raonslab2/fcBoardKicad/out/hierarchical_board/report.md

# HierarchicalBoard Build Report

**Generated:** 2025-12-12 09:06:19
**KiCad Version:** 9

## Summary

| Metric | Count |
|---|---|
| Total Parts | 13 |
| Active Parts | 11 |
| DNP Parts | 2 |
| With LCSC # | 4 |
| With MPN | 3 |

## Parts by Type

| Type | Count |
|---|---|
| C | 4 |
| D | 1 |
| J | 2 |
| L | 1 |
| R | 2 |
| U | 1 |

## Parts List

| Ref | Value | Role | LCSC | MPN | DNP |
|-----|---|---|---|-----|-----|
| C1 | 220uF | capacitor_pol | C134799 | - |  |
| C2 | 220uF | capacitor_pol | C134799 | - |  |
| C3 | 100nF | capacitor | - | - |  |
| C4 | 10uF | capacitor | - | - |  |
| D1 | SS34 | diode | - | - |  |
| D2 | Green | led | - | - | Yes |
| J1 | DC Jack 12V | input_conn | - | - |  |
| J2 | USB-A | usb_a | - | - |  |
| L1 | 33uH | inductor | - | - |  |
| R1 | 1k | resistor | - | - | Yes |
| R2 | 22R | resistor | C17560 | RC0402FR-0722RL |  |
| R3 | 22R | resistor | C17560 | RC0402FR-0722RL |  |
| U1 | LM2596S-5.0 | buck_5v | - | LM2596S-5.0/NOPB |  |

## DNP Parts (Do Not Populate)

| Ref | Value | Role |
|-----|---|---|
| D2 | Green | led |
| R1 | 1k | resistor |

## Hierarchical Sheets

| Sheet | Parts | Ports |
|---|---|---|
| Power | 8 | +12V, +5V, +3V3... |
| USB | 5 | +5V, GND, USB_DP... |
