raonslab2/fcBoardKicad/out/hierarchical_ports_obj/report.md

# HierarchicalPortsObj Build Report

**Generated:** 2025-12-12 09:22:37
**Builder Version:** 1.3.0
**KiCad Version:** 9

## Summary

| Metric | Count |
|---|---|
| Total Parts | 7 |
| Active Parts | 7 |
| DNP Parts | 0 |
| With LCSC # | 2 |
| With MPN | 1 |

## Parts by Type

| Type | Count |
|---|---|
| C | 3 |
| J | 1 |
| R | 2 |
| U | 1 |

## Parts List

| Ref | Value | Role | LCSC | MPN | DNP |
|-----|---|---|---|-----|-----|
| C1 | 220uF | capacitor_pol | - | - |  |
| C2 | 220uF | capacitor_pol | - | - |  |
| C3 | 100nF | capacitor | - | - |  |
| J1 | DC Jack | input_conn | - | - |  |
| R1 | 10k | resistor | C17414 | - |  |
| R2 | 10k | resistor | C17414 | - |  |
| U1 | LM2596S-5.0 | buck_5v | - | LM2596S-5.0/NOPB |  |

## Hierarchical Sheets

| Sheet | Parts | Ports |
|---|---|---|
| Power | 4 | +12V, GND, +5V... |
| Digital | 3 | +5V, +3V3, GND... |
