raonslab2/fcBoardKicad/docs/ACU5EV/ACU5EV_Schematic.pdf

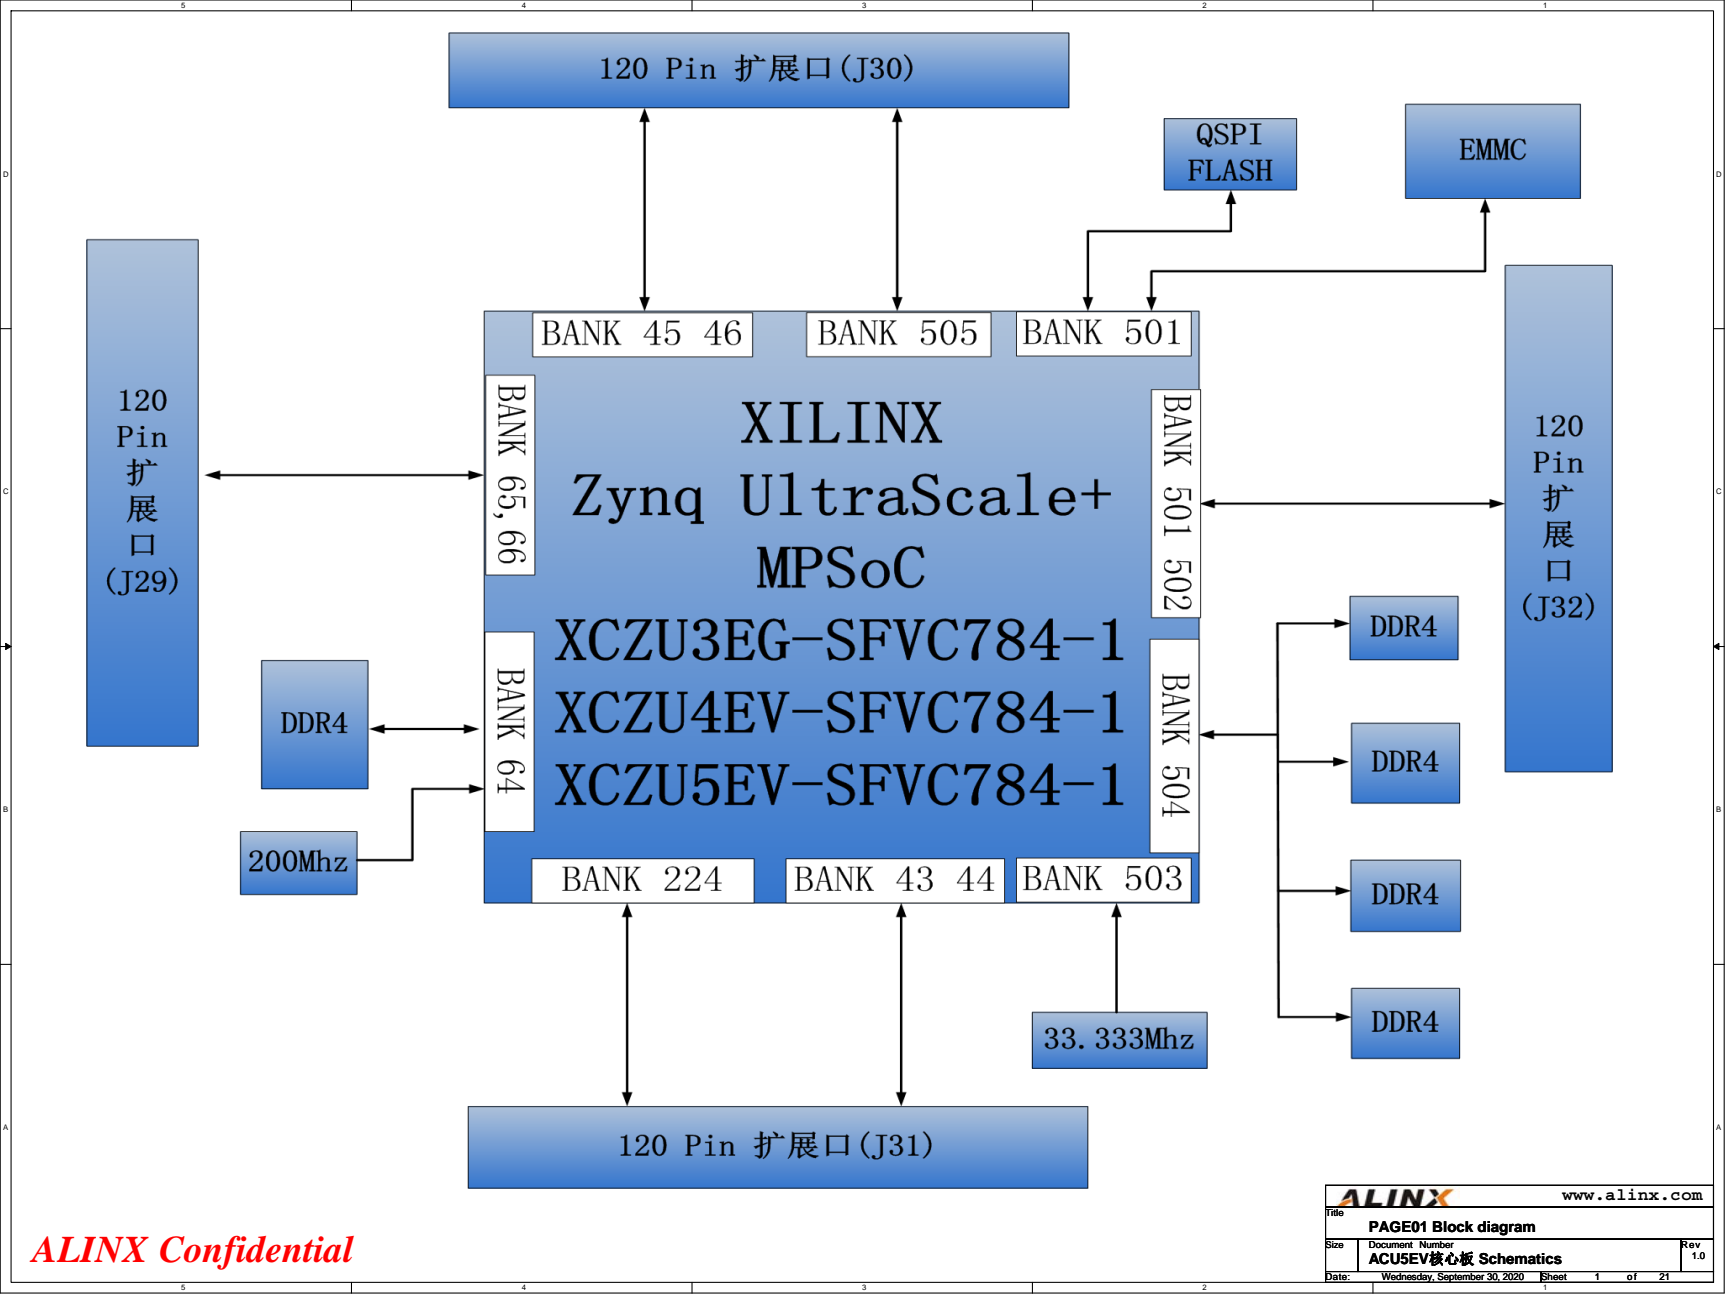
[picture p16: page 1]
ALINX Confidential; Title; PAGE01 Block diagram

www.alinx.com

Size | Document Number ACU5EV核心板 Schematics | Rev 1.0

Date: Wednesday, September 30, 2020 Wednesday, September 30, 2020 Wednesday, September 30, 2020 | Sheet 1 1 1 of 21 21 21

# MODE[3:0]

0000 | PS JTAG | PS JTAG Interface

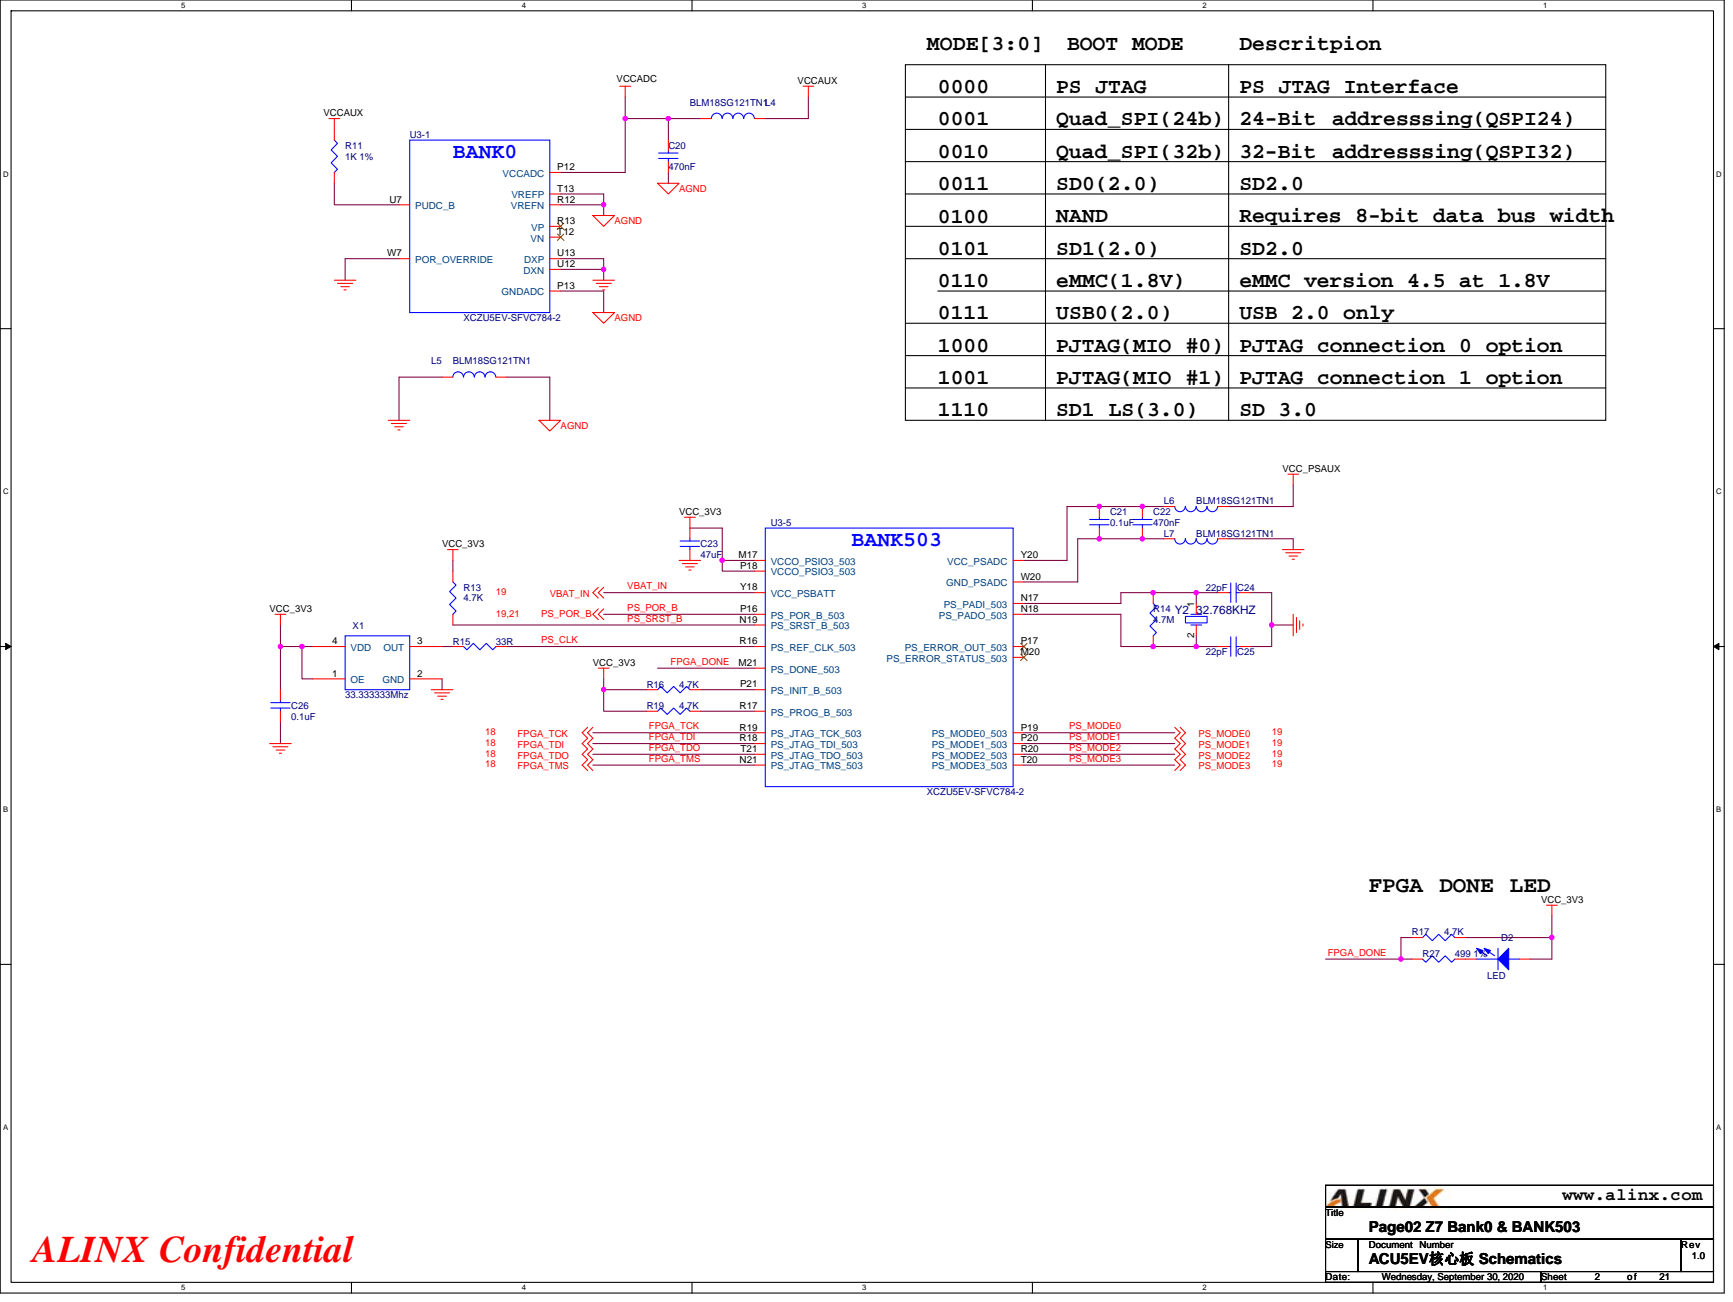
[picture p17: page 2]

0001 | Quad_SPI(24b) | 24-Bit addresssing(QSPI24)
0010 | Quad_SPI(32b) | 32-Bit addresssing(QSPI32)
0011 | SD0(2.0) | SD2.0
0100 | NAND | Requires 8-bit data bus width
0101 | SD1(2.0) | SD2.0
0110 0111 | eMMC(1.8V) USB0(2.0) | eMMC version 4.5 at 1.8V USB 2.0 only

1000 | PJTAG(MIO #0) | PJTAG connection 0 option
1001 | PJTAG(MIO #1) | PJTAG connection 1 option
1110 | SD1 LS(3.0) | SD 3.0

## VCC1V8

0.1uF | BANK500

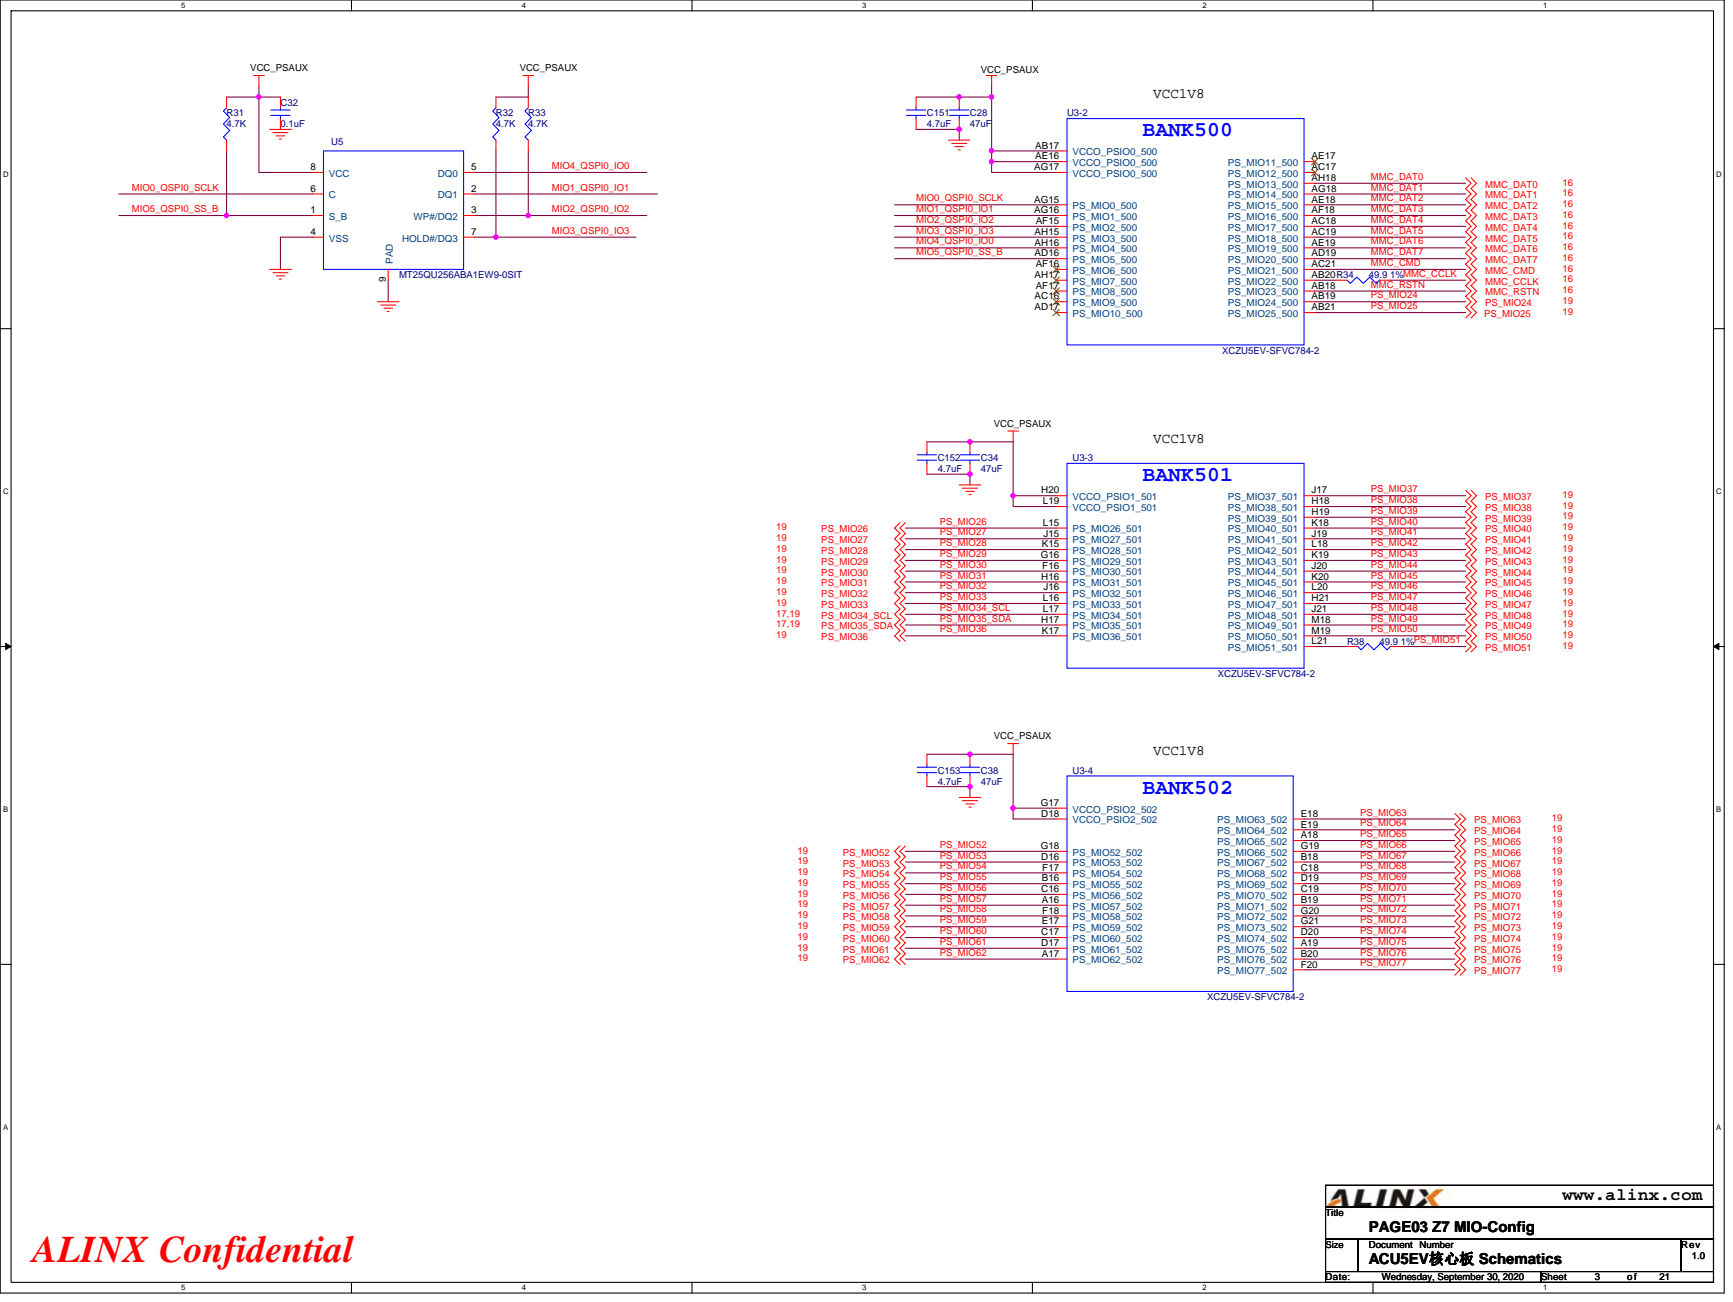
[picture p18: page 3]

# BANK43

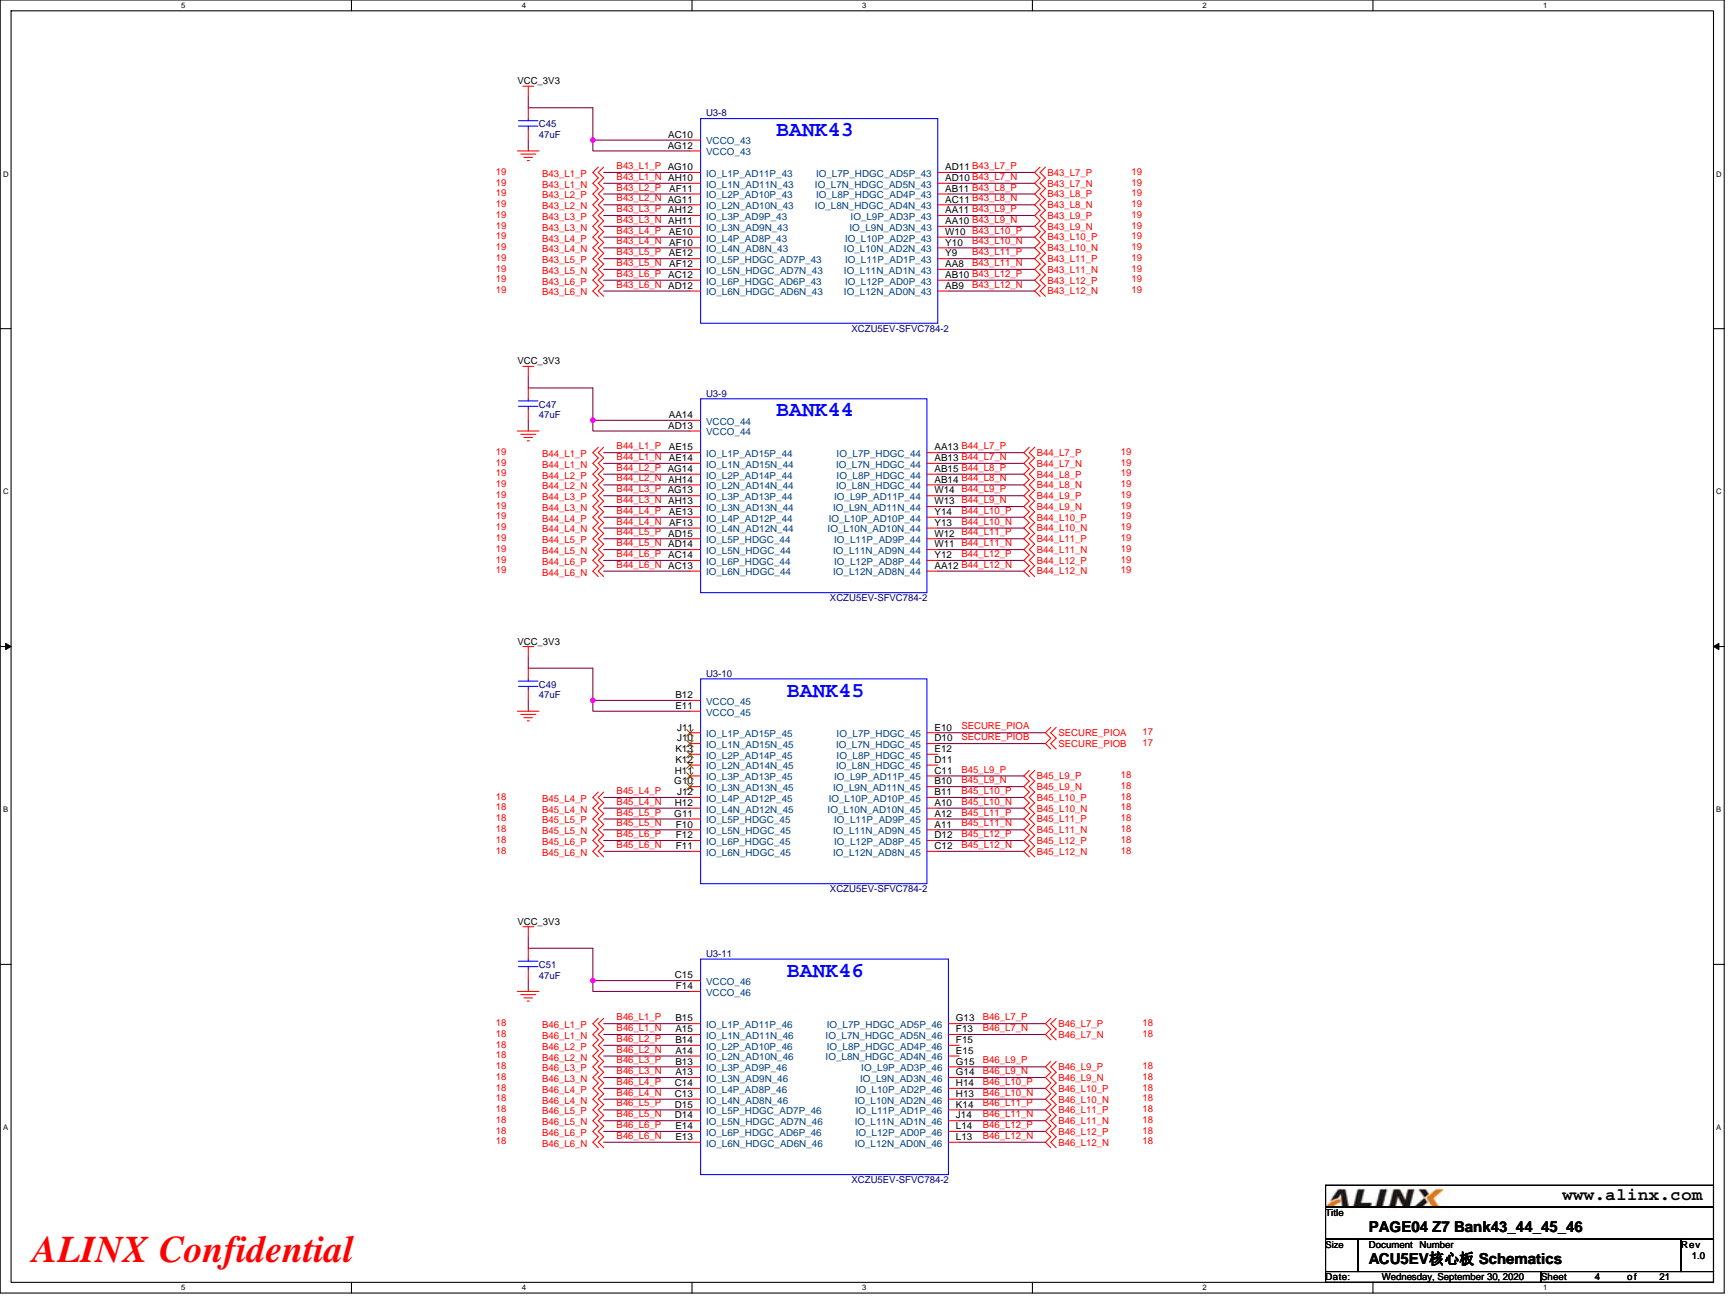
[picture p19: page 4]

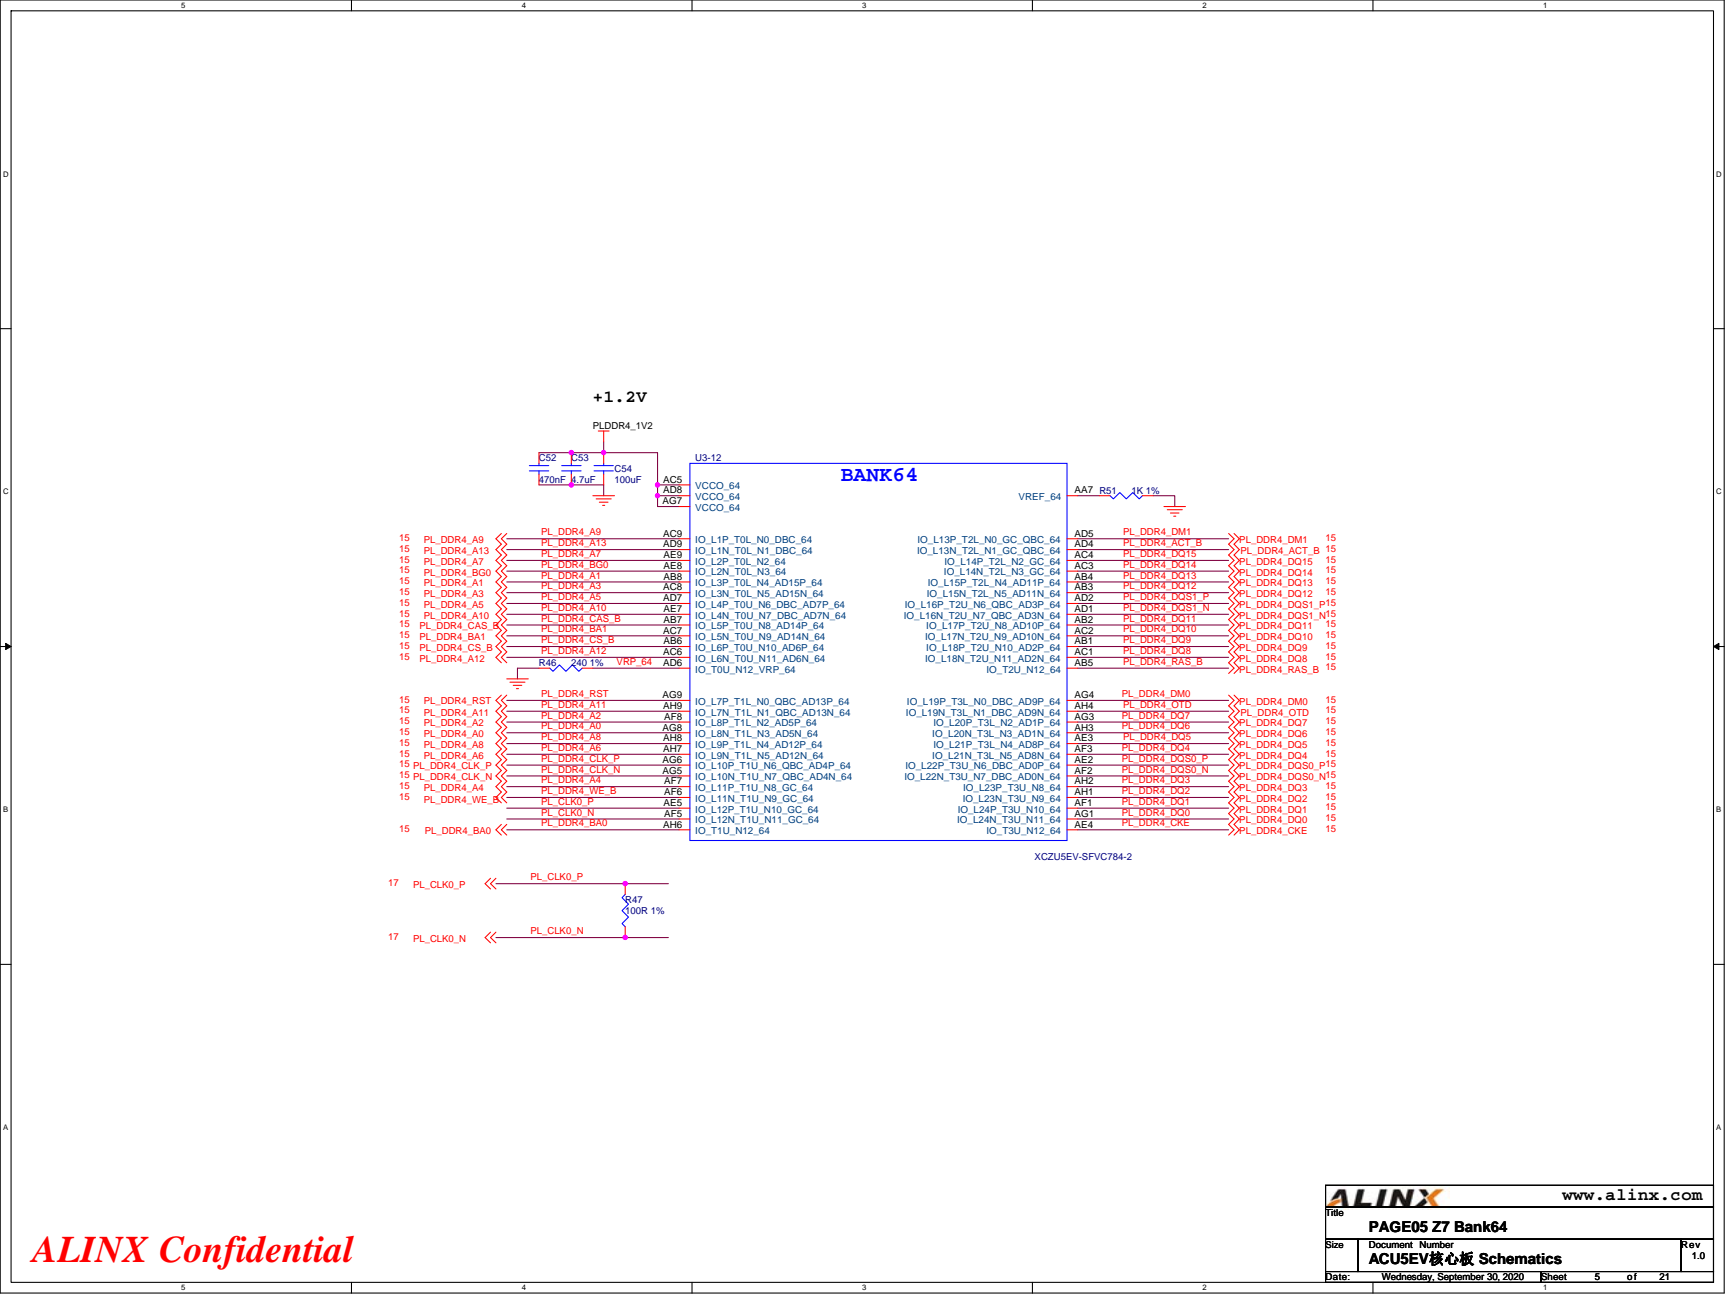
[picture p20: page 5]
VRP_64; PL_DDR4_A0; PL_DDR4_CLK_P PL_DDR4_CLK_N; PL_CLK0_P PL_CLK0_N; PL_CLK0_N; PL_CLK0_P; PL_DDR4_DM1; PL_DDR4_DQ0; PL_DDR4_DQ7 PL_DDR4_DQ6; PL_DDR4_DQS0_P; PL_DDR4_DQ1; PL_DDR4_DQS0_N; PL_DDR4_DQ2; PL_DDR4_DQ5 PL_DDR4_DQ4; PL_DDR4_DQ3; PL_DDR4_DM0; PL_DDR4_DQ15 PL_DDR4_DQ14 PL_DDR4_DQ13 PL_DDR4_DQ12; PL_DDR4_DQ11 PL_DDR4_DQ10 PL_DDR4_DQ9 PL_DDR4_DQ8; PL_DDR4_DQS1_P PL_DDR4_DQS1_N; PL_DDR4_OTD; PL_DDR4_A6; PL_DDR4_BA1; PL_DDR4_A9; PL_DDR4_A5; PL_DDR4_CS_B; PL_DDR4_BA0; PL_DDR4_A13 PL_DDR4_A7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

www.alinx.com

# BANK65

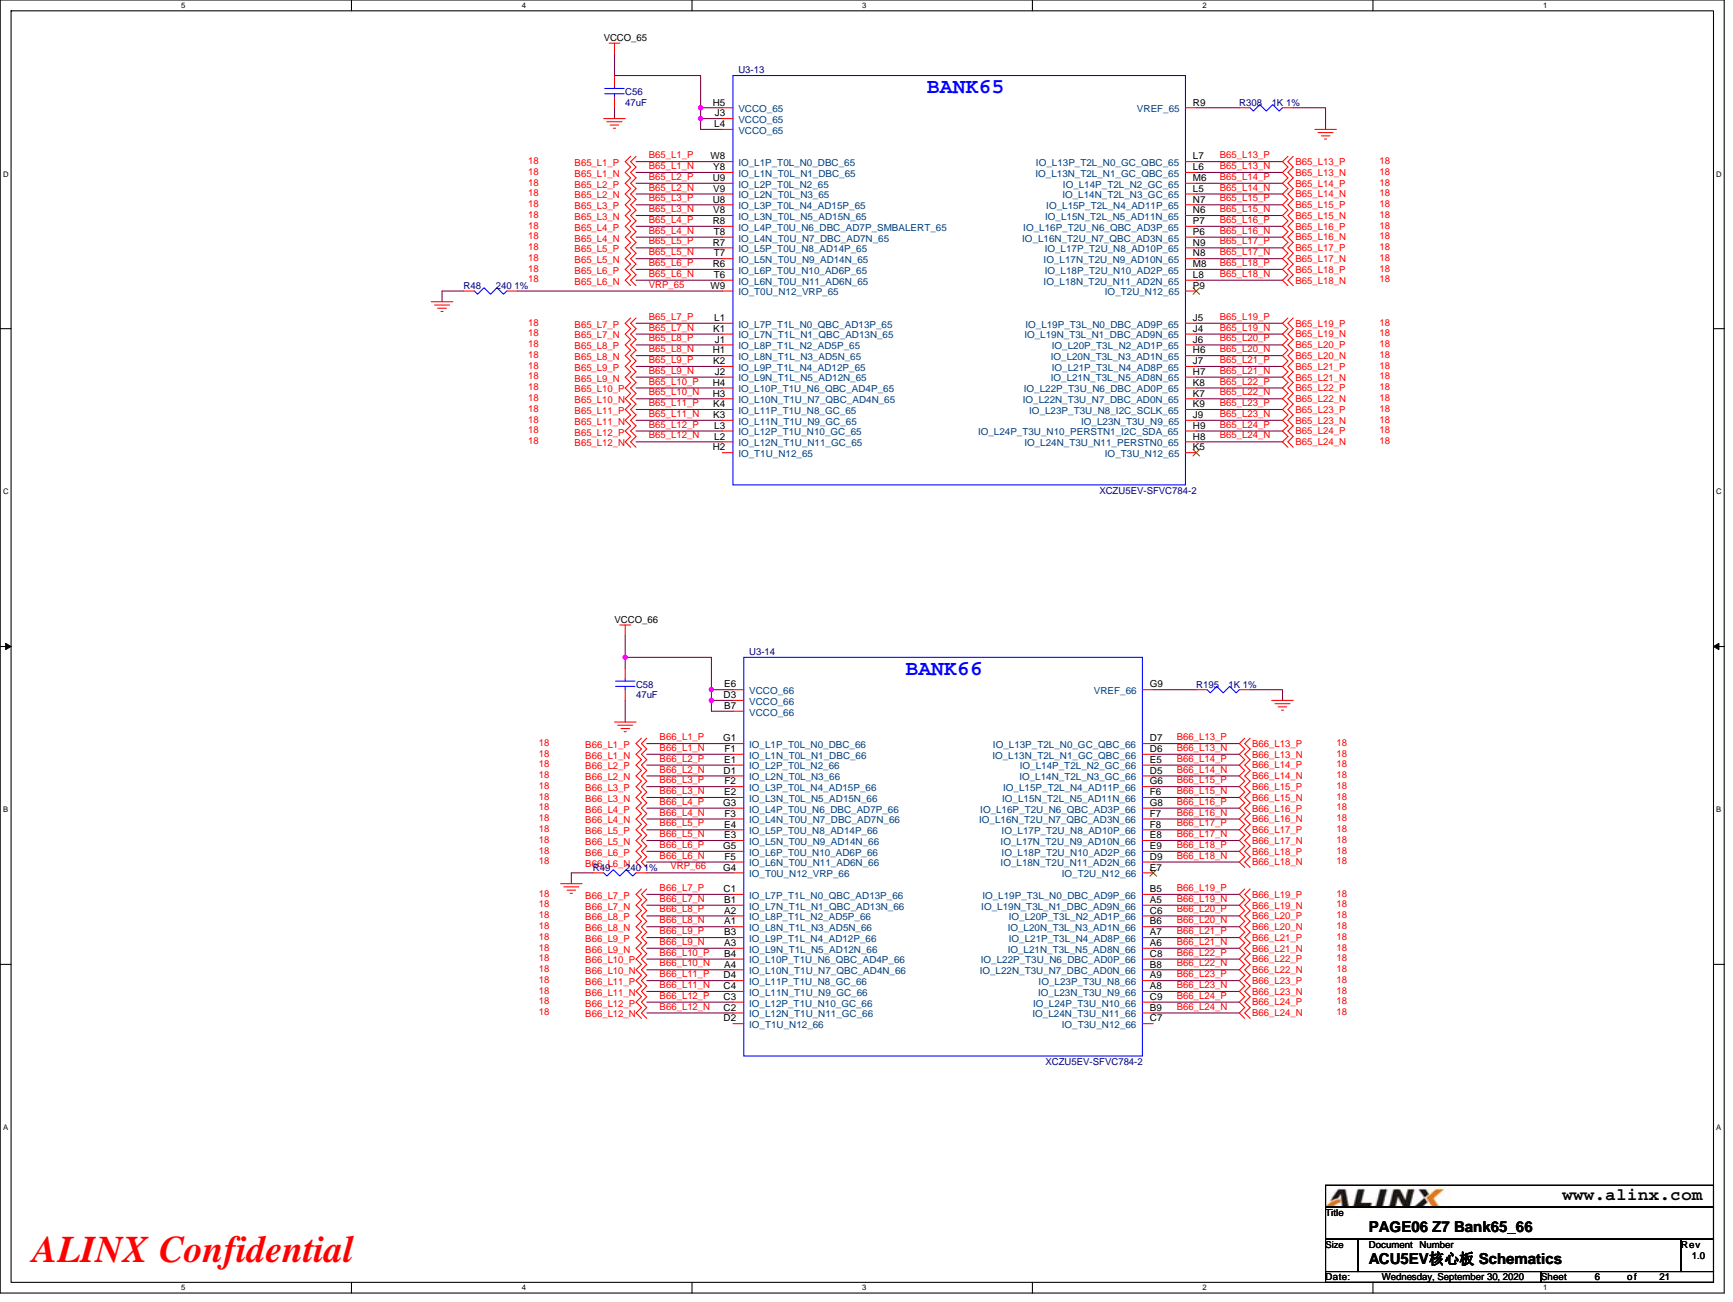
[picture p21: page 6]

# BANK505 PS MGT

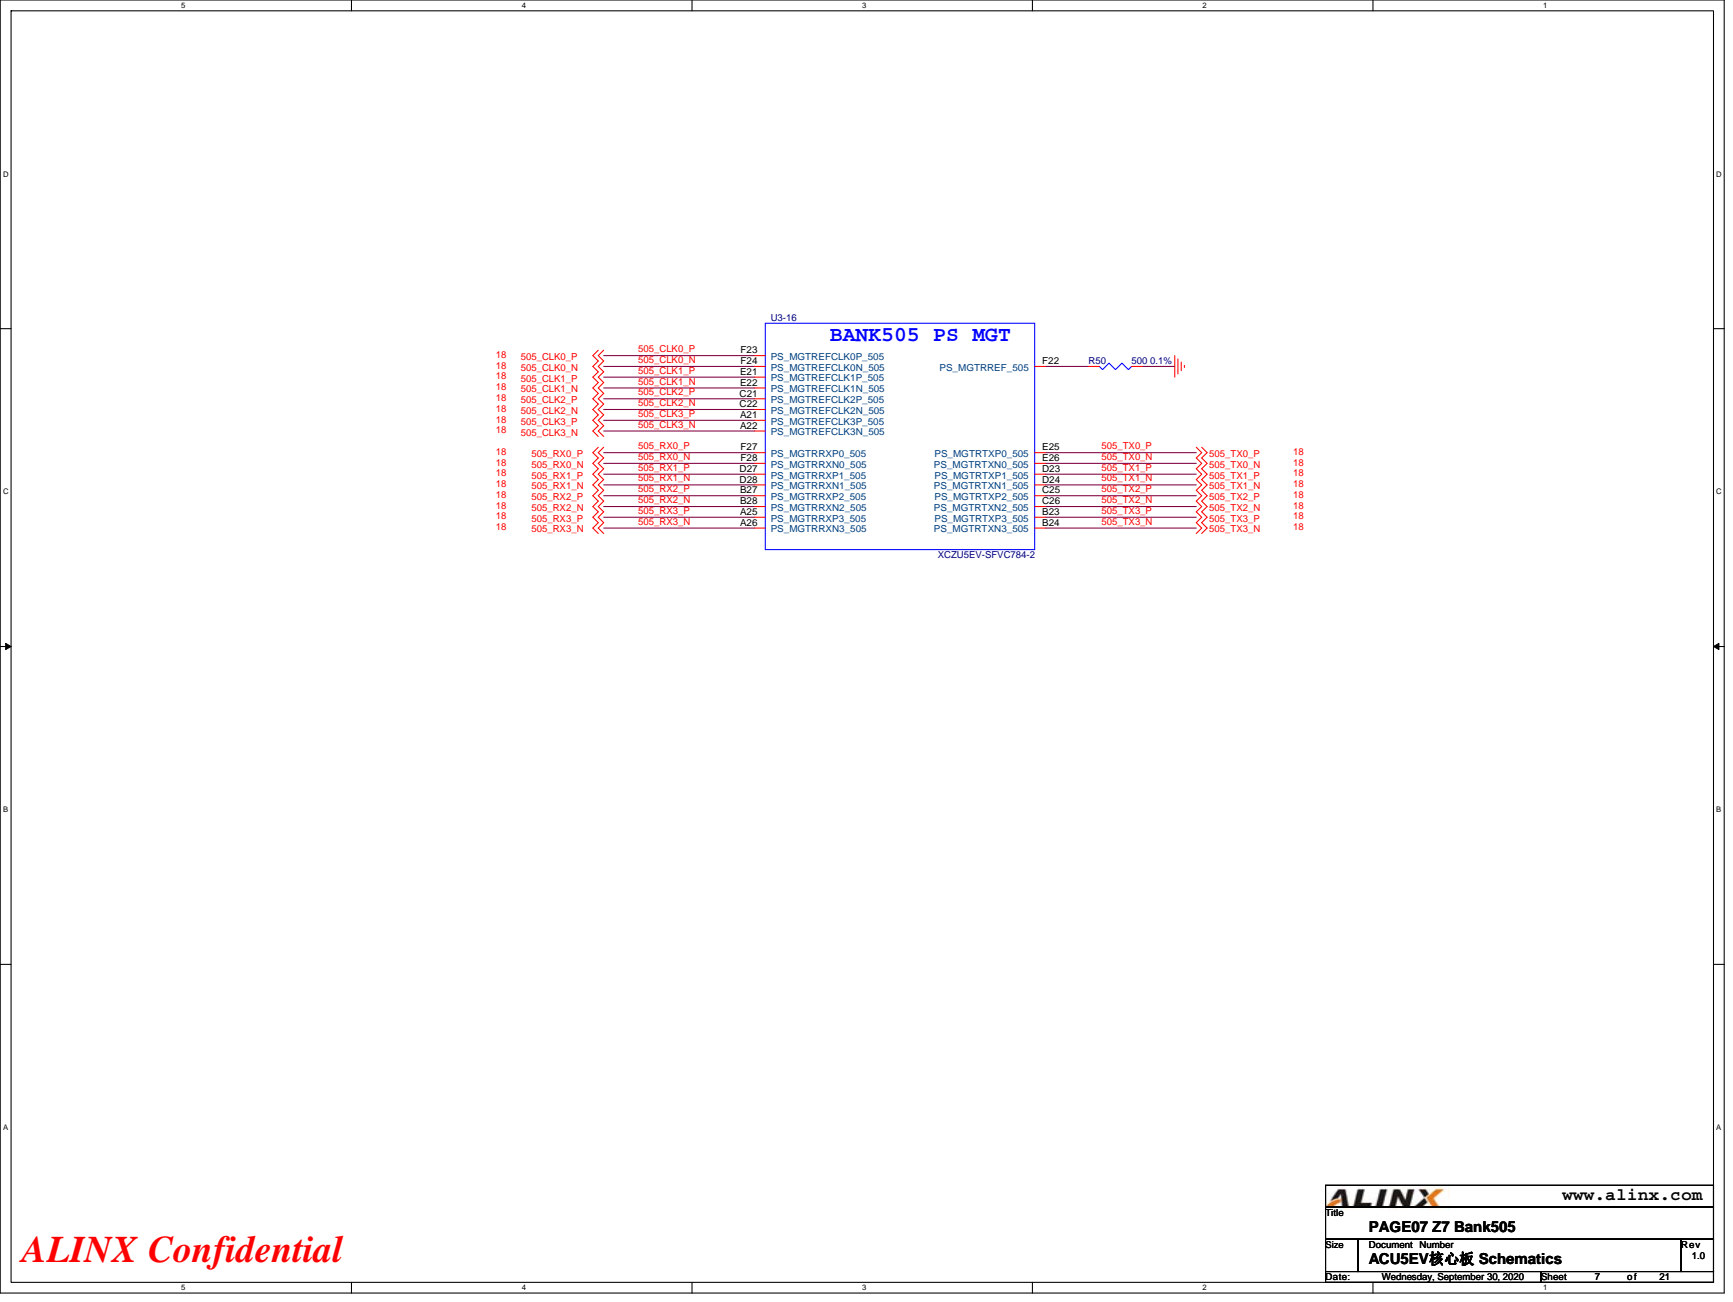
[picture p22: page 7]

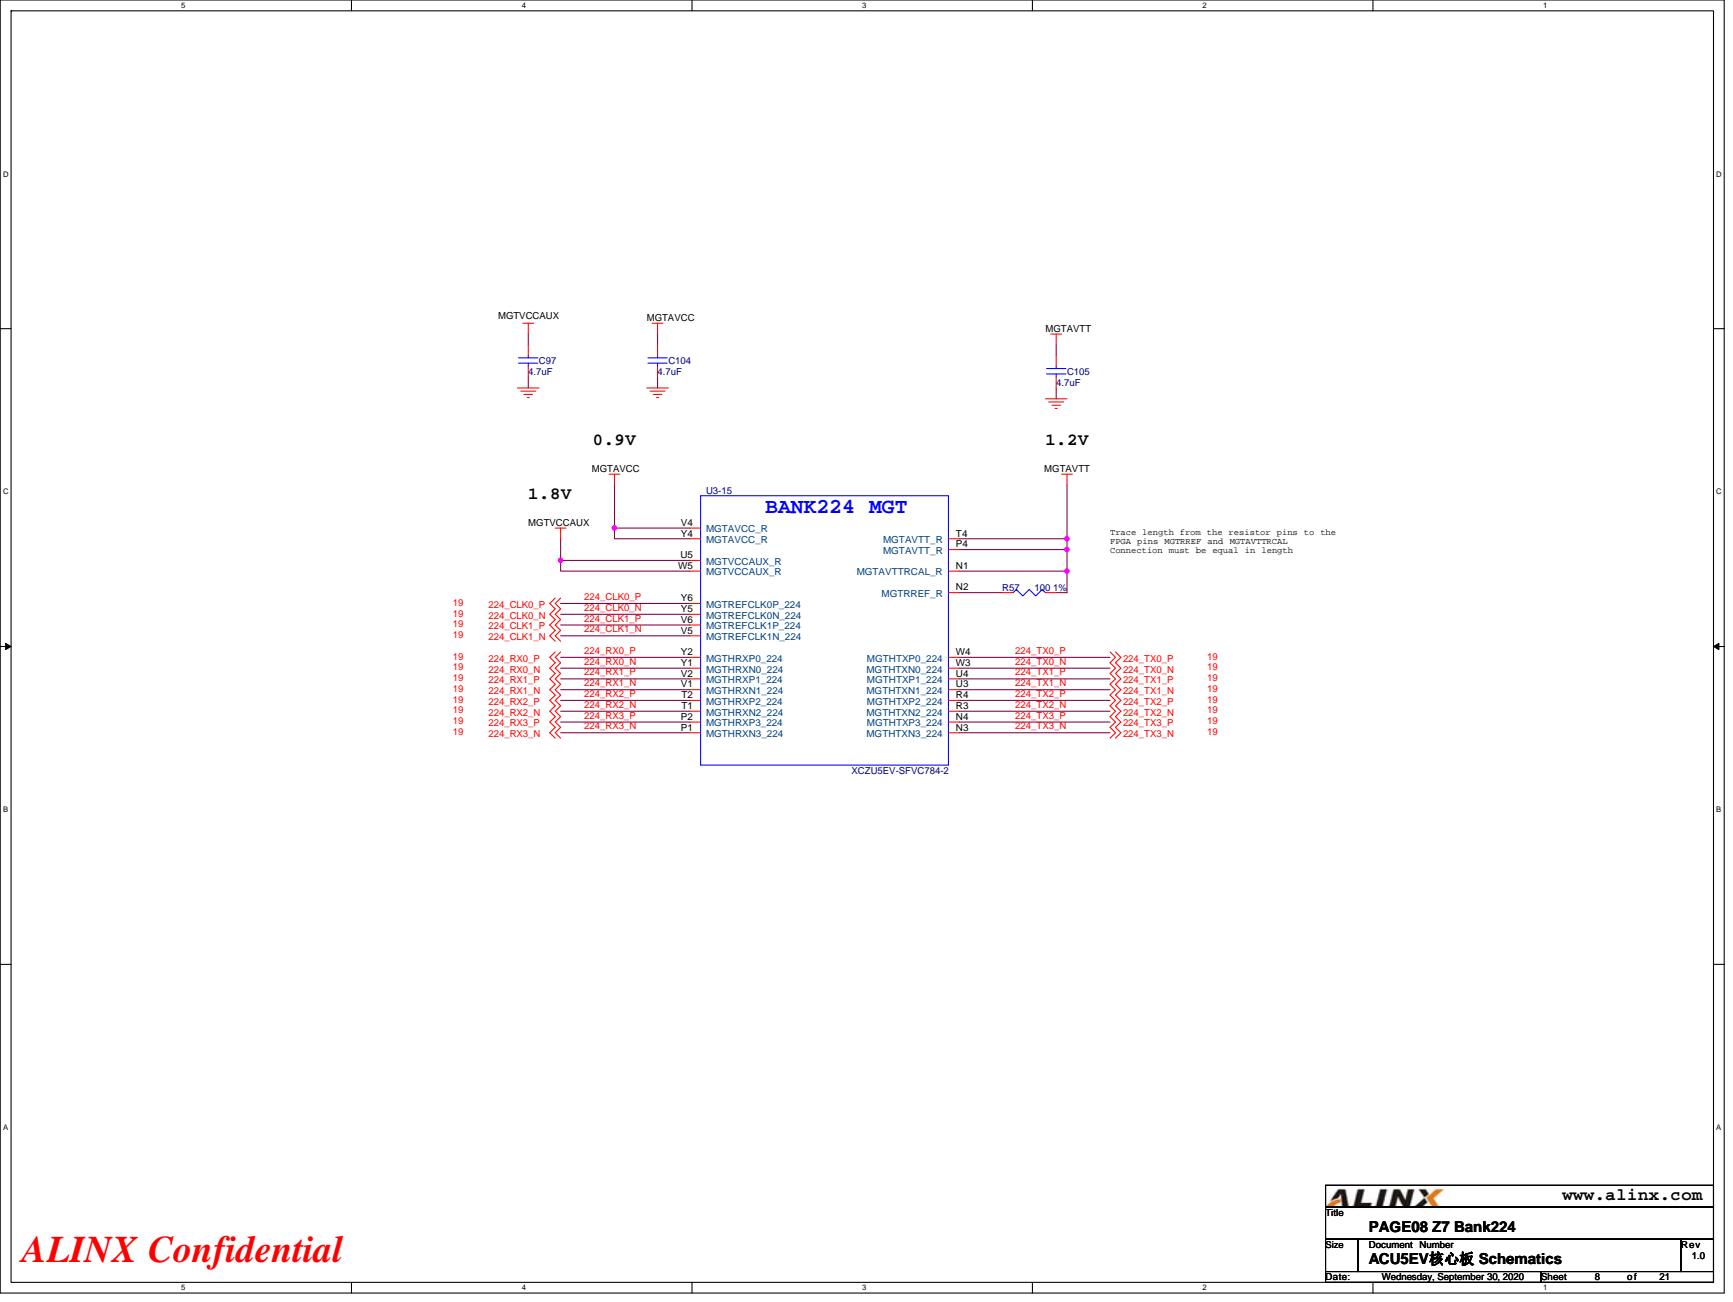
[picture p23: page 8]

Trace length from the resistor pins to the
FPGA pins MGTRREF and MGTAVTTRCAL
Connection must be equal in length

1.2V
1.2V

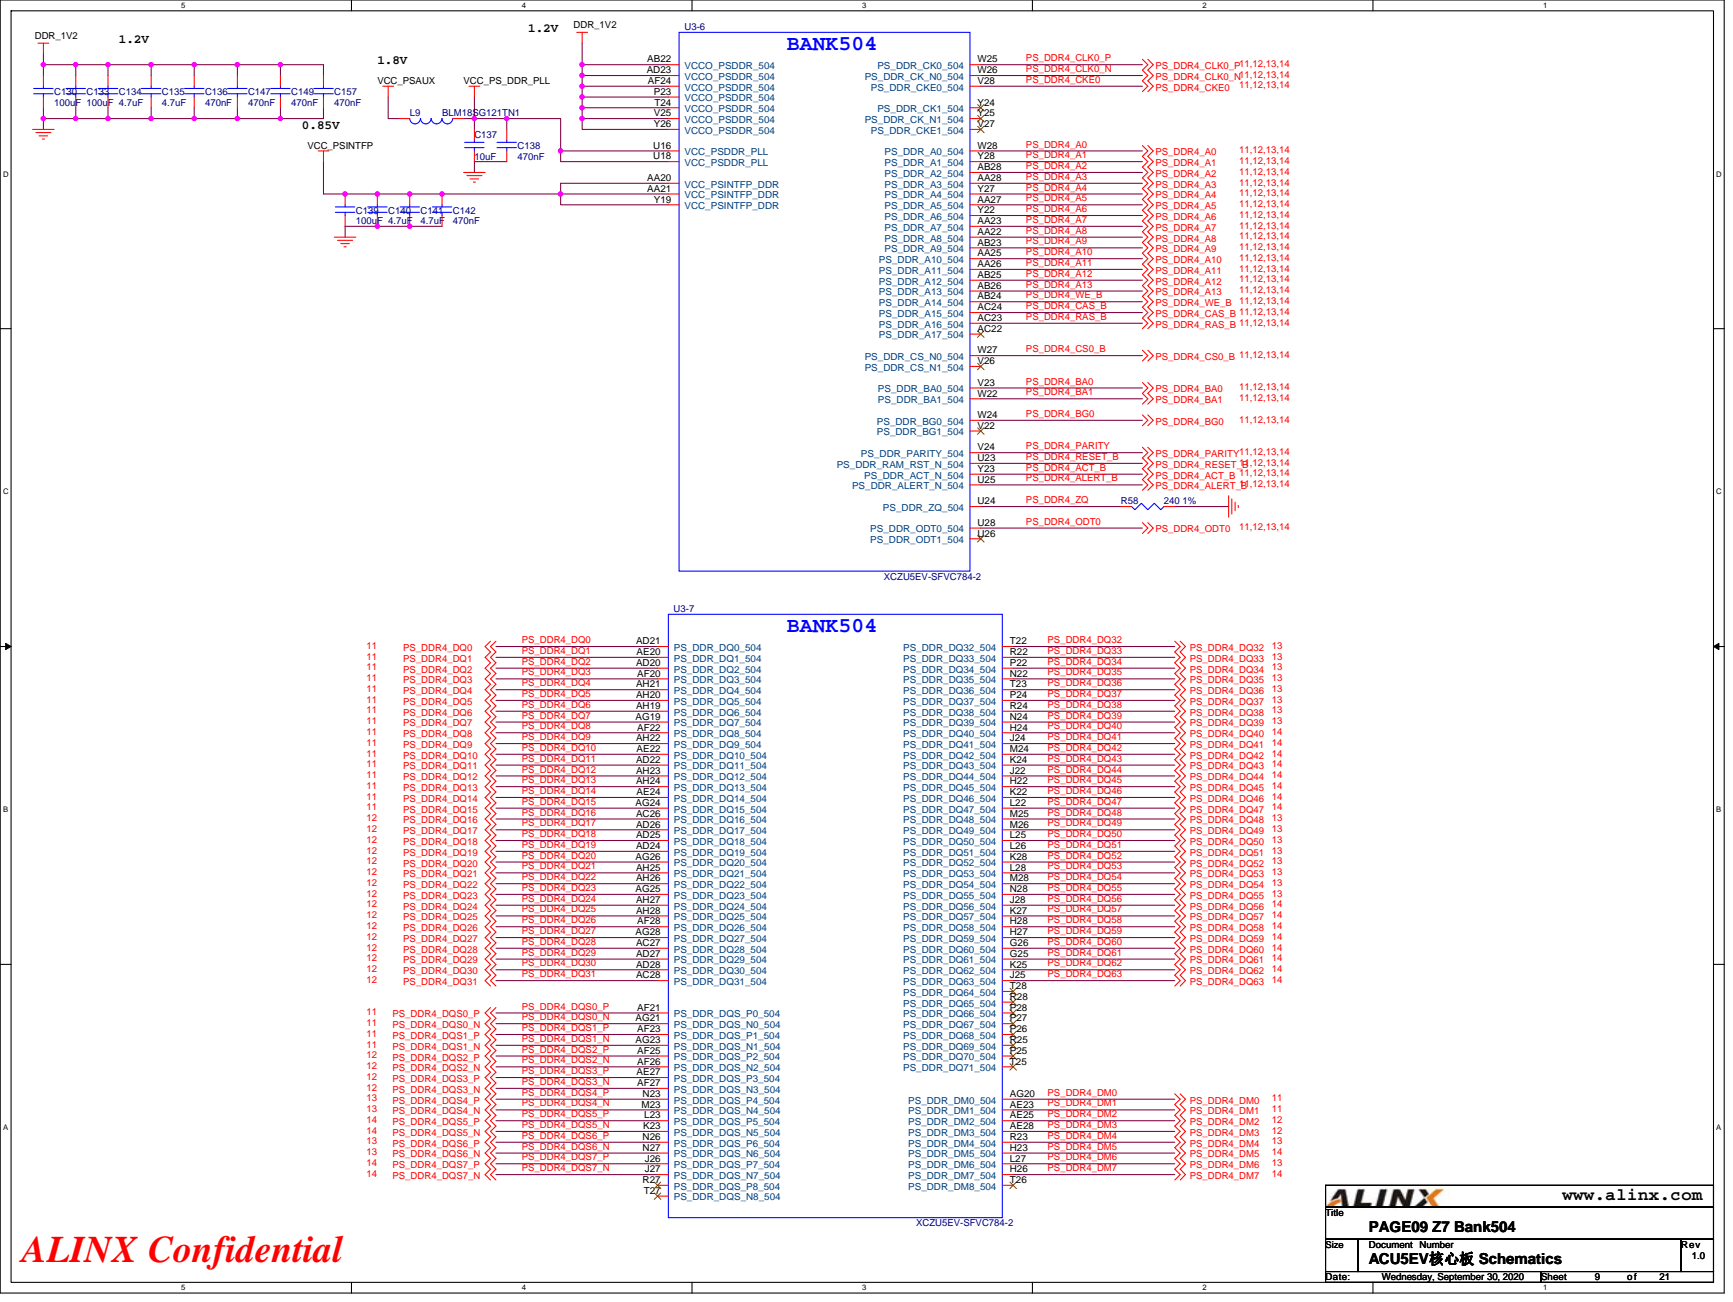
[picture p24: page 9]

0.85V

0.85V

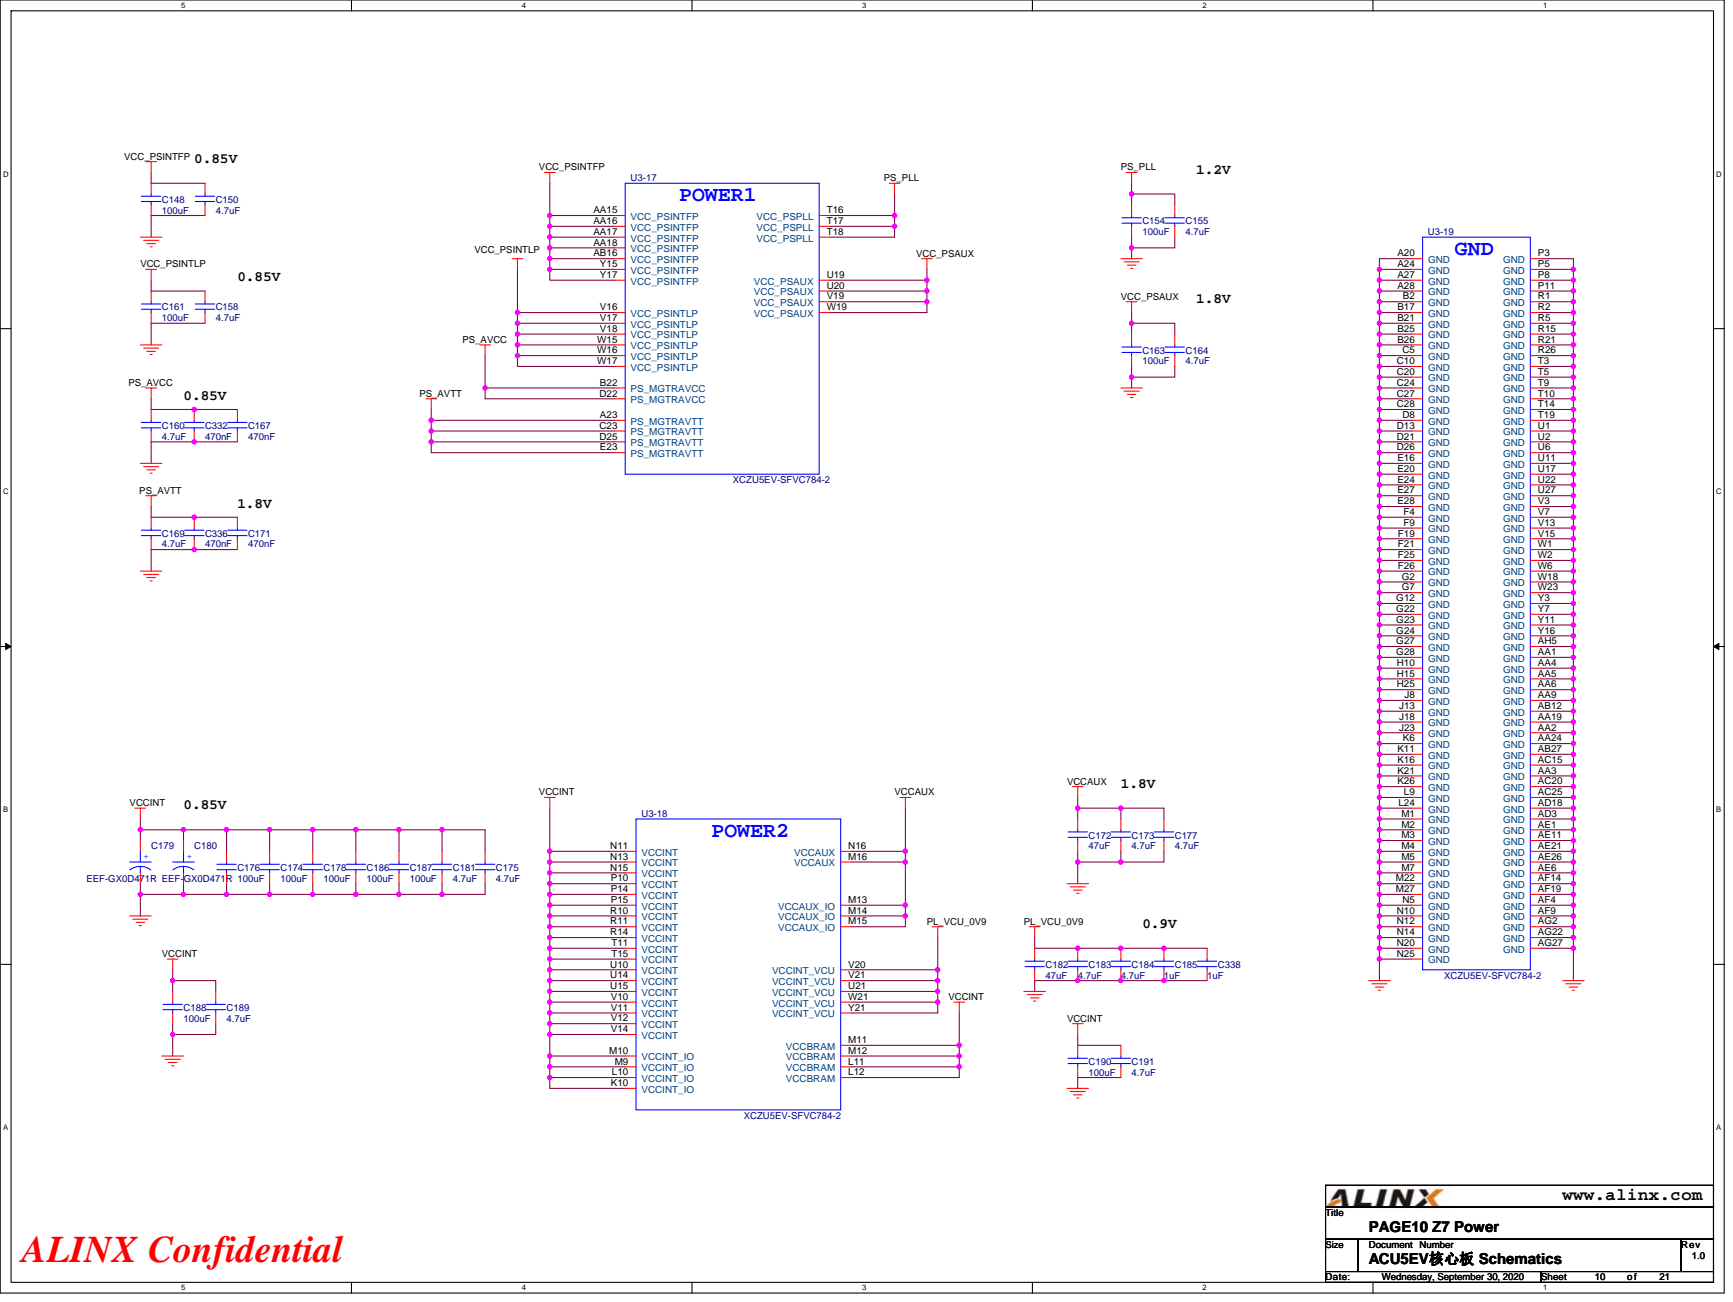
[picture p25: page 10]

1.2V

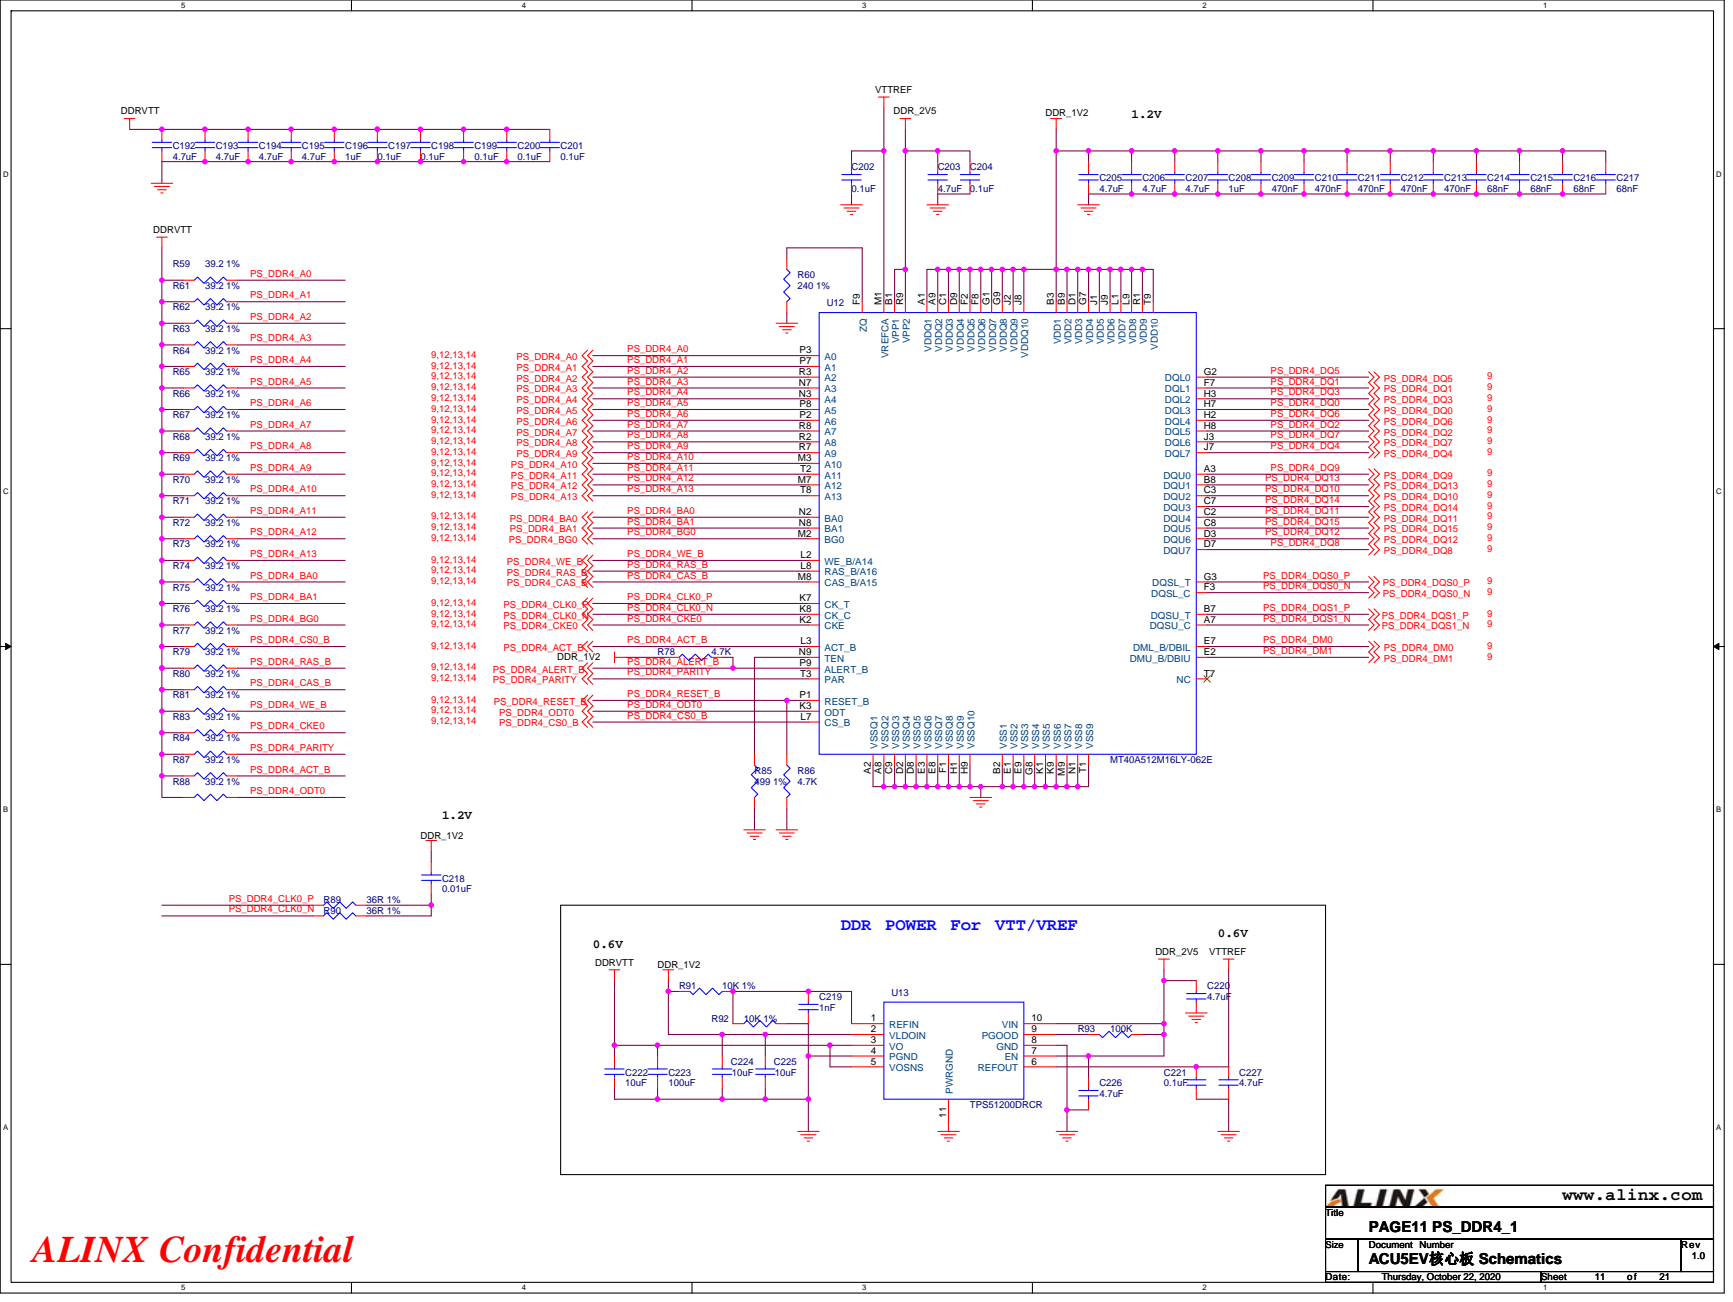
[picture p26: page 11]

1.2V

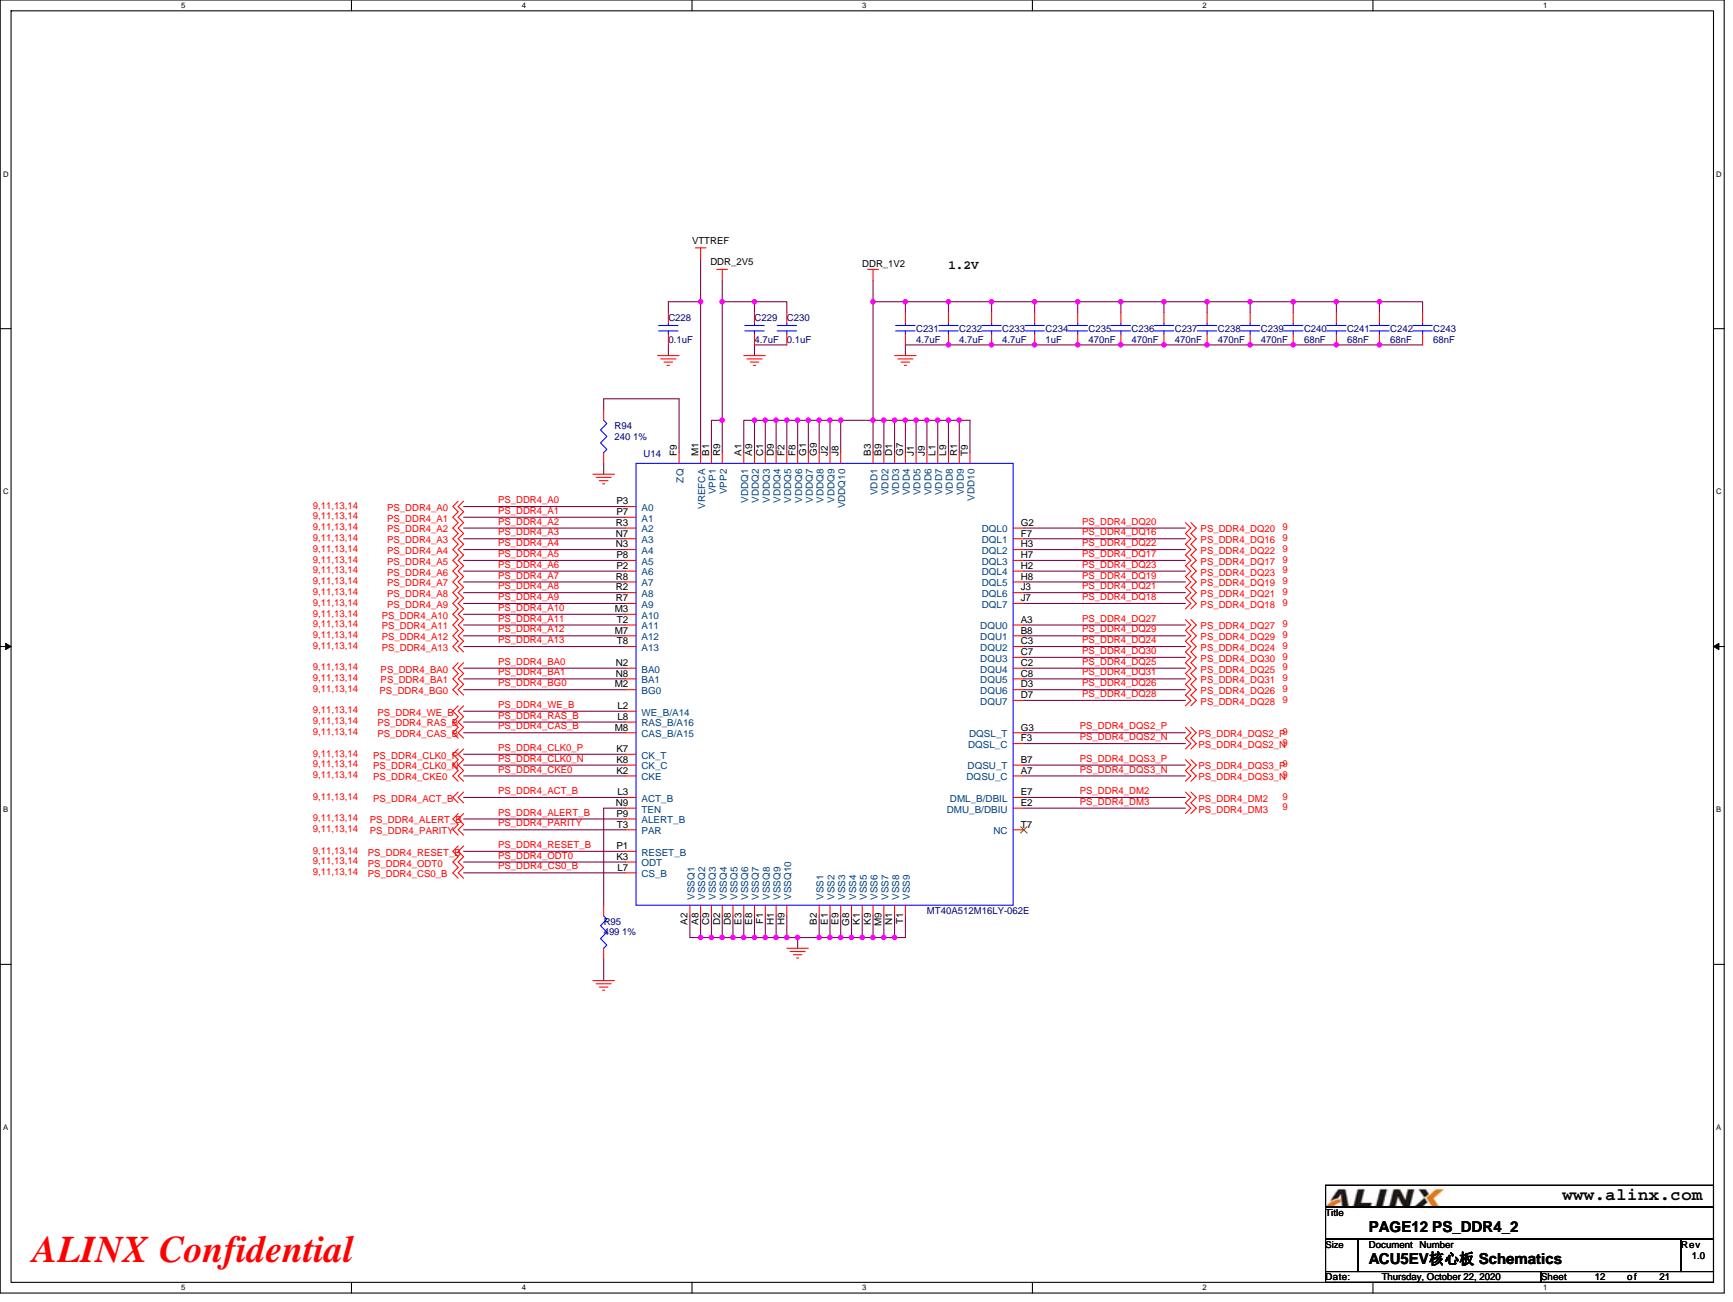
[picture p27: page 12]

1.2V

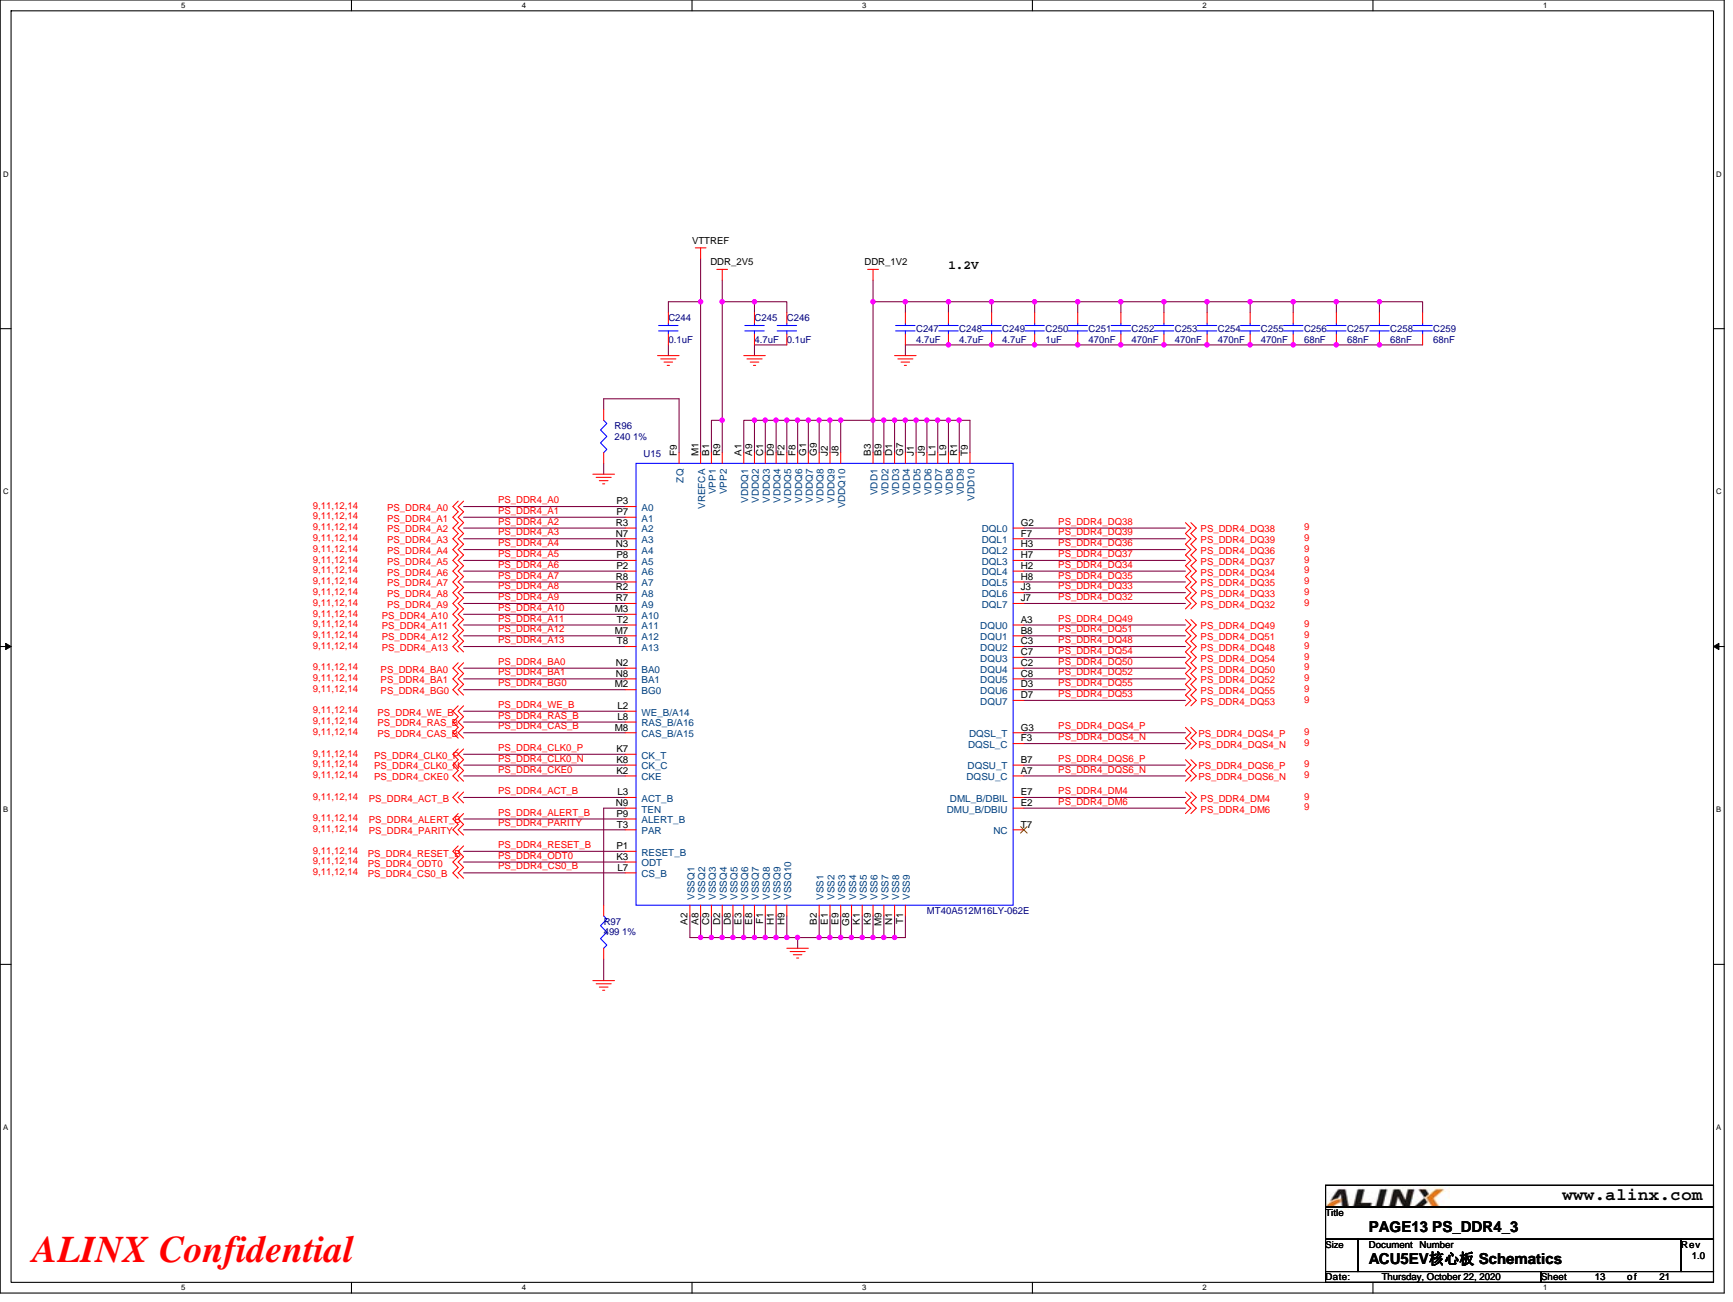
[picture p28: page 13]

1.2V

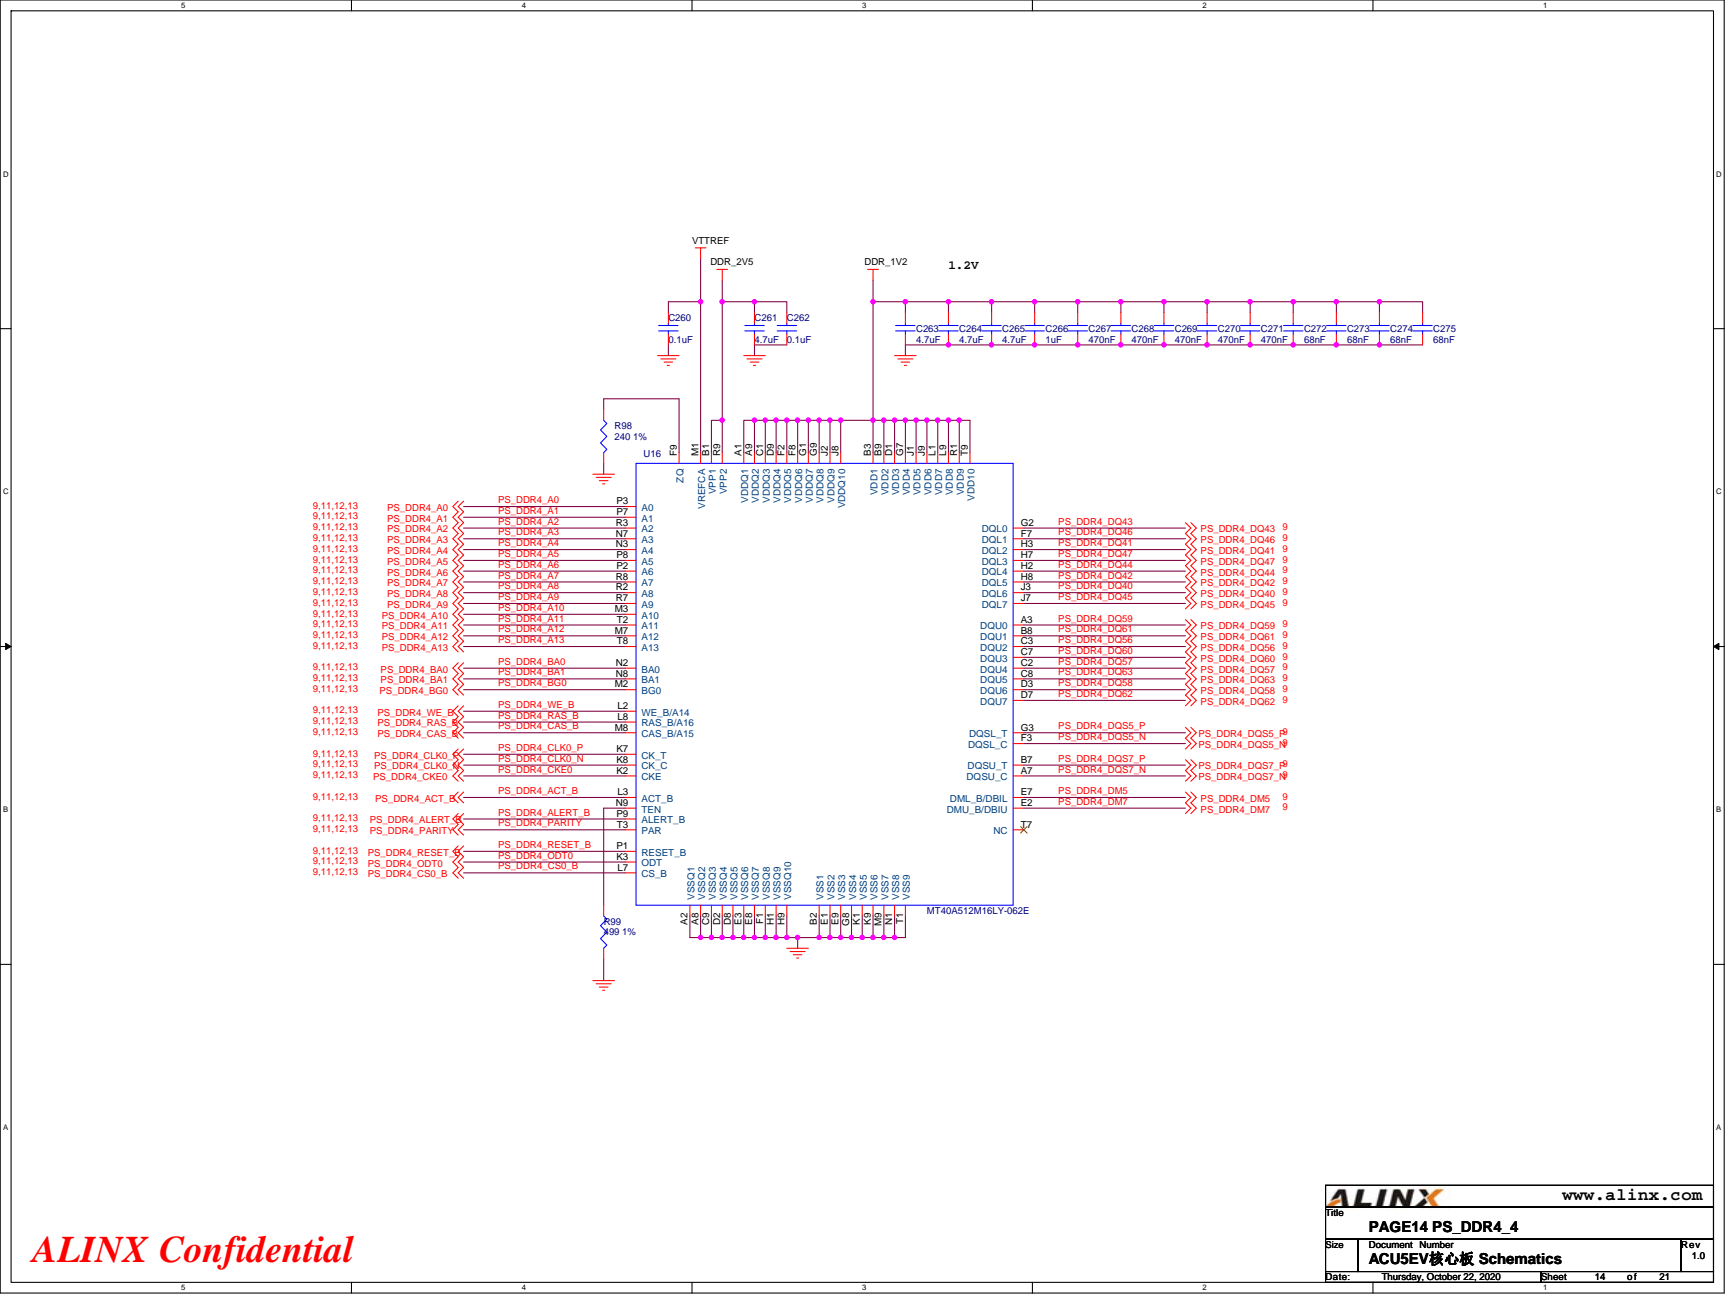
[picture p29: page 14]

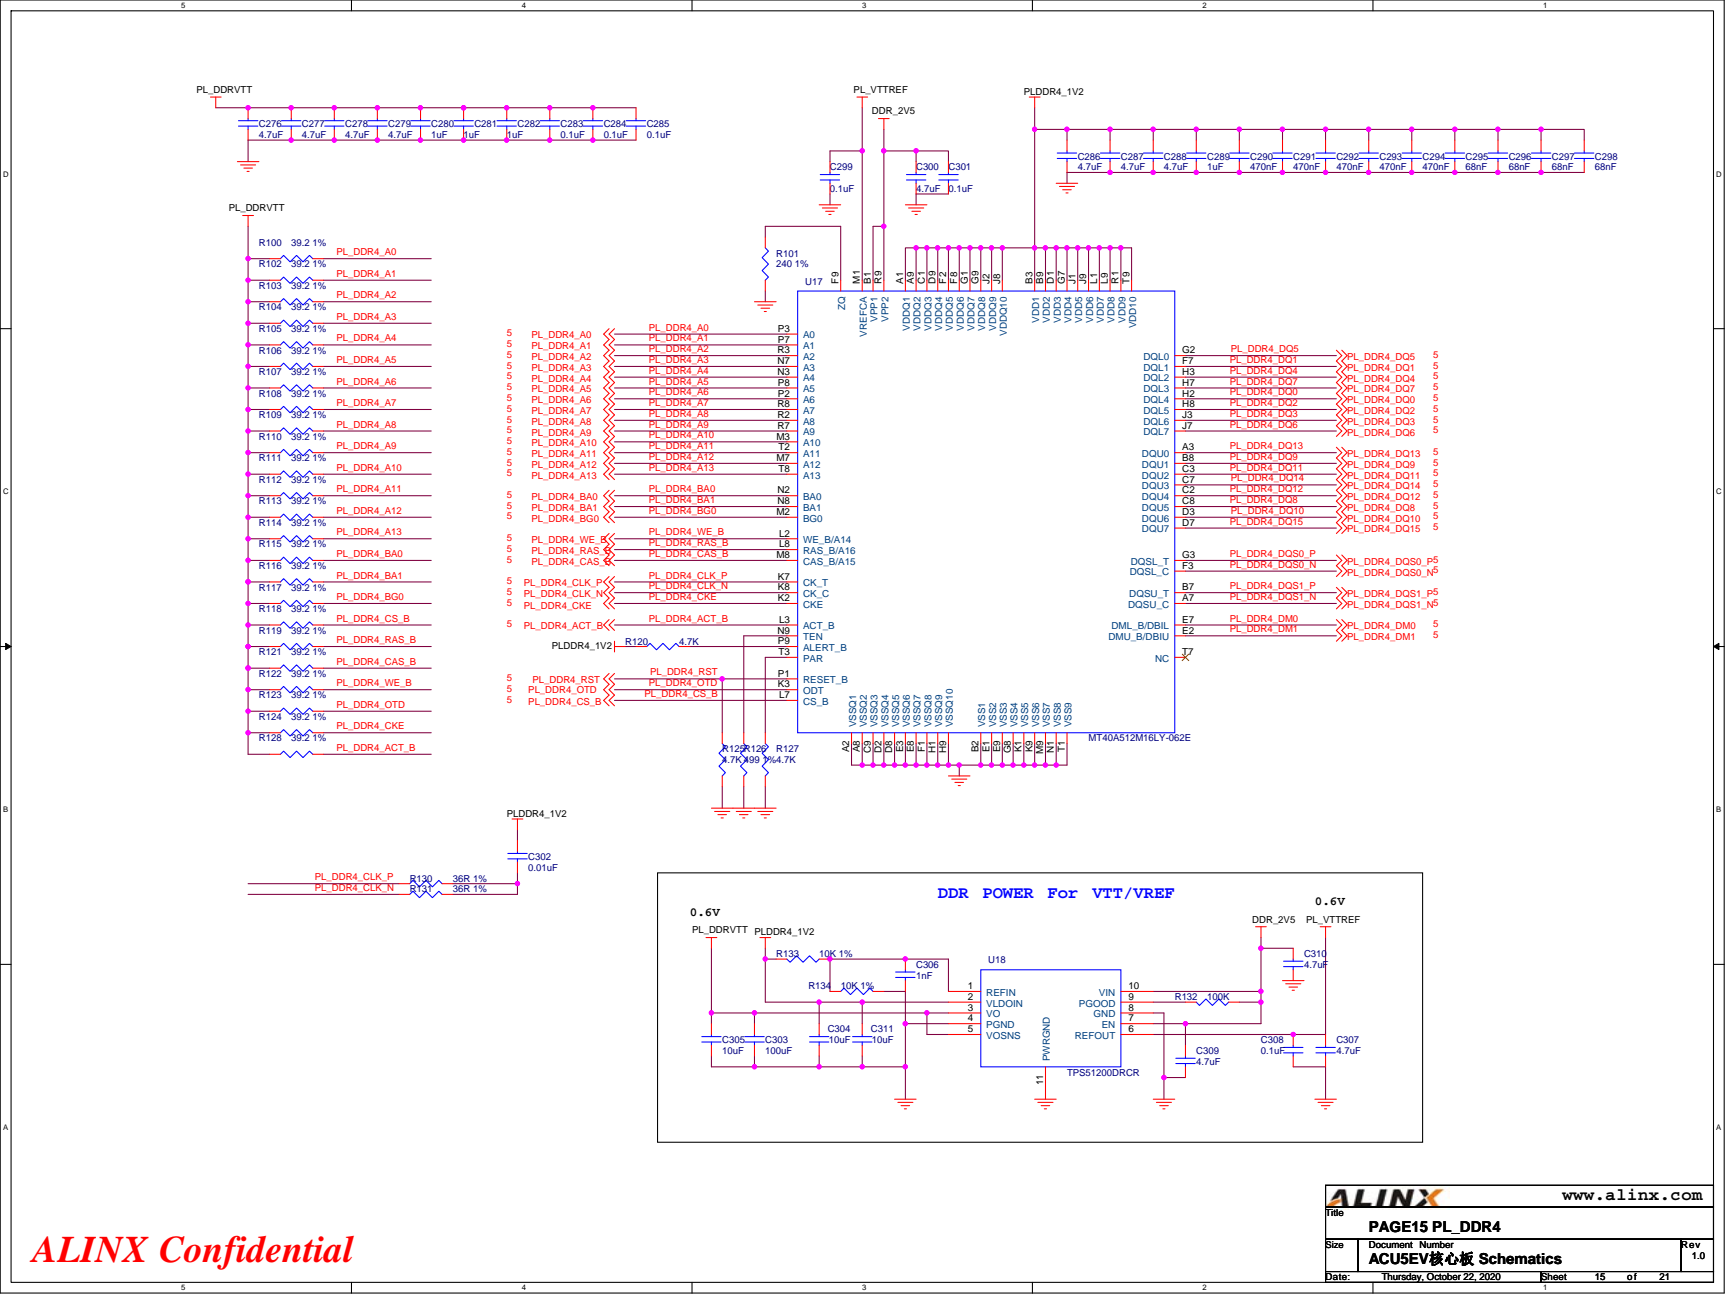
[picture p30: page 15]

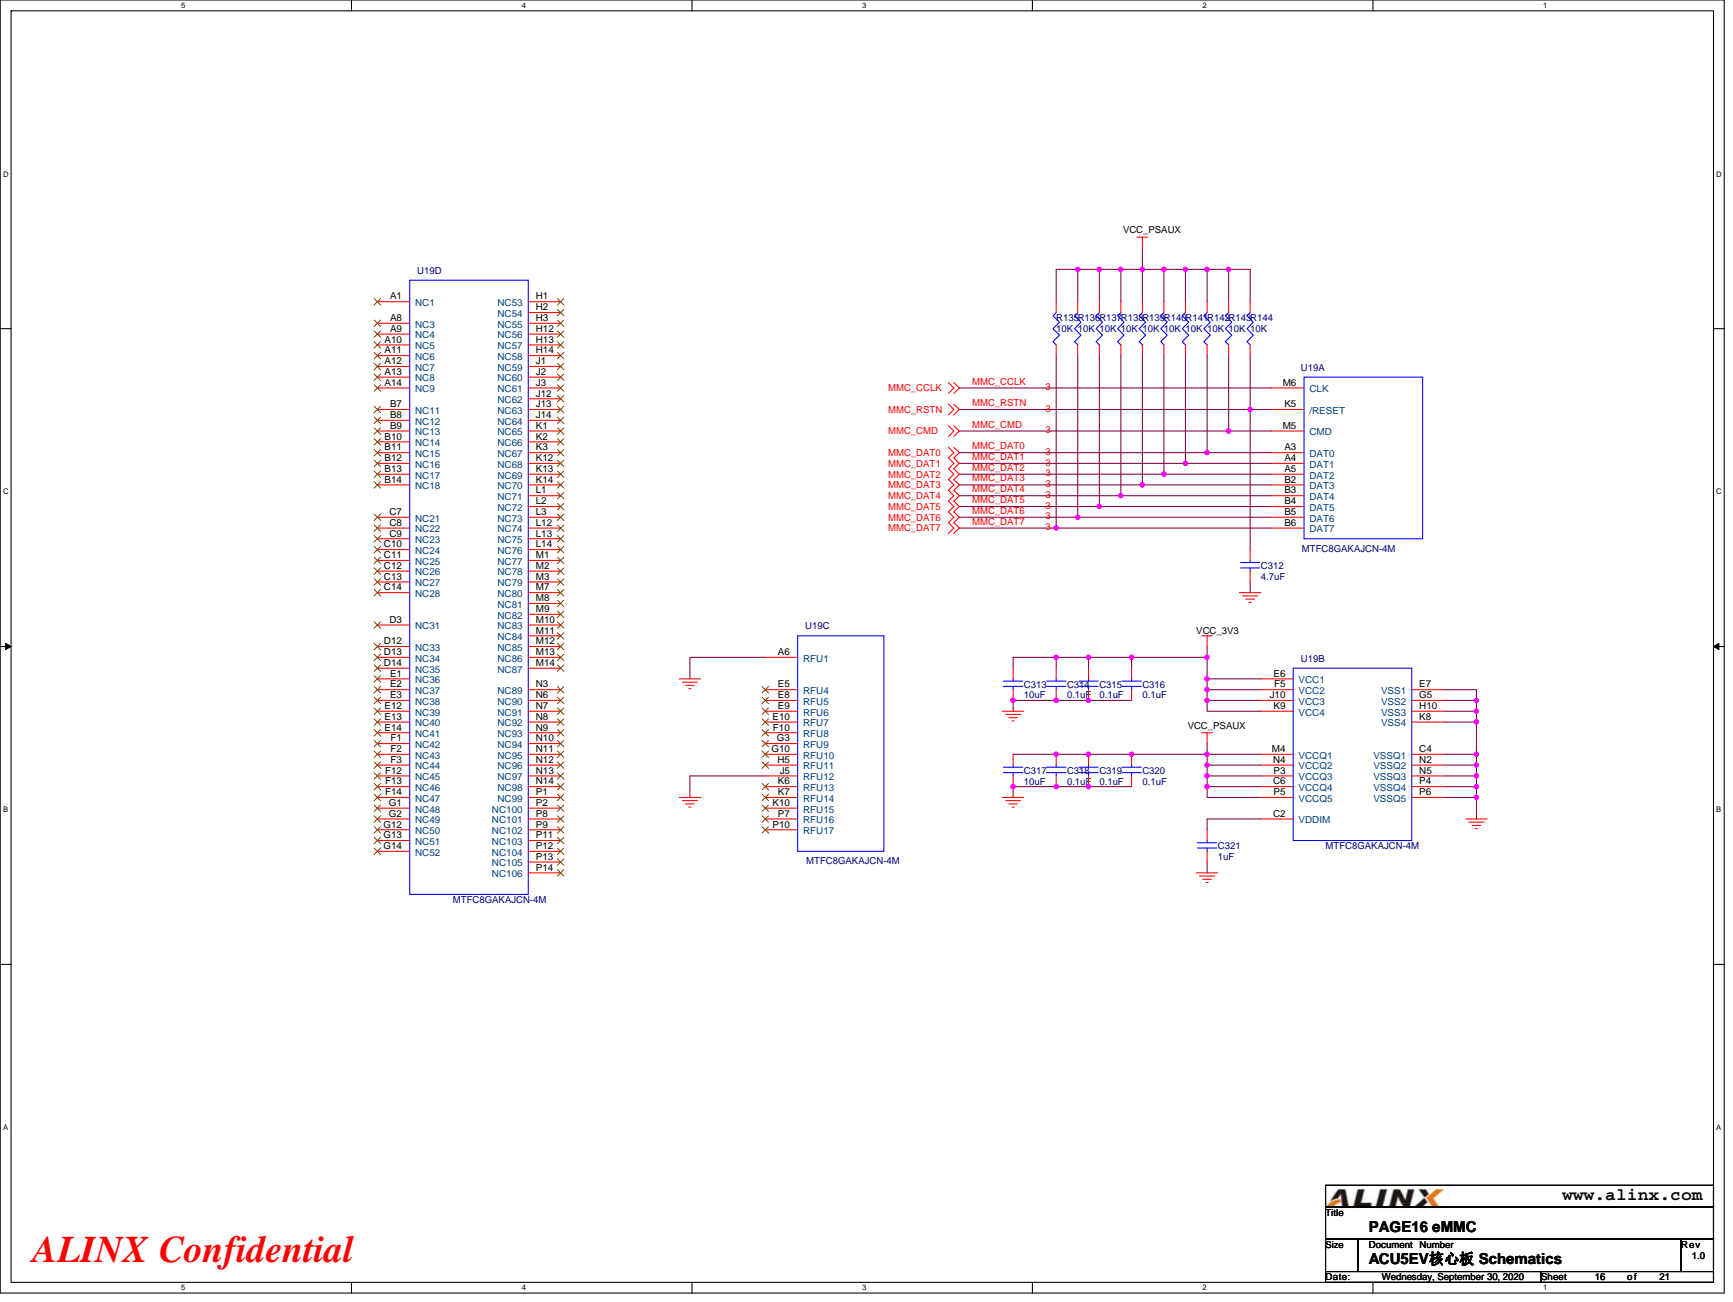
[picture p31: page 16]

# 200MHz

# PL SYSTEM CLOCK

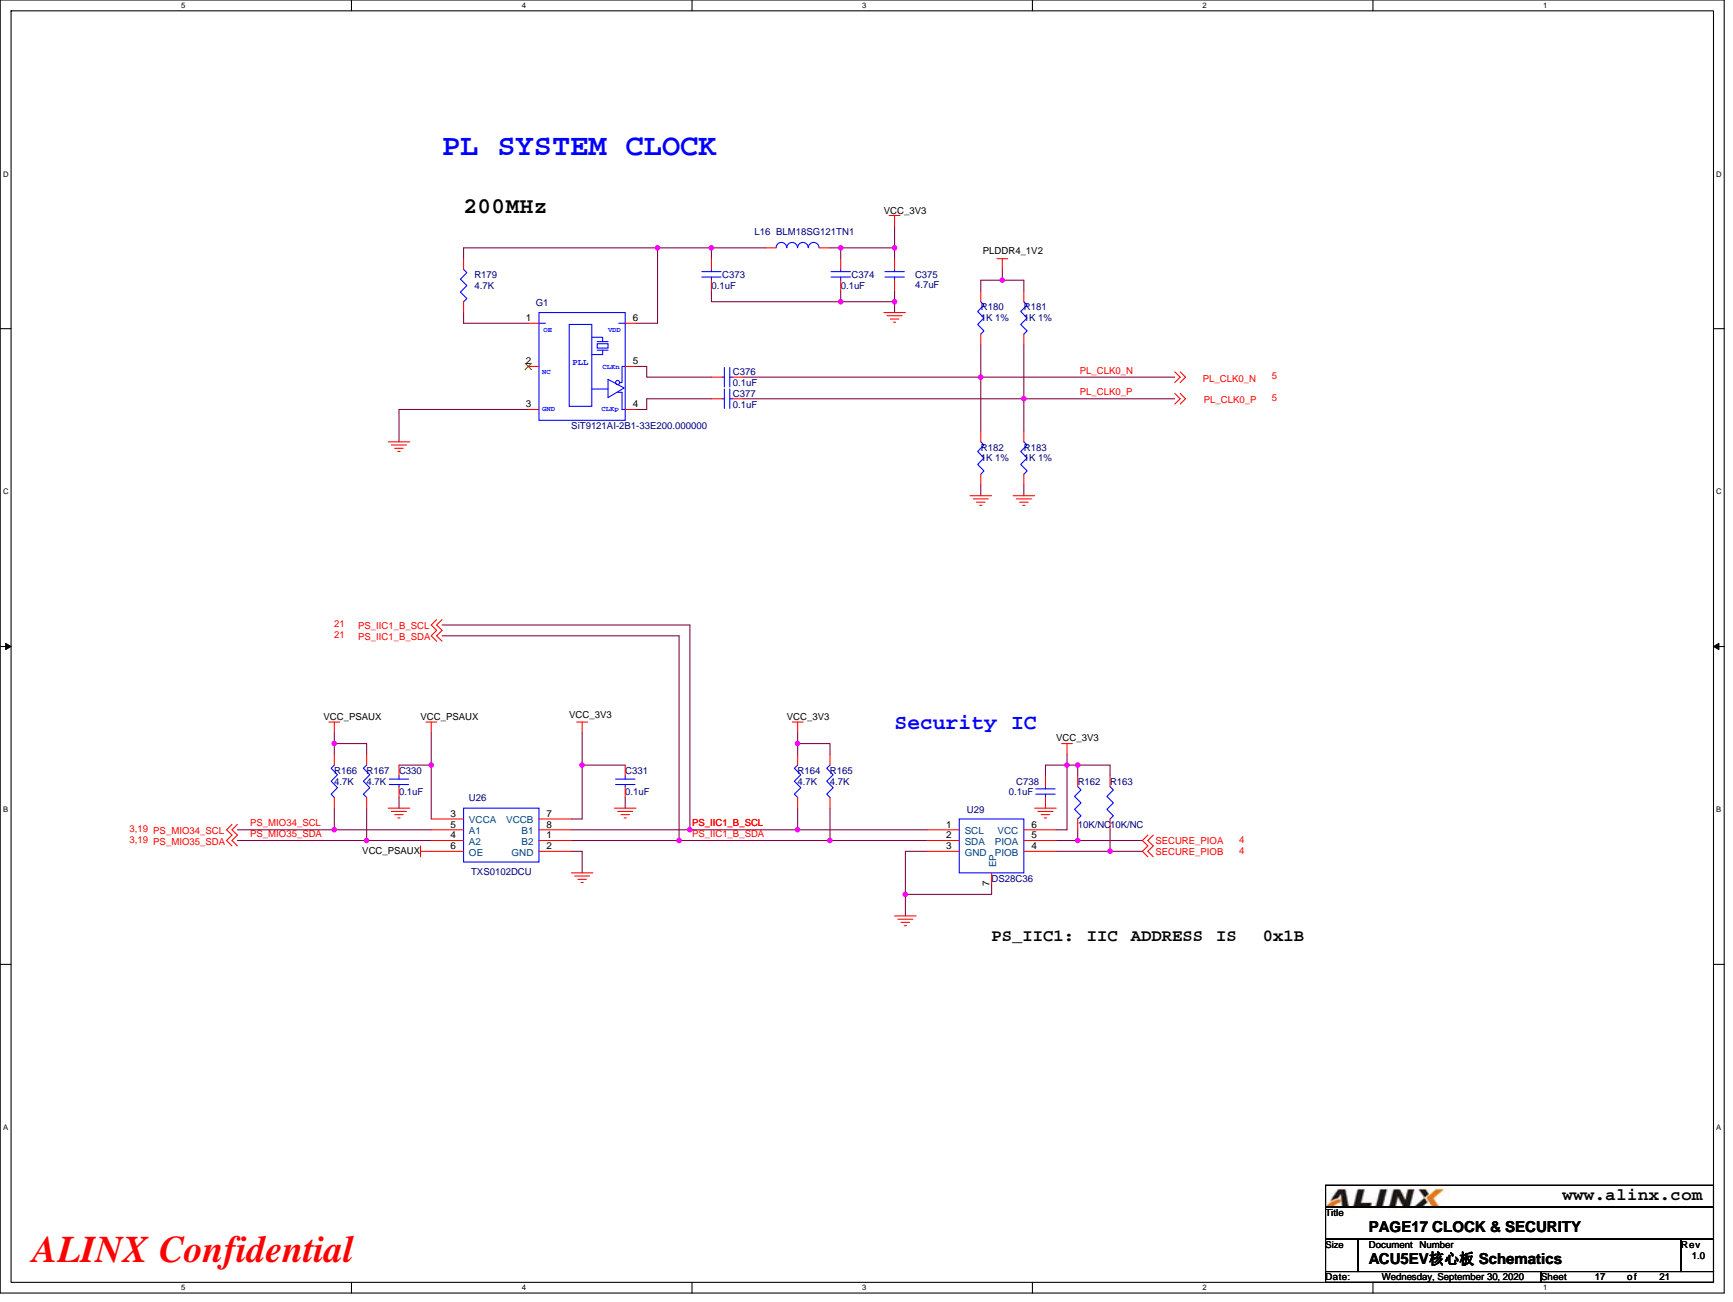
[picture p32: page 17]

BANK65, BANK66 IO Voltage can not exceed +1.8V | BANK45, BANK46 IO Voltage is +3.3V Standard

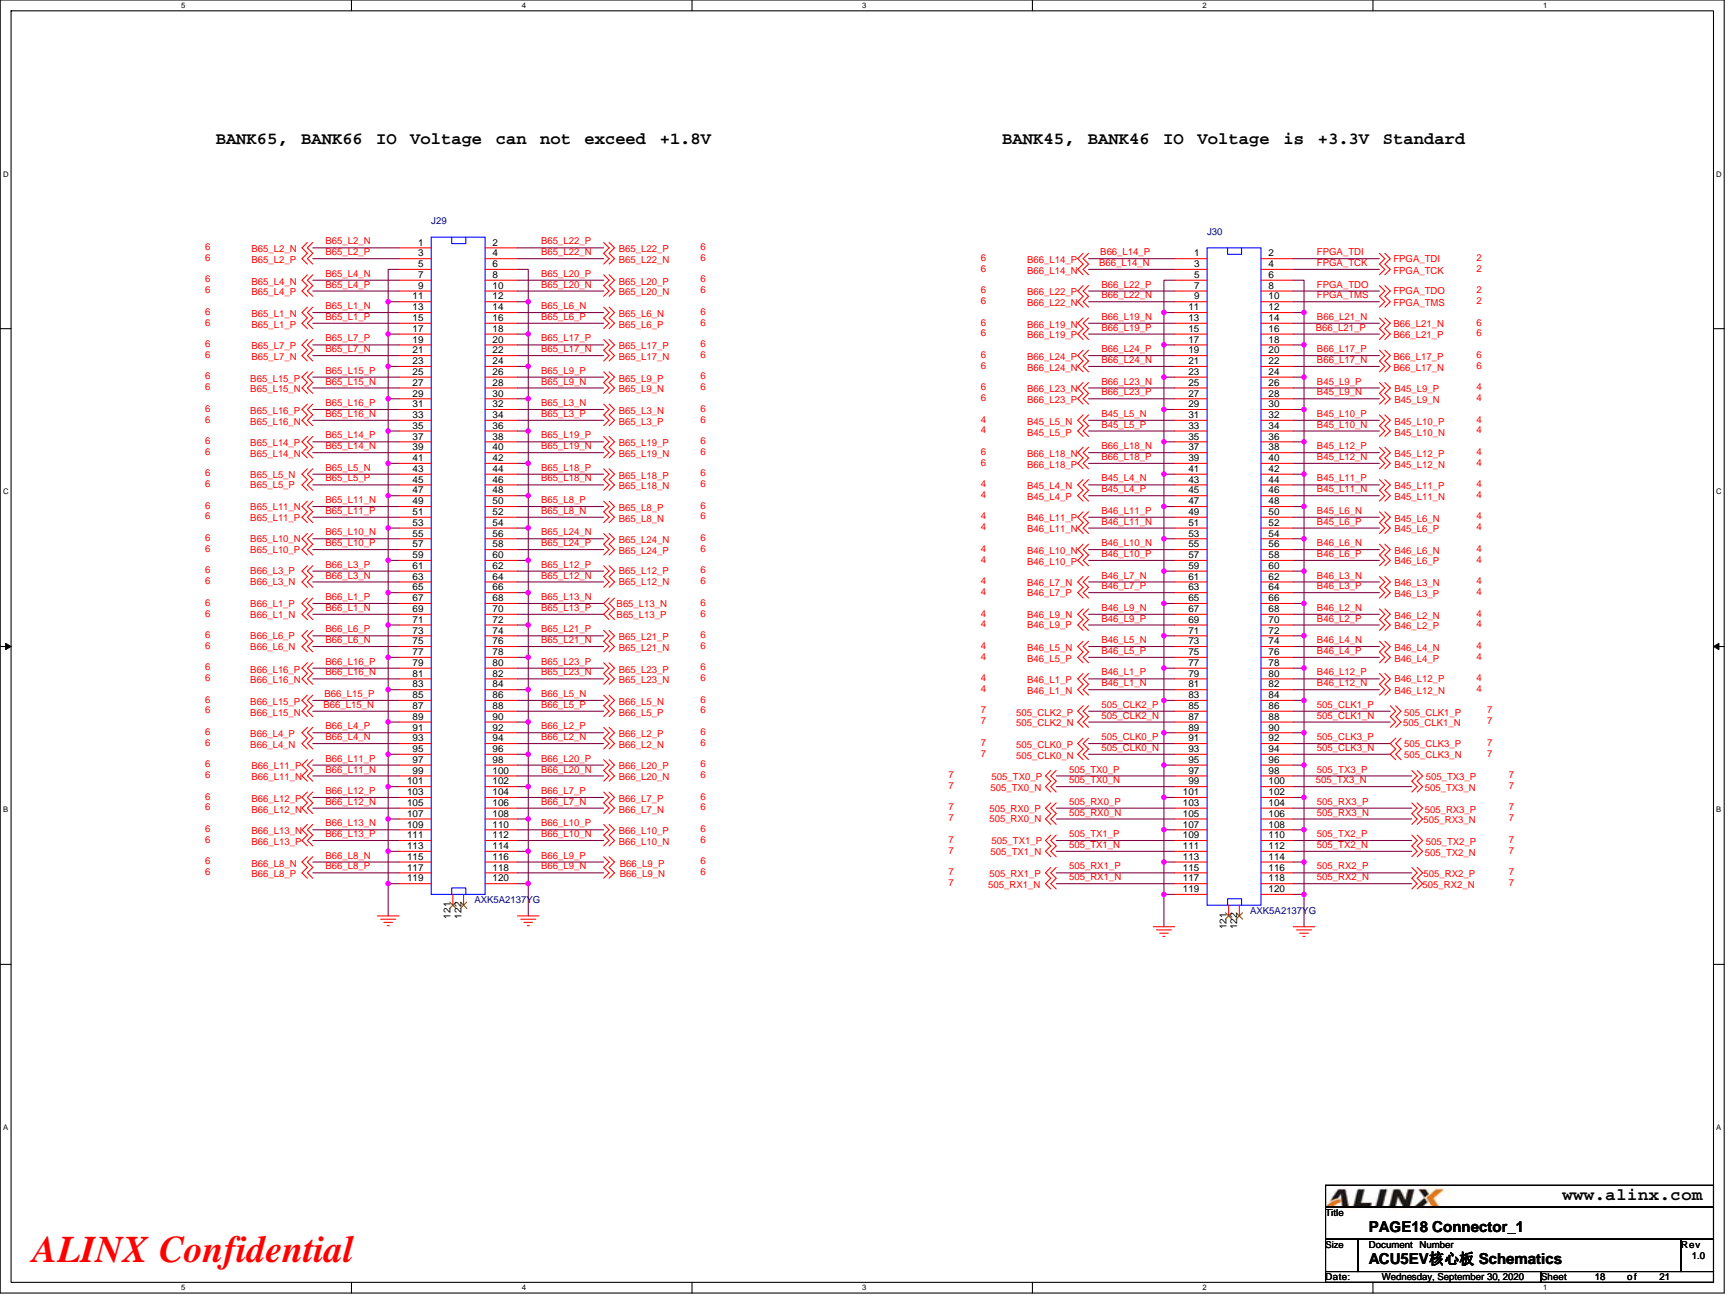
[picture p33: page 18]
FPGA_TMS; FPGA_TCK; FPGA_TDO; FPGA_TDI; 505_CLK0_N; 505_CLK0_P; 505_CLK3_P; 505_CLK3_N; 505_CLK2_P 505_CLK2_N; 505_CLK1_P 505_CLK1_N; 505_CLK1_P; 505_CLK1_N; 505_CLK2_P; 505_CLK2_N; PAGE18 Connector_1; Wednesday, September 30, 2020; AXK5A2137YG

www.alinx.com

BANK43, BANK44 IO Voltage is +3.3V Standard | The MIO Voltage is +1.8V Standard

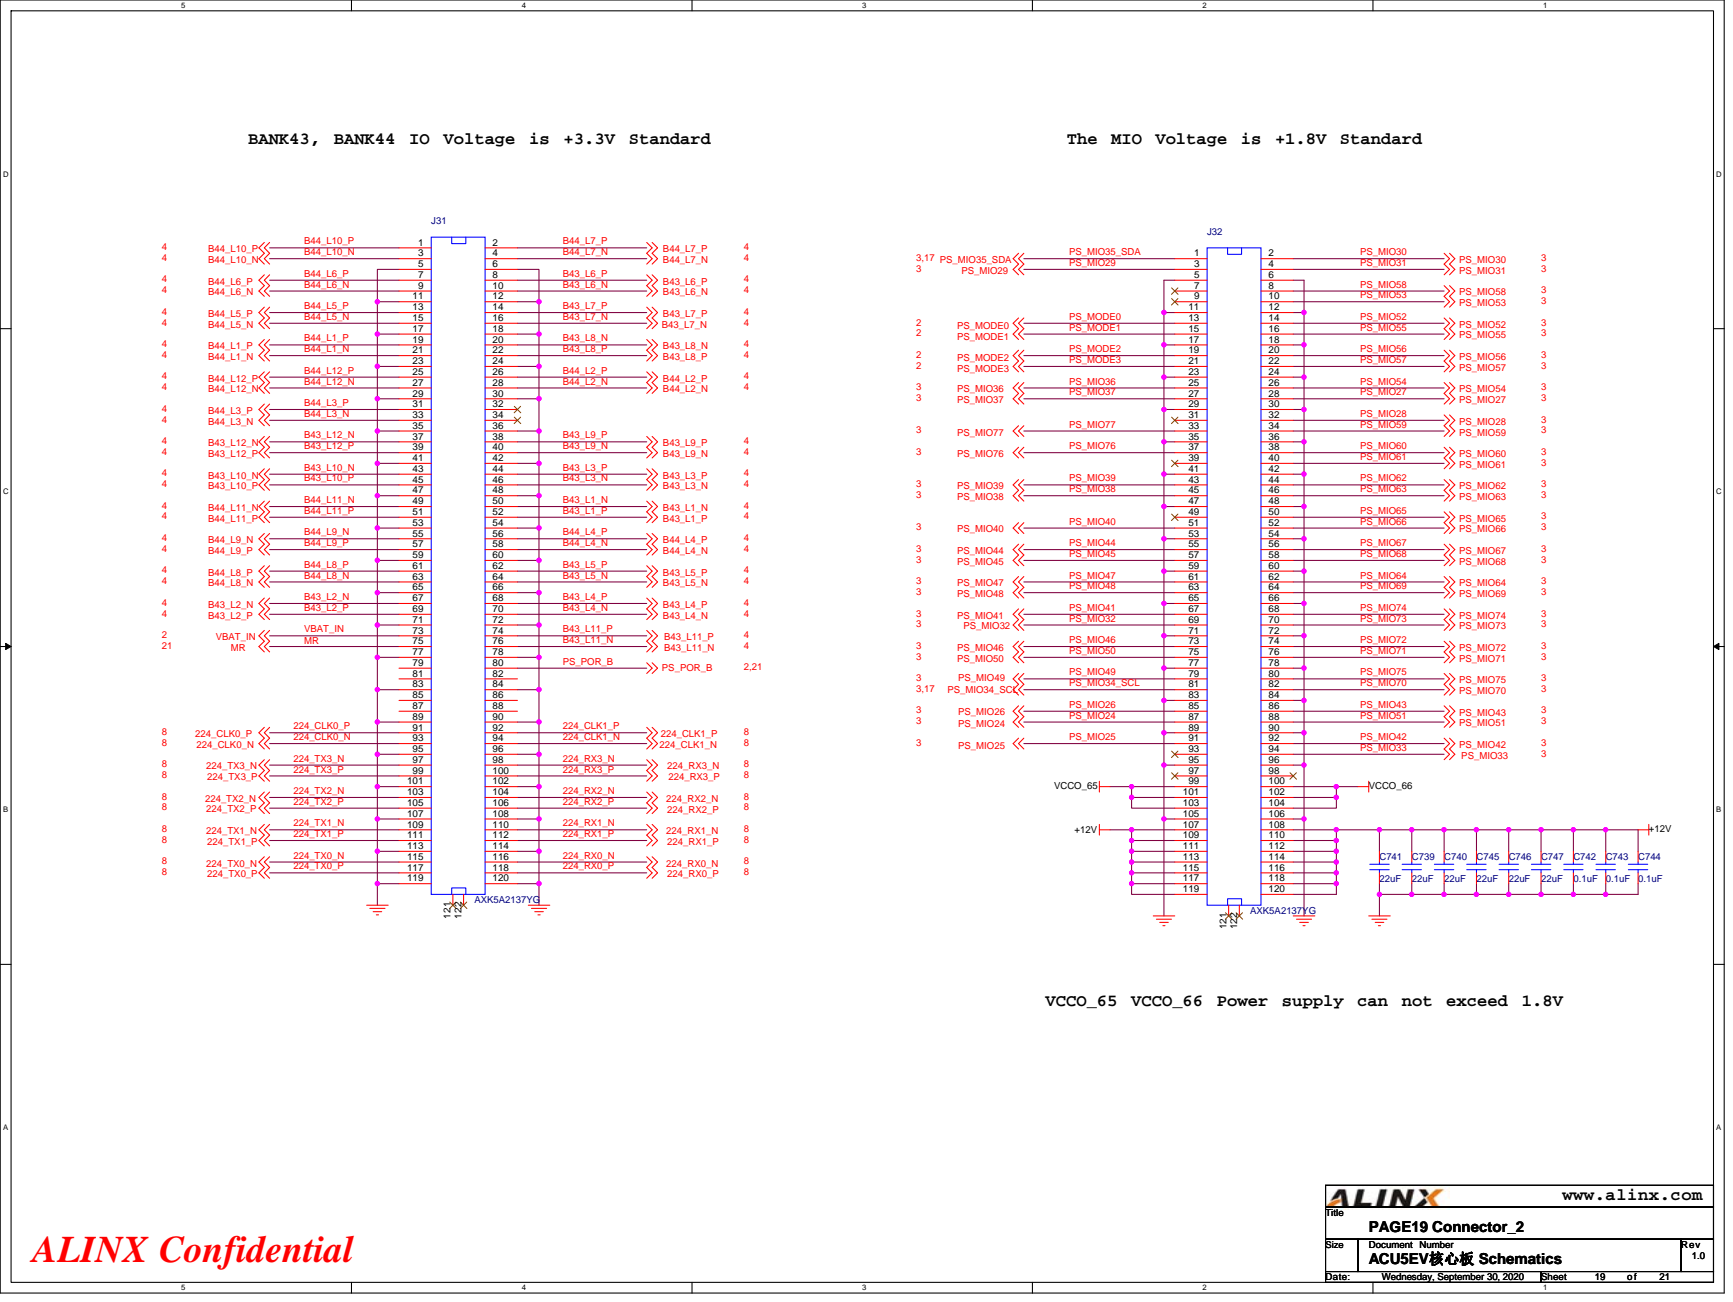
[picture p34: page 19]

109 | 110
111 | 112

118
120

VCCO_65 VCCO_66 Power supply can not exceed 1.8V

POWER ON: VCCINT/VCCINT_IO/VCCBRAM(+0.85V)->VCCINT_VCU(+0.9V)->VCCAUX/VCCAUX_IO(+1.8V)->VCCO(+3.3V, +1.8V)

# POWER ON: VCCINT(+0.85V)->MGTAVCC(+09V)->MGTAVTT(+1.2V)

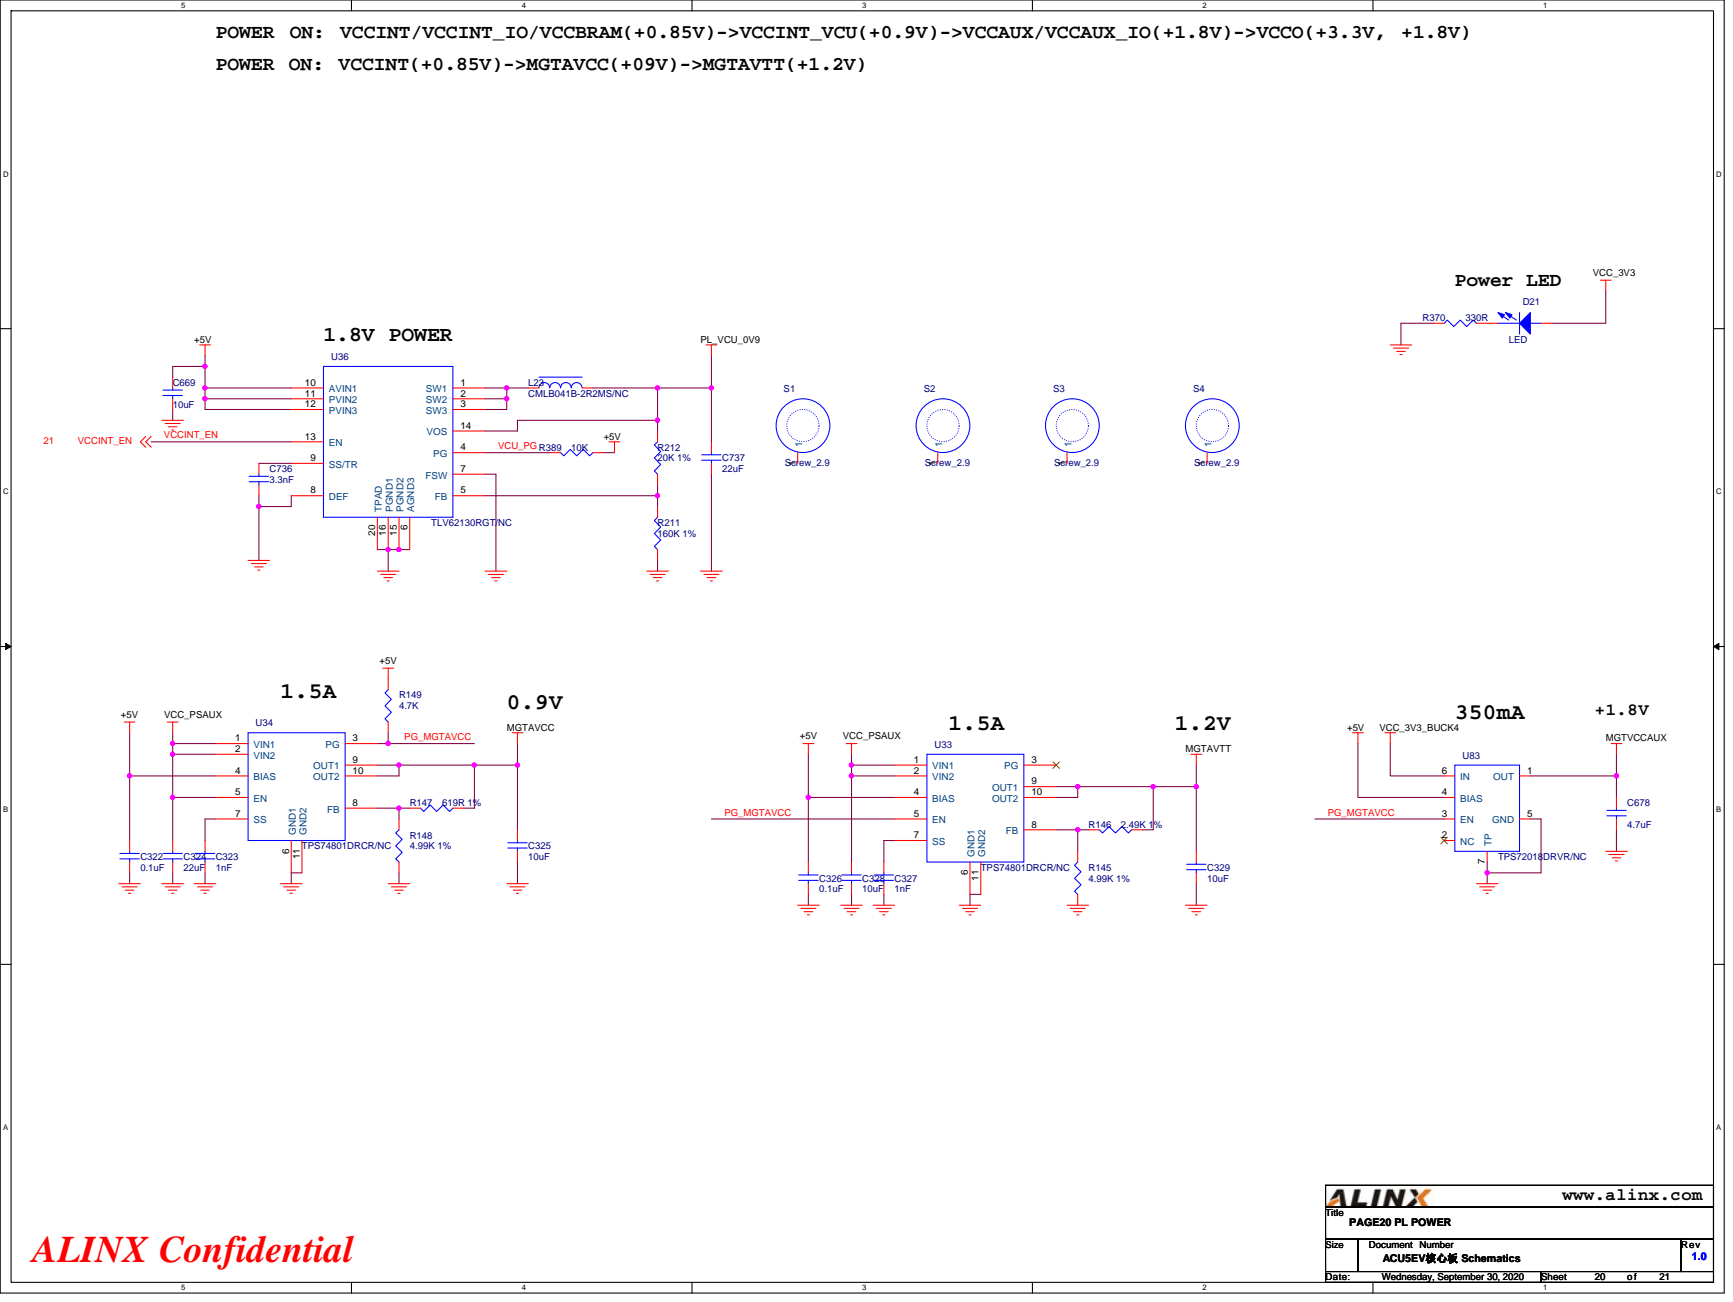
[picture p35: page 20]

# GPO1-----BUCK1_2_PG GPO4-----BUCK4_PG

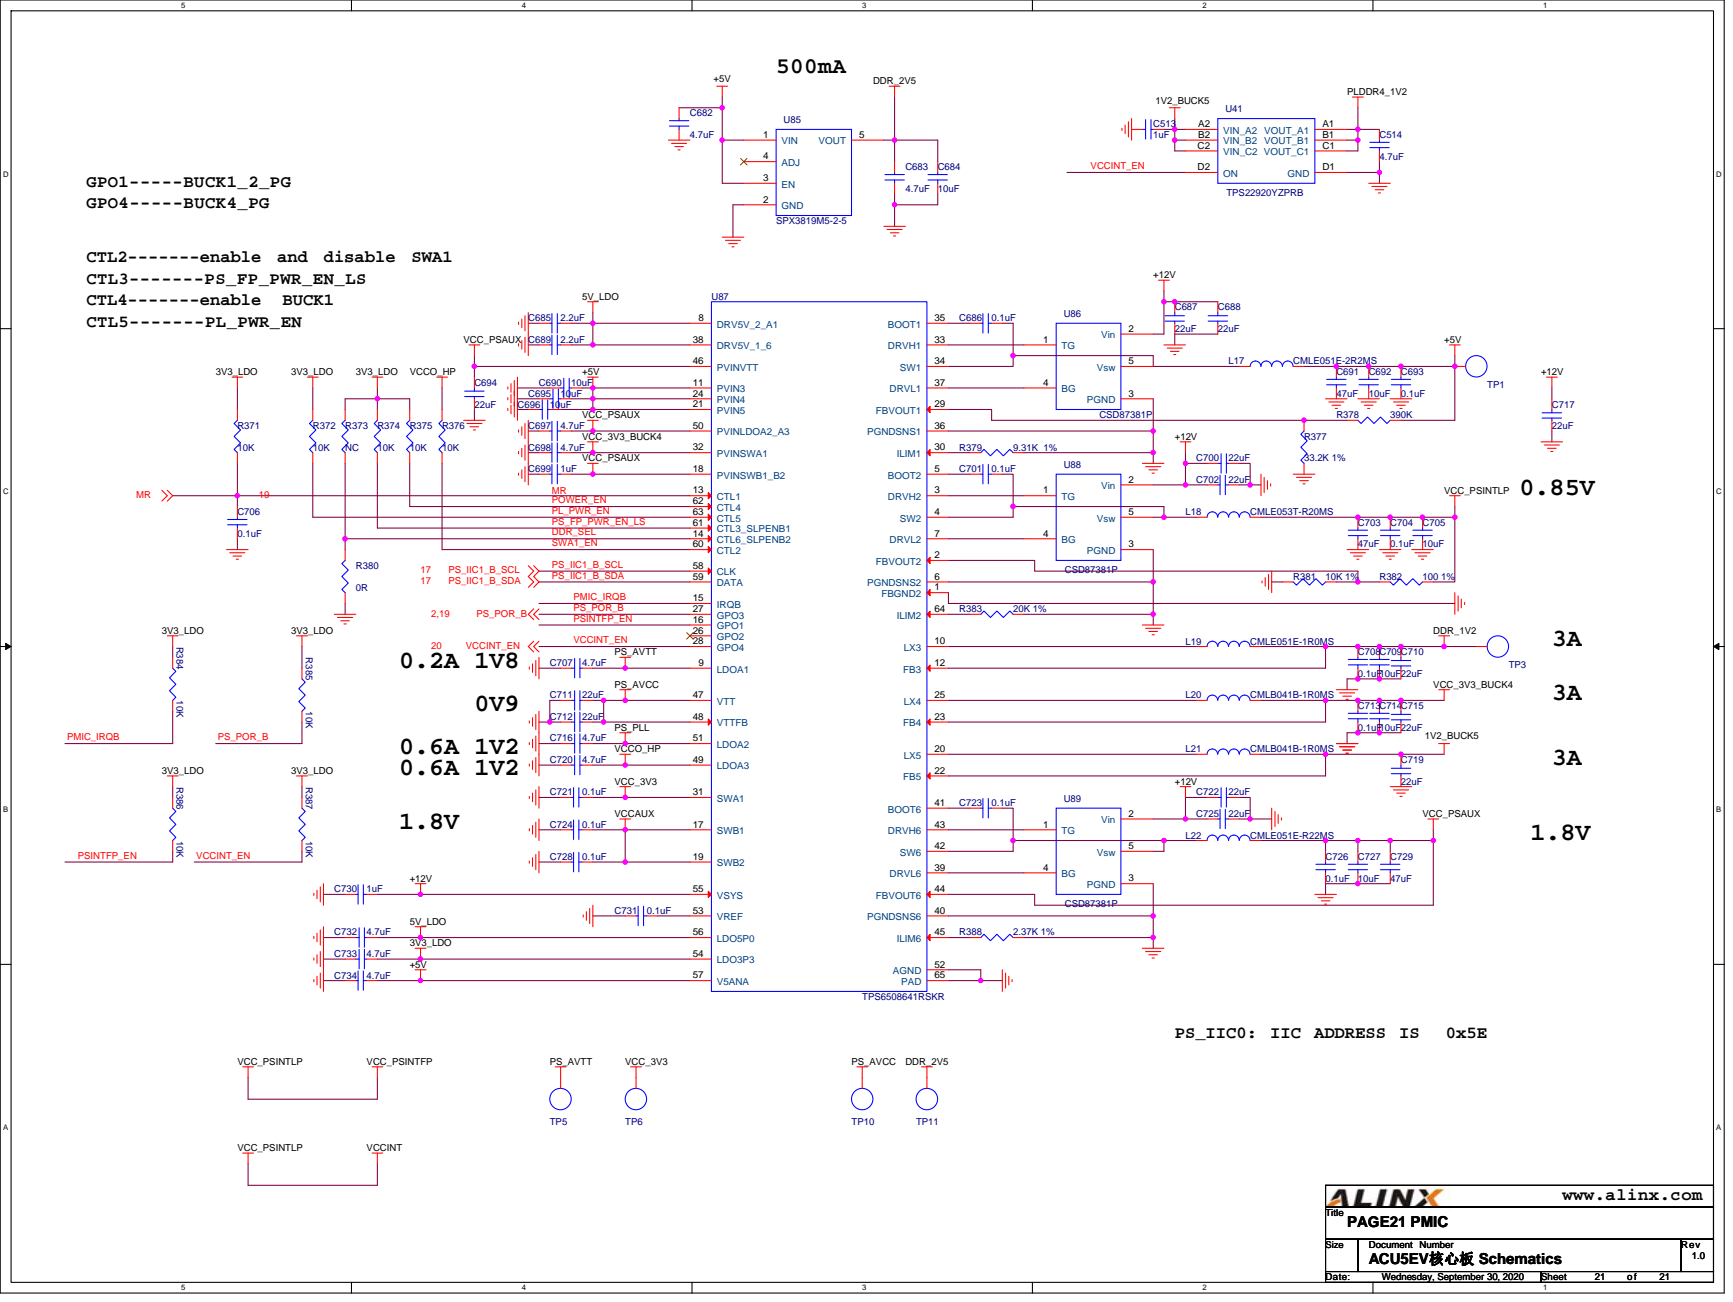
[picture p36: page 21]

PS_AVTT | | LDOA1 9

PS_AVCC | VTT 47 | | 0.1uF | 10uF

VREF 53

3V3_LDO | | LDO3P3 54

LDO5P0 56 | R388 2.37K 1%
