raonslab2/fcBoardKicad/connector.kicad_sch

## KiCad design connector.kicad_sch (2025-12-12)

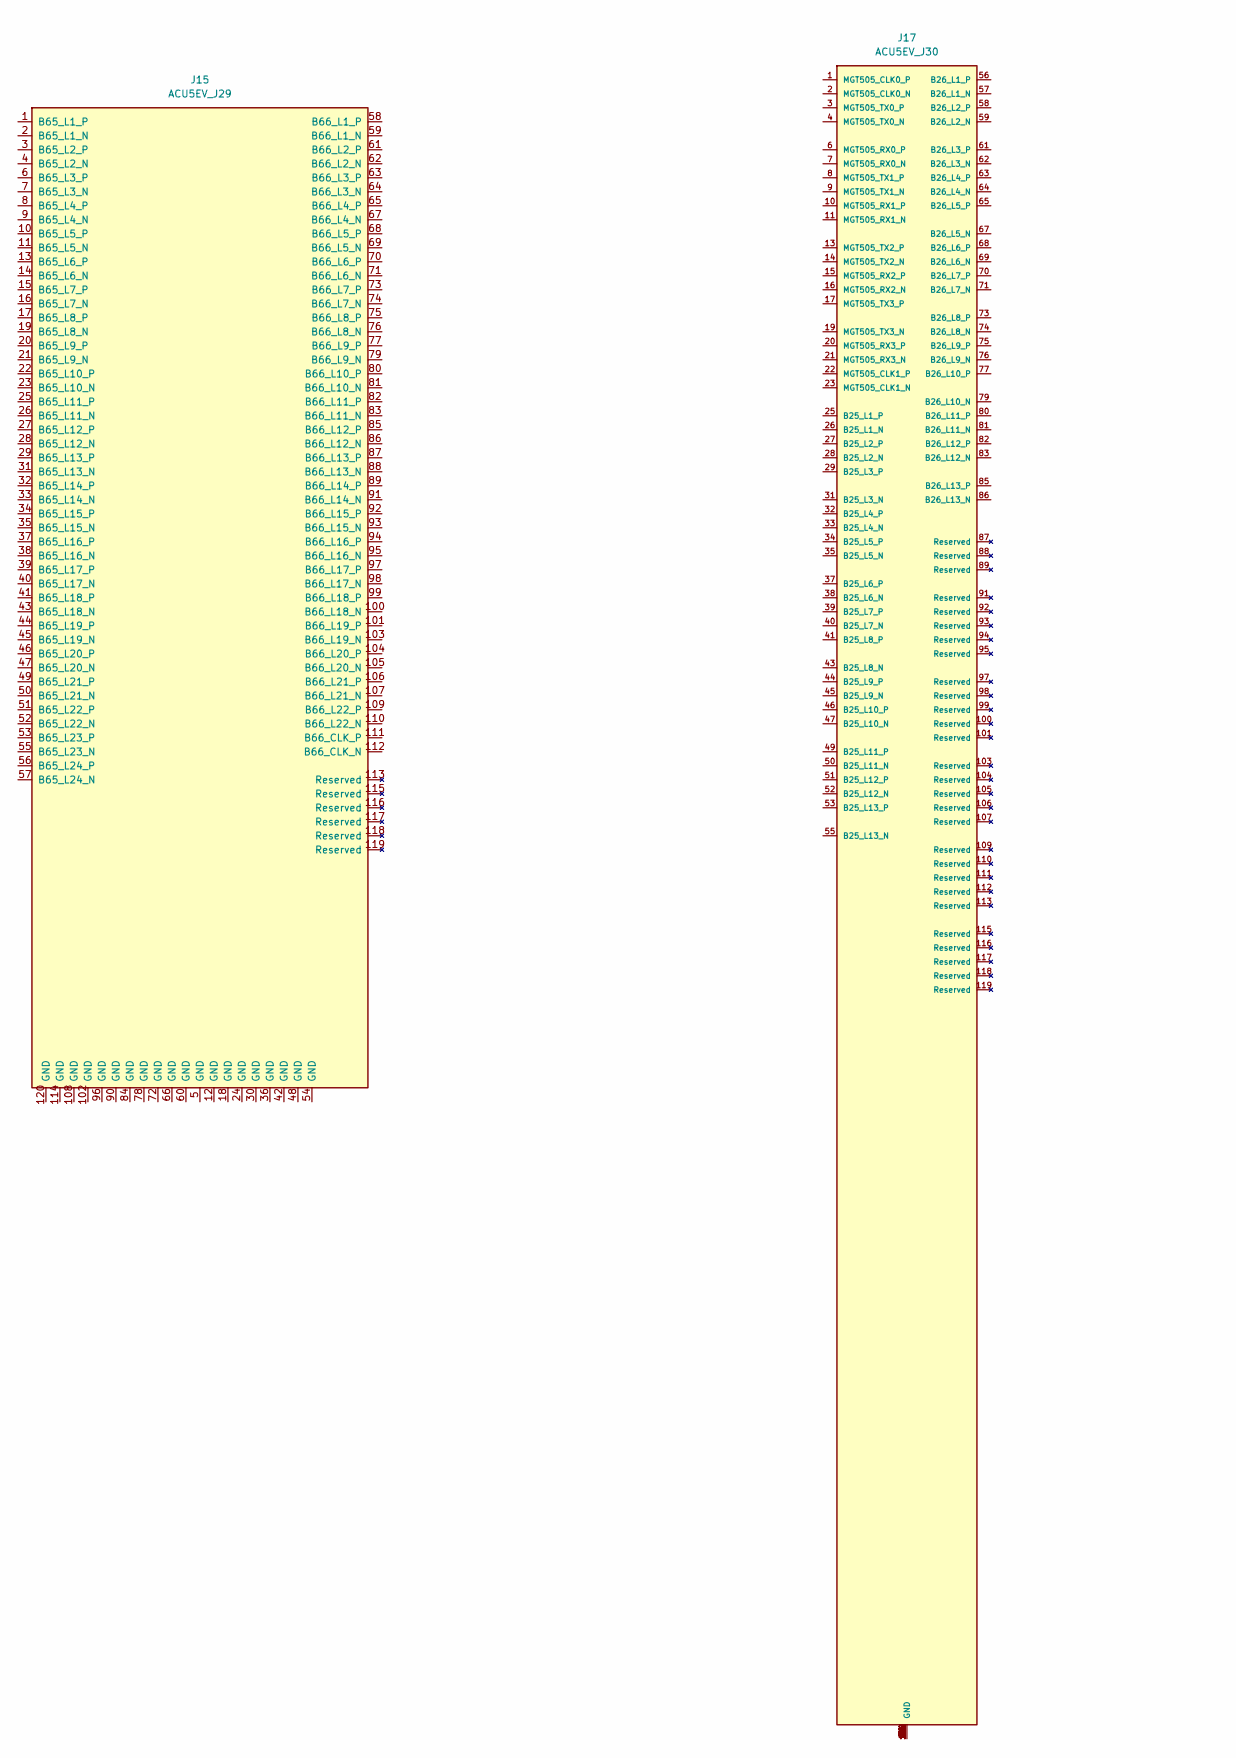
[picture p37: schematic connector.kicad_sch, part in row 1, column 1]

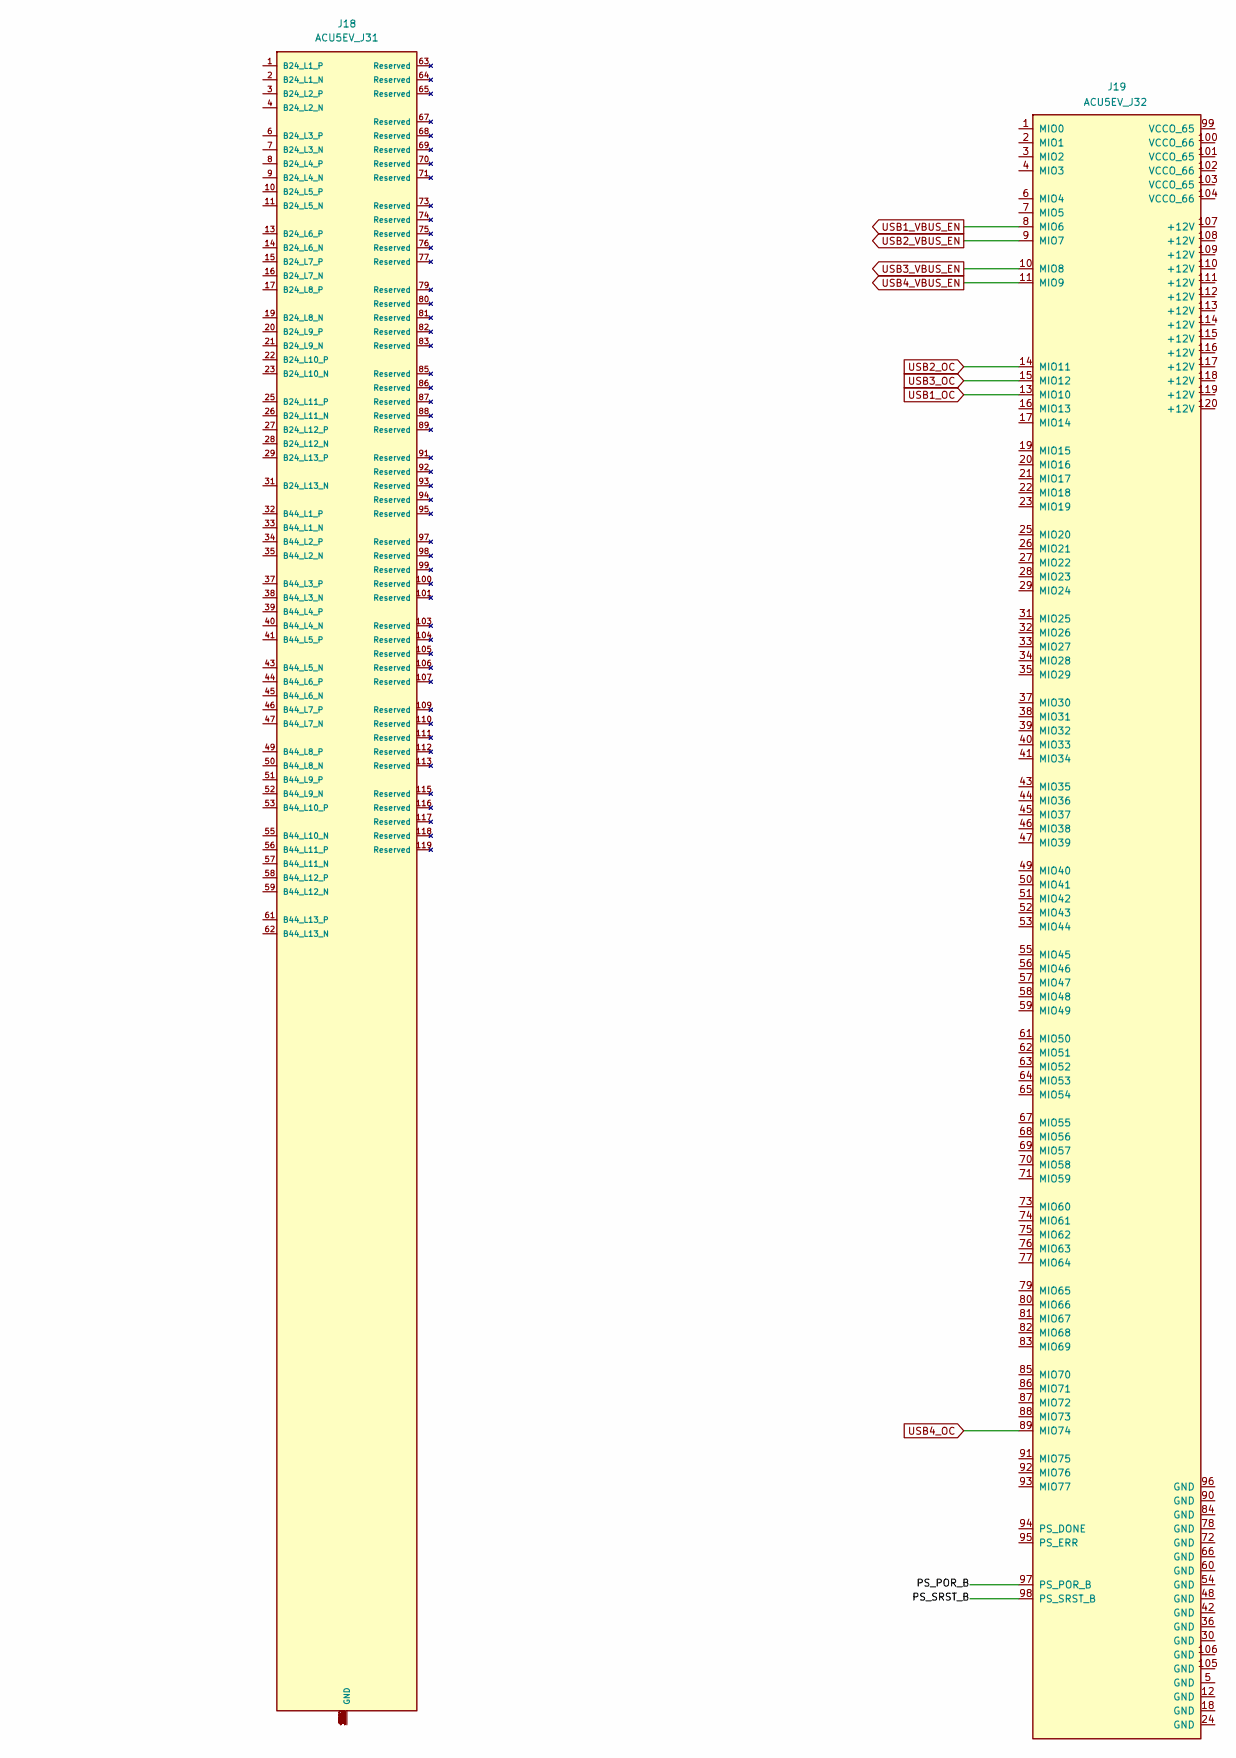
[picture p38: schematic connector.kicad_sch, part in row 1, column 2]

Parts:
J15: ACU5EV_J29; Panasonic_AXK6A2337YG
J17: ACU5EV_J30; Panasonic_AXK6A2337YG
J18: ACU5EV_J31; Panasonic_AXK6A2337YG
J19: ACU5EV_J32; Panasonic_AXK6A2337YG

Connections:
unnamed: J17.5 (GND), J17.12 (GND), J17.18 (GND), J17.24 (GND), J17.30 (GND), J17.36 (GND), J17.42 (GND), J17.48 (GND), J17.54 (GND), J17.60 (GND), J17.66 (GND), J17.72 (GND), J17.78 (GND), J17.84 (GND), J17.90 (GND), J17.96 (GND), J17.102 (GND), J17.108 (GND), J17.114 (GND), J17.120 (GND)
unnamed: J18.5 (GND), J18.12 (GND), J18.18 (GND), J18.24 (GND), J18.30 (GND), J18.36 (GND), J18.42 (GND), J18.48 (GND), J18.54 (GND), J18.60 (GND), J18.66 (GND), J18.72 (GND), J18.78 (GND), J18.84 (GND), J18.90 (GND), J18.96 (GND), J18.102 (GND), J18.108 (GND), J18.114 (GND), J18.120 (GND)
PS_POR_B: J19.97 (PS_POR_B)
PS_SRST_B: J19.98 (PS_SRST_B)
USB1_OC: J19.13 (MIO10)
USB1_VBUS_EN: J19.8 (MIO6)
USB2_OC: J19.14 (MIO11)
USB2_VBUS_EN: J19.9 (MIO7)
USB3_OC: J19.15 (MIO12)
USB3_VBUS_EN: J19.10 (MIO8)
USB4_OC: J19.89 (MIO74)
USB4_VBUS_EN: J19.11 (MIO9)
