raonslab2/fcBoardKicad/fcBoard_Ethernet.kicad_sch

## KiCad design fcBoard_Ethernet.kicad_sch (2025-12-14)

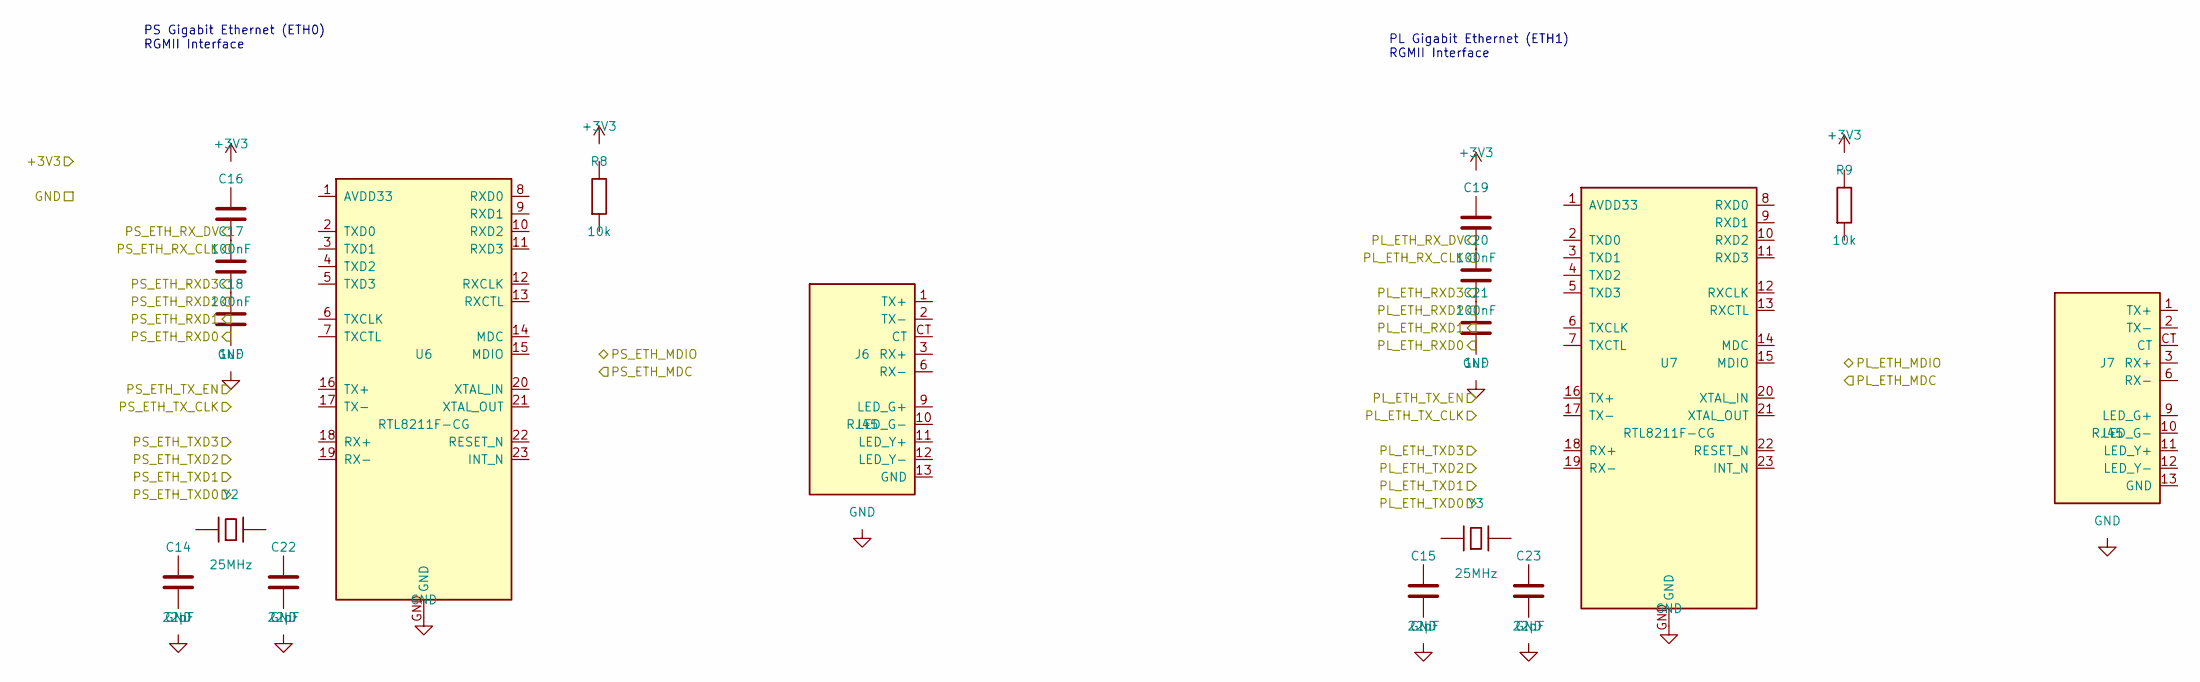
[picture p39: schematic fcBoard_Ethernet.kicad_sch]

Parts:
C14, C15, C22, C23: 22pF; C0402; LCSC Part C1555
C16, C17, C19, C20: 100nF; C0402; LCSC Part C11702
C18, C21: 1uF; C0603; LCSC Part C15849
J6, J7: RJ45; RJ45-TH_8P8C_L21.0-W16.0-H13.0; LCSC Part C138388
R8, R9: 10k; R0402; LCSC Part C25804
U6, U7: RTL8211F-CG; QFN-48-1EP_7x7mm_P0.5mm_EP5.3x5.3mm; LCSC Part C69264
Y2, Y3: 25MHz; HC-49S_L11.0-W4.6; LCSC Part C9010

Connections:
GND: U6.GND, U7.GND
unnamed: C16.2, C17.1
unnamed: C17.2, C18.1
unnamed: C19.2, C20.1
unnamed: C20.2, C21.1

Notes on the sheet:
PS Gigabit Ethernet (ETH0) RGMII Interface
PL Gigabit Ethernet (ETH1) RGMII Interface
