raonslab2/fcBoardKicad/fcBoard_GPIO.kicad_sch

## KiCad design fcBoard_GPIO.kicad_sch (2025-12-12)

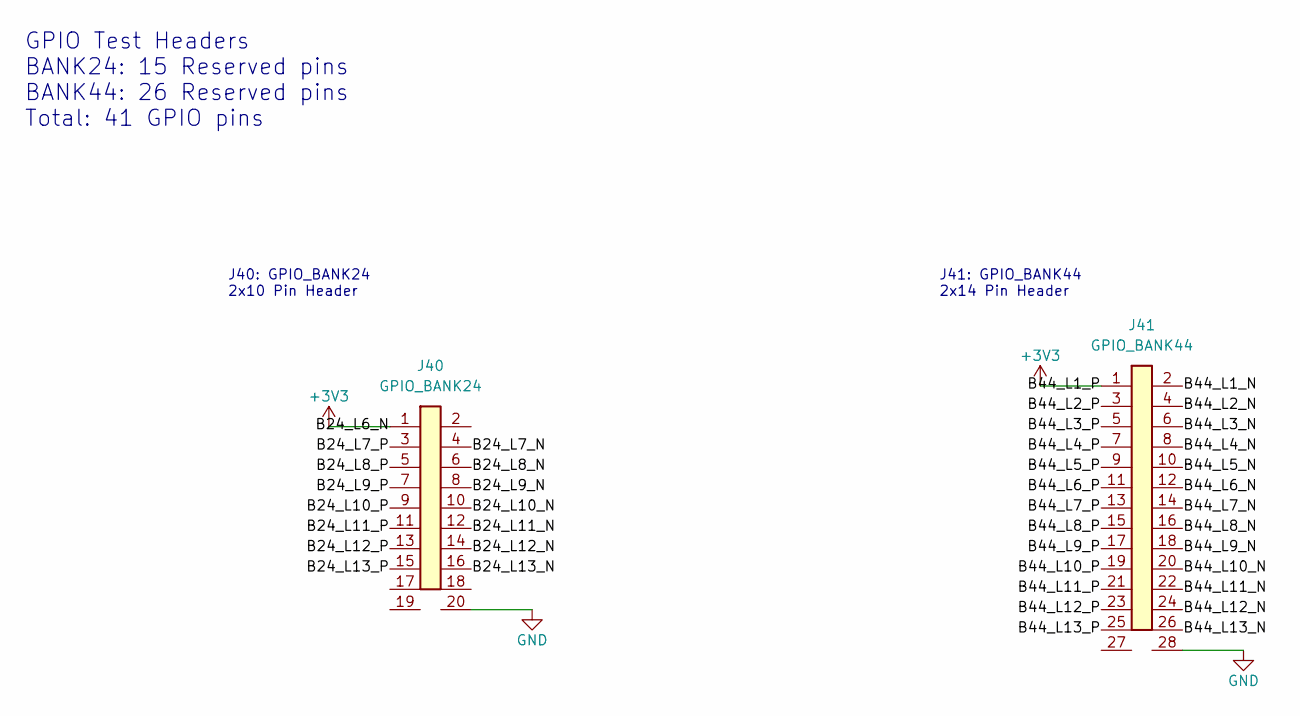
[picture p40: schematic fcBoard_GPIO.kicad_sch]

Parts:
J40: GPIO_BANK24; PinHeader_2x10_P2.54mm_Vertical
J41: GPIO_BANK44; PinHeader_2x14_P2.54mm_Vertical

Connections:
+3V3: J40.1, J41.1
B24_L7_N: J40.4
B24_L7_P: J40.3
B24_L8_N: J40.6
B24_L8_P: J40.5
B24_L9_N: J40.8
B24_L9_P: J40.7
B24_L10_N: J40.10
B24_L10_P: J40.9
B24_L11_N: J40.12
B24_L11_P: J40.11
B24_L12_N: J40.14
B24_L12_P: J40.13
B24_L13_N: J40.16
B24_L13_P: J40.15
B44_L1_N: J41.2
B44_L2_N: J41.4
B44_L2_P: J41.3
B44_L3_N: J41.6
B44_L3_P: J41.5
B44_L4_N: J41.8
B44_L4_P: J41.7
B44_L5_N: J41.10
B44_L5_P: J41.9
B44_L6_N: J41.12
B44_L6_P: J41.11
B44_L7_N: J41.14
B44_L7_P: J41.13
B44_L8_N: J41.16
B44_L8_P: J41.15
B44_L9_N: J41.18
B44_L9_P: J41.17
B44_L10_N: J41.20
B44_L10_P: J41.19
B44_L11_N: J41.22
B44_L11_P: J41.21
B44_L12_N: J41.24
B44_L12_P: J41.23
B44_L13_N: J41.26
B44_L13_P: J41.25
GND: J40.20, J41.28

Notes on the sheet:
GPIO Test Headers BANK24: 15 Reserved pins BANK44: 26 Reserved pins Total: 41 GPIO pins
J40: GPIO_BANK24 2x10 Pin Header
J41: GPIO_BANK44 2x14 Pin Header
