raonslab2/fcBoardKicad/fcBoard_HDMI.kicad_sch

## KiCad design fcBoard_HDMI.kicad_sch (2025-12-11)

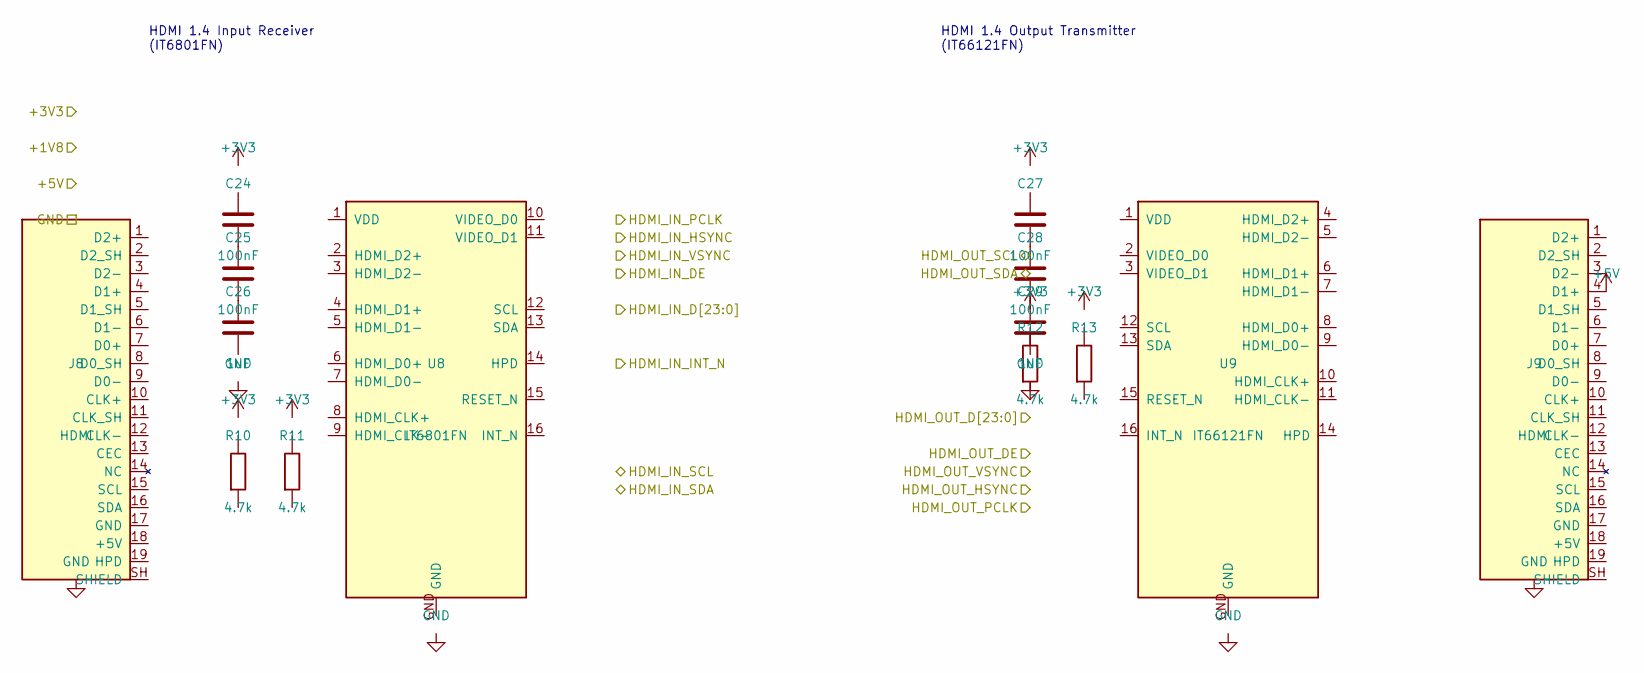
[picture p41: schematic fcBoard_HDMI.kicad_sch]

Parts:
C24, C25, C27, C28: 100nF; C0402; LCSC Part C11702
C26, C29: 1uF; C0603; LCSC Part C15849
J8, J9: HDMI; HDMI-SMD_HDMI-001S; LCSC Part C138380
R10, R11, R12, R13: 4.7k; R0402; LCSC Part C25900
U8: IT6801FN; LQFP-100_14x14mm_P0.5mm; LCSC Part C2651318
U9: IT66121FN; LQFP-100_14x14mm_P0.5mm; LCSC Part C2652461

Connections:
+5V: J9.4 (D1+)
unnamed: C24.2, C25.1
unnamed: C25.2, C26.1
unnamed: C27.2, C28.1
unnamed: C28.2, C29.1

Notes on the sheet:
HDMI 1.4 Output Transmitter (IT66121FN)
HDMI 1.4 Input Receiver (IT6801FN)
