raonslab2/fcBoardKicad/fcBoard_Peripherals.kicad_sch

## KiCad design fcBoard_Peripherals.kicad_sch (2025-12-11)

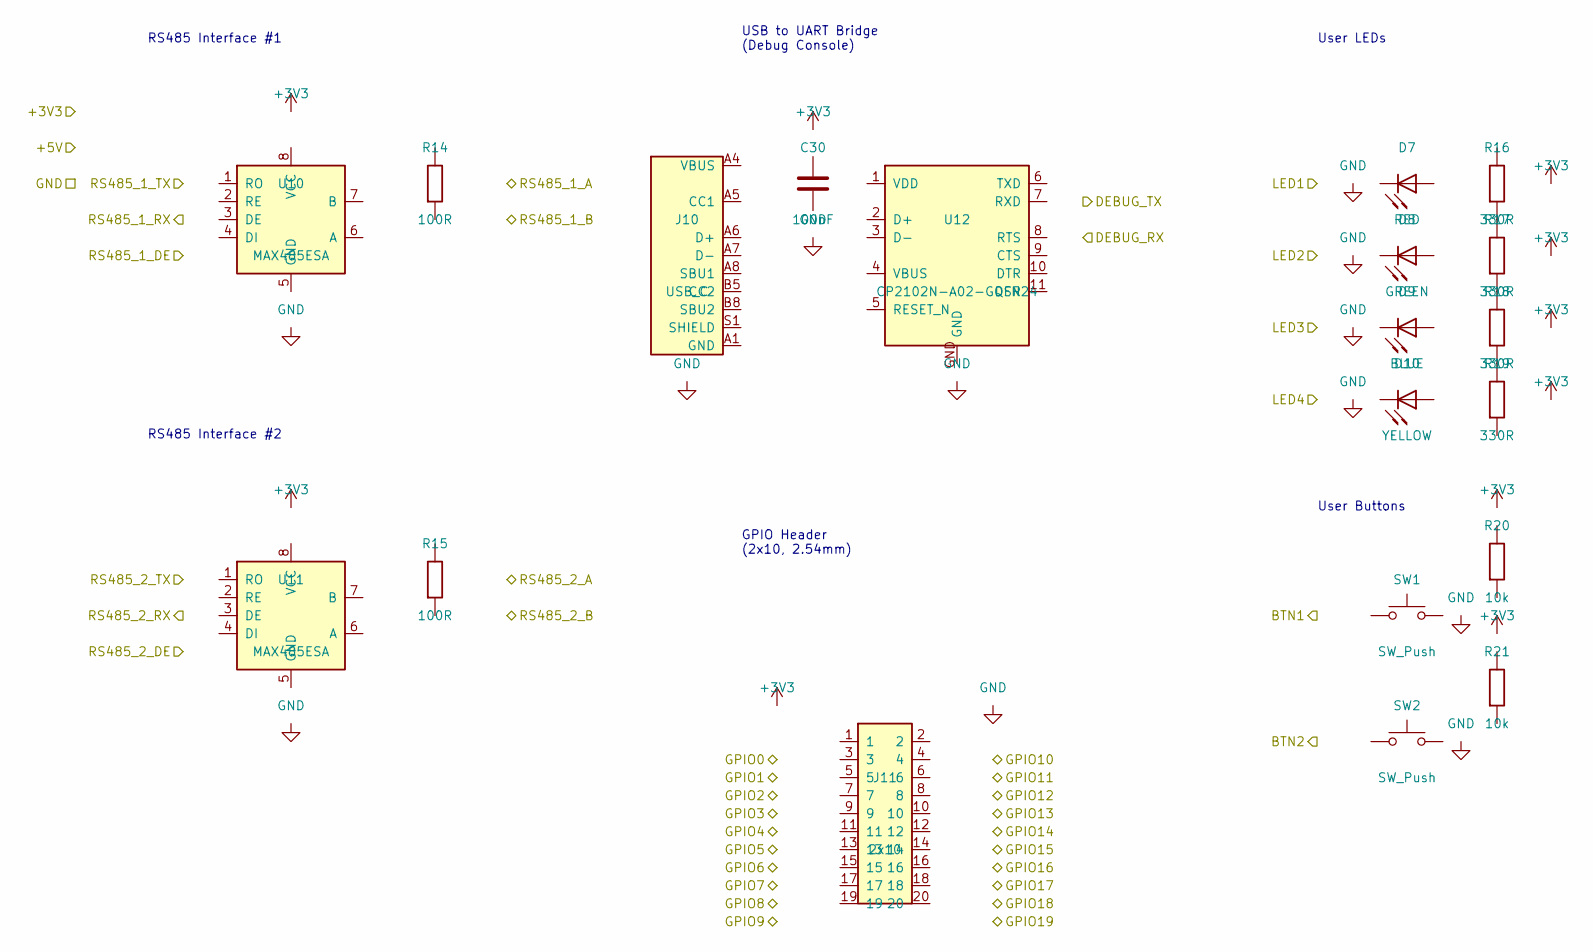
[picture p42: schematic fcBoard_Peripherals.kicad_sch]

Parts:
C30: 100nF; C0402; LCSC Part C11702
D7: RED; LED0603-RD; LCSC Part C2290
D8: GREEN; LED0603-RD; LCSC Part C2286
D9: BLUE; LED0603-RD; LCSC Part C72041
D10: YELLOW; LED0603-RD; LCSC Part C72038
J10: USB_C; USB-C-SMD_TYPE-C-31-M-12; LCSC Part C165948
J11: 2x10; HDR-TH_20P-P2.54-V-2X10; LCSC Part C124378
R14, R15: 100R; R0402; LCSC Part C25076
R16, R17, R18, R19: 330R; R0402; LCSC Part C72038
R20, R21: 10k; R0402; LCSC Part C25804
SW1, SW2: SW_Push; SW-SMD_L4.0-W4.0-P2.20; LCSC Part C115357
U10, U11: MAX485ESA; SOIC-8_3.9x4.9mm_P1.27mm; LCSC Part C9106
U12: CP2102N-A02-GQFN24; QFN-28-1EP_5x5mm_P0.5mm_EP3.35x3.35mm; LCSC Part C105018

Connections:
unnamed: R16.2, R17.1
unnamed: R17.2, R18.1
unnamed: R18.2, R19.1

Notes on the sheet:
USB to UART Bridge (Debug Console)
RS485 Interface #2
User Buttons
User LEDs
GPIO Header (2x10, 2.54mm)
RS485 Interface #1
