raonslab2/fcBoardKicad/fcBoard_Power2.kicad_sch

## KiCad design fcBoard_Power2.kicad_sch (2025-12-12)

Schematic: fcBoard_Power2.kicad_sch

Parts:
C1: 470uF; CP_Elec_10x10.5
C2, C4, C6: 100uF; C_1206_3216Metric
C3, C5, C7: 220uF; CP_Elec_8x10.5
D1, D3, D5: SS34; D_SMA
D2: GREEN; LED_0603_1608Metric
D4: YELLOW; LED_0603_1608Metric
D6: RED; LED_0603_1608Metric
J1: DC_12V; BarrelJack_Horizontal
L1, L2, L3: 33uH; L_12x12mm_H8mm
R1, R3, R6: 1k; R_0402_1005Metric
R2: 1.5k; R_0402_1005Metric
R4, R5: 470; R_0402_1005Metric
R7: 330; R_0402_1005Metric
U1: LM2596S-5.0; TO-263-5_TabPin3
U2, U3: LM2596S-ADJ; TO-263-5_TabPin3

Notes on the sheet:
12V DC Input Section
5V Output (LM2596S-5.0)
3.3V Output (LM2596S-ADJ)
1.8V Output (LM2596S-ADJ)
