raonslab2/fcBoardKicad/fcBoard_Power.kicad_sch

## KiCad design fcBoard_Power.kicad_sch (2025-12-11)

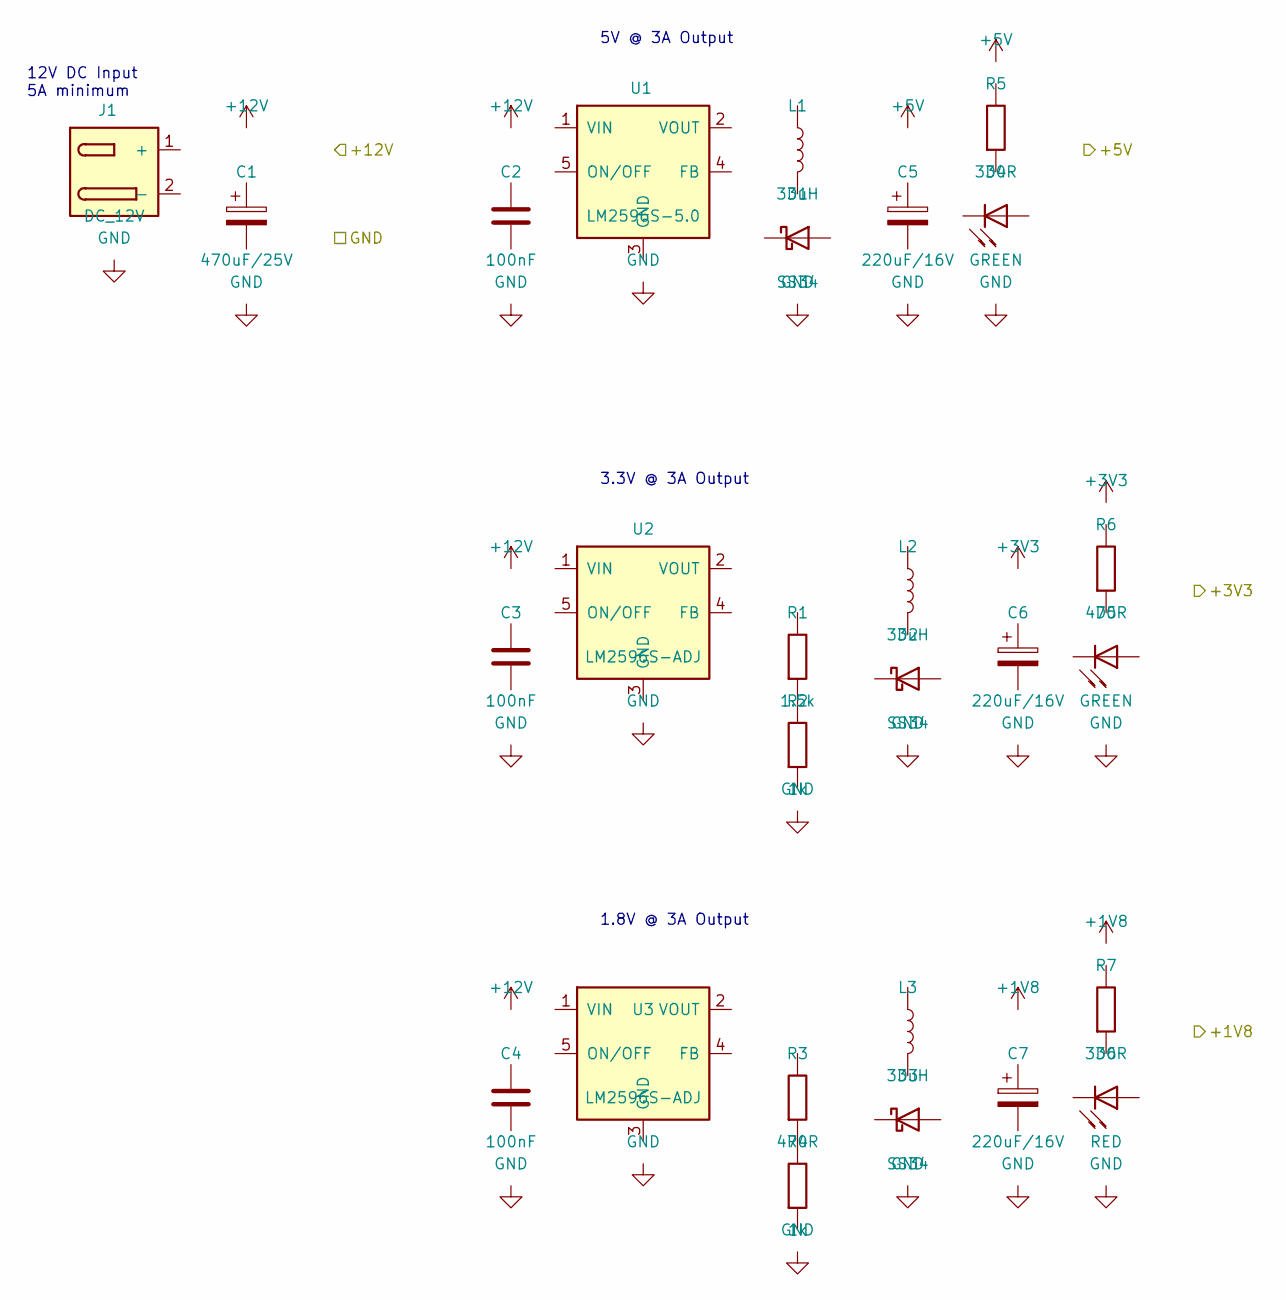
[picture p43: schematic fcBoard_Power.kicad_sch]

Parts:
C1: 470uF/25V; CAP-SMD_BD10.0-L10.0-W10.0-LS11.2-FD; LCSC Part C72505
C2, C3, C4: 100nF; C0402; LCSC Part C11702
C5, C6, C7: 220uF/16V; CAP-SMD_BD8.0-L8.3-W8.3-LS9.0-FD; LCSC Part C72499
D1, D2, D3: SS34; SMA_L4.3-W2.6-LS5.2-RD; LCSC Part C35722
D4, D5: GREEN; LED0603-RD; LCSC Part C2286
D6: RED; LED0603-RD; LCSC Part C2290
J1: DC_12V; BarrelJack_Horizontal
L1, L2, L3: 33uH; IND-SMD_L7.3-W7.3; LCSC Part C90748
R1: 1.5k; R0402; LCSC Part C25077
R2, R4: 1k; R0402; LCSC Part C25905
R3, R6: 470R; R0402; LCSC Part C25087
R5, R7: 330R; R0402; LCSC Part C72038
U1: LM2596S-5.0; TO-263-5_TabPin3; LCSC Part C347421
U2, U3: LM2596S-ADJ; TO-263-5_TabPin3; LCSC Part C29781

Connections:
unnamed: R1.2, R2.1
unnamed: R3.2, R4.1

Notes on the sheet:
1.8V @ 3A Output
12V DC Input 5A minimum
5V @ 3A Output
3.3V @ 3A Output
