raonslab2/fcBoardKicad/fcBoard_Power_Clean_v1.kicad_sch

## KiCad design fcBoard_Power_Clean_v1.kicad_sch (2025-12-12)

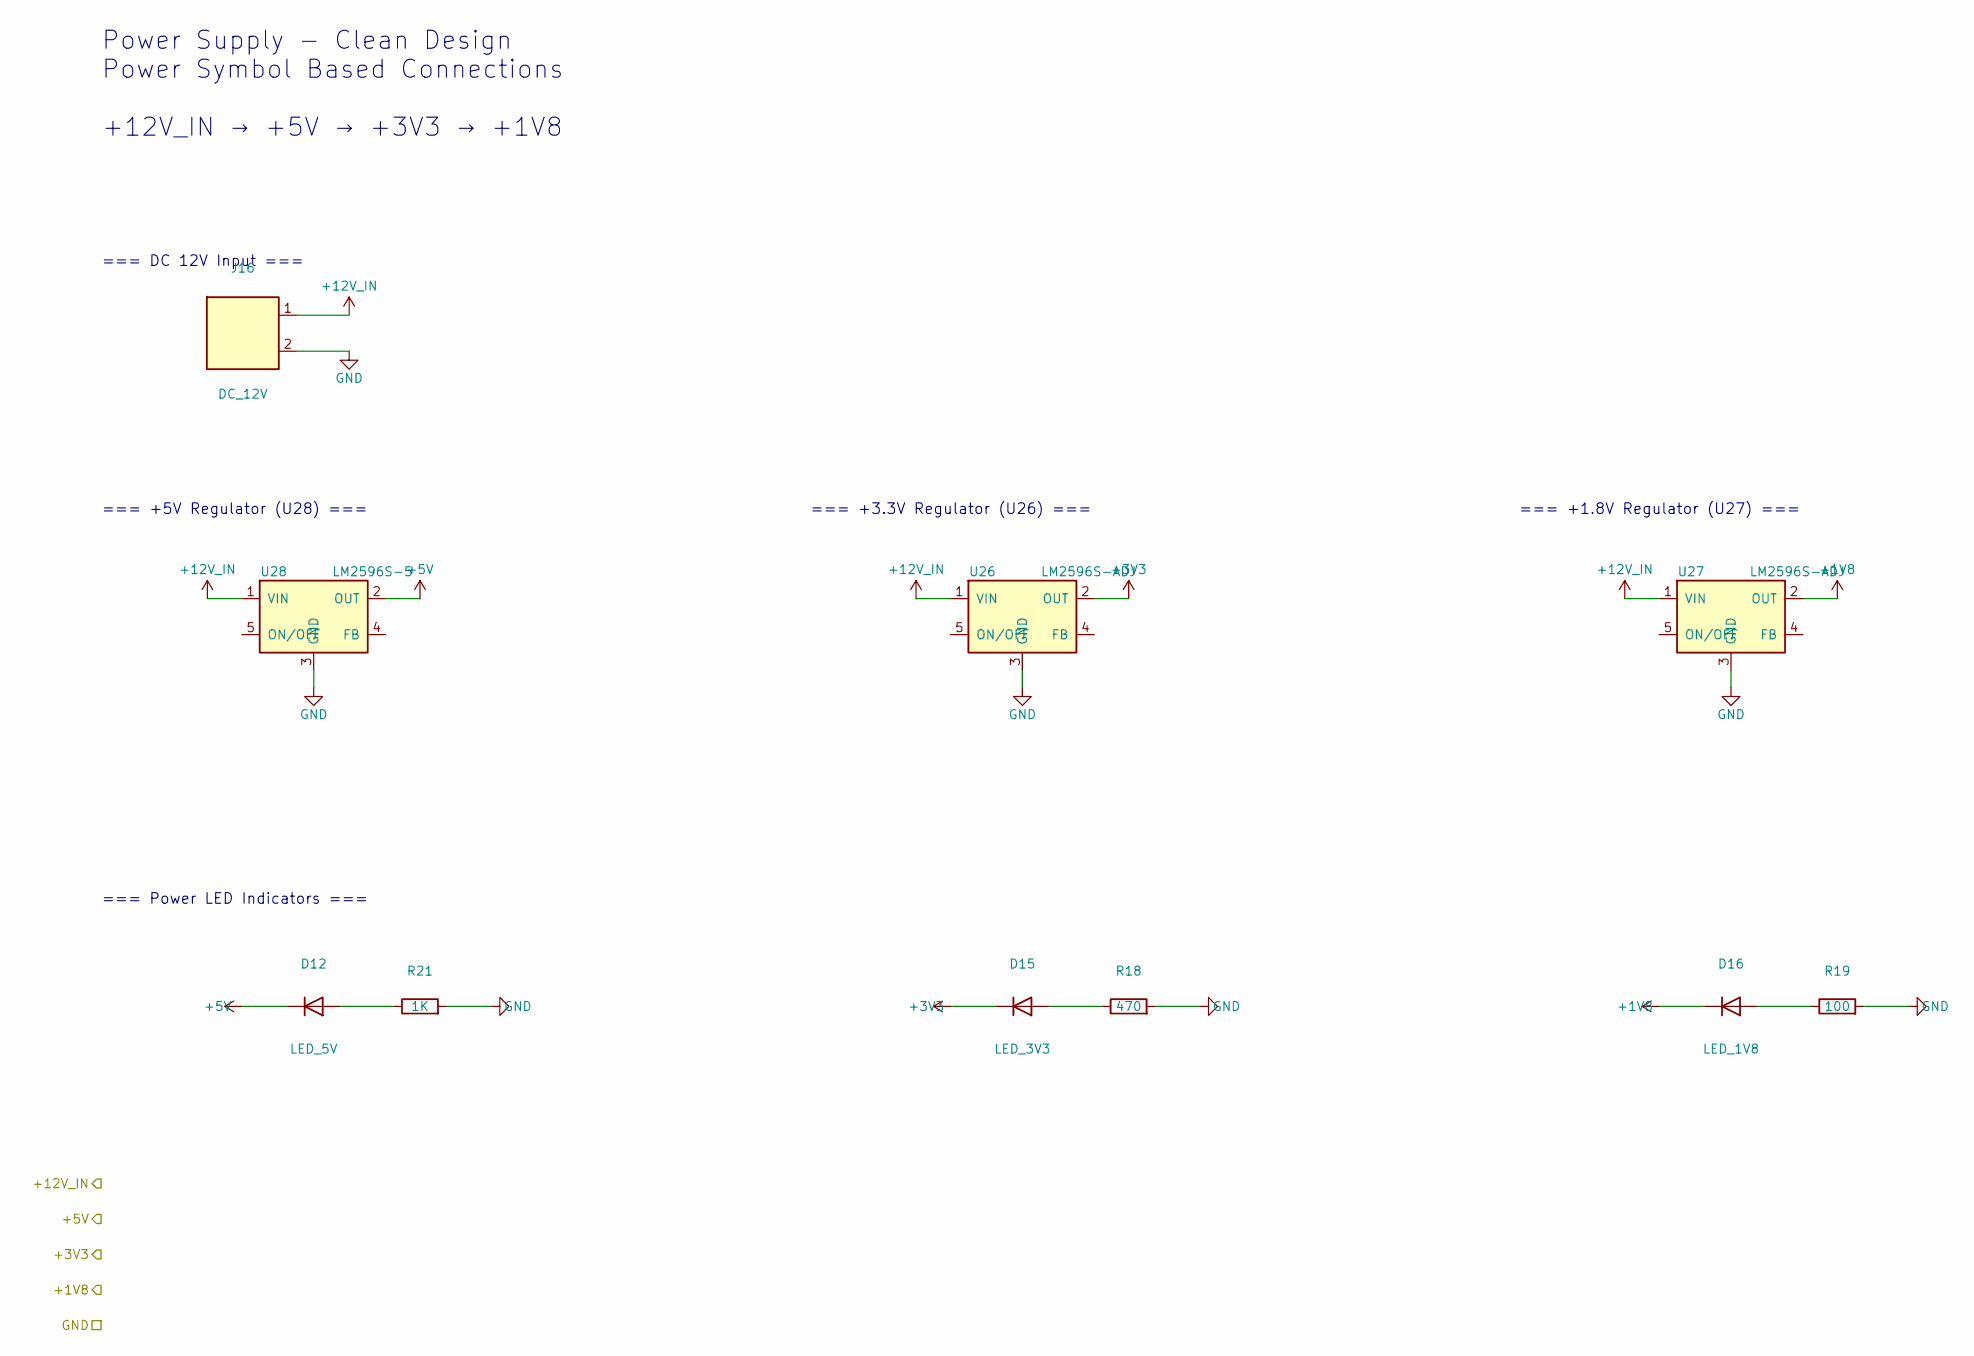
[picture p44: schematic fcBoard_Power_Clean_v1.kicad_sch]

Parts:
D12: LED_5V; LED_0603_1608Metric
D15: LED_3V3; LED_0603_1608Metric
D16: LED_1V8; LED_0603_1608Metric
J16: DC_12V; BarrelJack_Horizontal
R18: 470; R_0402_1005Metric
R19: 100; R_0402_1005Metric
R21: 1K; R_0402_1005Metric
U26, U27: LM2596S-ADJ; TO-263-5_TabPin3
U28: LM2596S-5; TO-263-5_TabPin3

Connections:
+1V8: D16.1 (K), U27.2 (OUT)
+3V3: D15.1 (K), U26.2 (OUT)
+5V: D12.1 (K), U28.2 (OUT)
+12V_IN: J16.1, U26.1 (VIN), U27.1 (VIN), U28.1 (VIN)
GND: J16.2, R18.2, R19.2, R21.2, U26.3 (GND), U27.3 (GND), U28.3 (GND)
unnamed: D12.2 (A), R21.1
unnamed: D15.2 (A), R18.1
unnamed: D16.2 (A), R19.1

Notes on the sheet:
Power Supply - Clean Design Power Symbol Based Connections +12V_IN → +5V → +3V3 → +1V8
=== DC 12V Input ===
=== +5V Regulator (U28) ===
=== +3.3V Regulator (U26) ===
=== +1.8V Regulator (U27) ===
=== Power LED Indicators ===
