raonslab2/fcBoardKicad/fcBoard_Reset.kicad_sch

## KiCad design fcBoard_Reset.kicad_sch (2025-12-12)

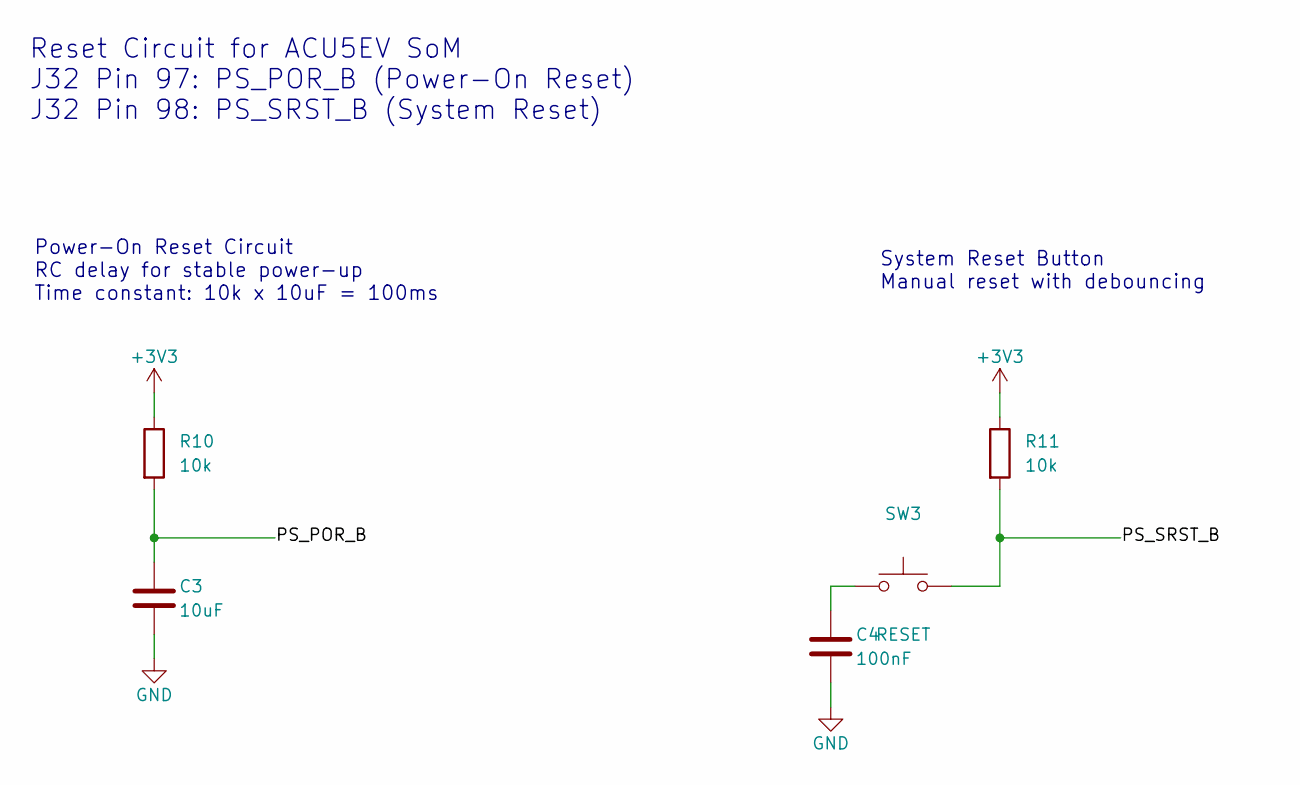
[picture p46: schematic fcBoard_Reset.kicad_sch]

Parts:
C3: 10uF; C_0603_1608Metric
C4: 100nF; C_0402_1005Metric
R10, R11: 10k; R_0402_1005Metric
SW3: RESET; SW_Push_1TS009xxxx-xxxx-xxxx_6x6x5mm

Connections:
+3V3: R10.1, R11.1
GND: C3.2, C4.2
unnamed: C4.1, SW3.1
PS_POR_B: C3.1, R10.2
PS_SRST_B: R11.2, SW3.2

Notes on the sheet:
Power-On Reset Circuit RC delay for stable power-up Time constant: 10k x 10uF = 100ms
System Reset Button Manual reset with debouncing
Reset Circuit for ACU5EV SoM J32 Pin 97: PS_POR_B (Power-On Reset) J32 Pin 98: PS_SRST_B (System Reset)
