raonslab2/fcBoardKicad/fcBoard_USB.kicad_sch

## KiCad design fcBoard_USB.kicad_sch (2025-12-14)

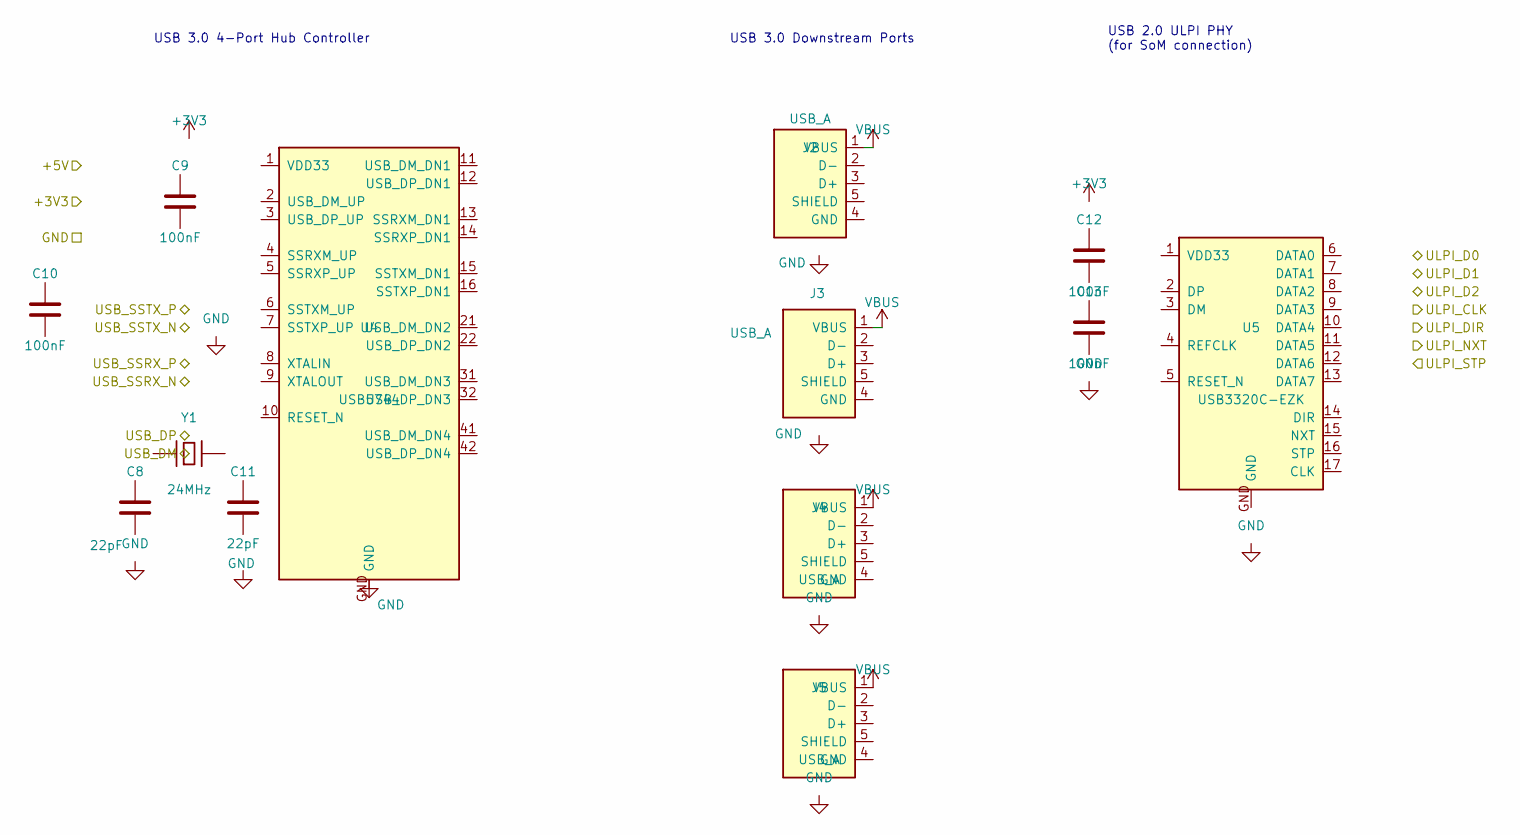
[picture p47: schematic fcBoard_USB.kicad_sch]

Parts:
C8, C11: 22pF; C0402; LCSC Part C1555
C9, C10, C12, C13: 100nF; C0402; LCSC Part C11702
J2, J3, J4, J5: USB_A; USB-A-TH_USB-A-F-90; LCSC Part C46406
U4: USB5744; QFN-56-1EP_7x7mm_P0.4mm_EP5.6x5.6mm; LCSC Part C132377
U5: USB3320C-EZK; QFN-32-1EP_5x5mm_P0.5mm_EP3.6x3.6mm; LCSC Part C129386
Y1: 24MHz; HC-49S_L11.0-W4.6; LCSC Part C9009

Connections:
VBUS: J2.1 (VBUS), J3.1 (VBUS), J4.1 (VBUS), J5.1 (VBUS)

Notes on the sheet:
USB 3.0 Downstream Ports
USB 2.0 ULPI PHY (for SoM connection)
USB 3.0 4-Port Hub Controller
