raonslab2/fcBoardKicad/gpio.kicad_sch

## KiCad design gpio.kicad_sch (2025-12-12)

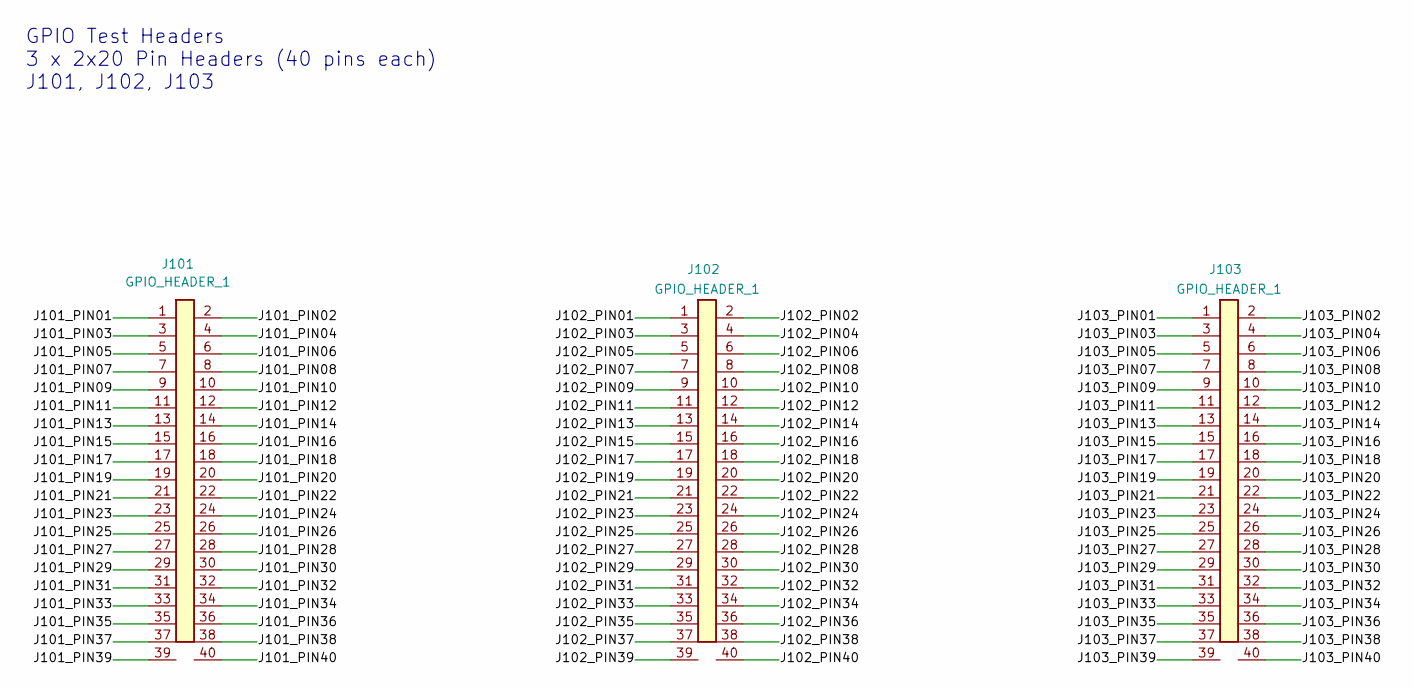
[picture p48: schematic gpio.kicad_sch]

Parts:
J101, J102, J103: GPIO_HEADER_1; PinHeader_2x20_P2.54mm_Vertical

Connections:
J101_PIN01: J101.1
J101_PIN02: J101.2
J101_PIN03: J101.3
J101_PIN04: J101.4
J101_PIN05: J101.5
J101_PIN06: J101.6
J101_PIN07: J101.7
J101_PIN08: J101.8
J101_PIN09: J101.9
J101_PIN10: J101.10
J101_PIN11: J101.11
J101_PIN12: J101.12
J101_PIN13: J101.13
J101_PIN14: J101.14
J101_PIN15: J101.15
J101_PIN16: J101.16
J101_PIN17: J101.17
J101_PIN18: J101.18
J101_PIN19: J101.19
J101_PIN20: J101.20
J101_PIN21: J101.21
J101_PIN22: J101.22
J101_PIN23: J101.23
J101_PIN24: J101.24
J101_PIN25: J101.25
J101_PIN26: J101.26
J101_PIN27: J101.27
J101_PIN28: J101.28
J101_PIN29: J101.29
J101_PIN30: J101.30
J101_PIN31: J101.31
J101_PIN32: J101.32
J101_PIN33: J101.33
J101_PIN34: J101.34
J101_PIN35: J101.35
J101_PIN36: J101.36
J101_PIN37: J101.37
J101_PIN38: J101.38
J101_PIN39: J101.39
J101_PIN40: J101.40
J102_PIN01: J102.1
J102_PIN02: J102.2
J102_PIN03: J102.3
J102_PIN04: J102.4
J102_PIN05: J102.5
J102_PIN06: J102.6
J102_PIN07: J102.7
J102_PIN08: J102.8
J102_PIN09: J102.9
J102_PIN10: J102.10
J102_PIN11: J102.11
J102_PIN12: J102.12
J102_PIN13: J102.13
J102_PIN14: J102.14
J102_PIN15: J102.15
J102_PIN16: J102.16
J102_PIN17: J102.17
J102_PIN18: J102.18
J102_PIN19: J102.19
J102_PIN20: J102.20
J102_PIN21: J102.21
J102_PIN22: J102.22
J102_PIN23: J102.23
J102_PIN24: J102.24
J102_PIN25: J102.25
J102_PIN26: J102.26
J102_PIN27: J102.27
J102_PIN28: J102.28
J102_PIN29: J102.29
J102_PIN30: J102.30
J102_PIN31: J102.31
J102_PIN32: J102.32
J102_PIN33: J102.33
J102_PIN34: J102.34
J102_PIN35: J102.35
J102_PIN36: J102.36
J102_PIN37: J102.37
J102_PIN38: J102.38
J102_PIN39: J102.39
J102_PIN40: J102.40
J103_PIN01: J103.1
J103_PIN02: J103.2
J103_PIN03: J103.3
J103_PIN04: J103.4
J103_PIN05: J103.5
J103_PIN06: J103.6
J103_PIN07: J103.7
J103_PIN08: J103.8
J103_PIN09: J103.9
J103_PIN10: J103.10
J103_PIN11: J103.11
J103_PIN12: J103.12
J103_PIN13: J103.13
J103_PIN14: J103.14
J103_PIN15: J103.15
J103_PIN16: J103.16
J103_PIN17: J103.17
J103_PIN18: J103.18
J103_PIN19: J103.19
J103_PIN20: J103.20
J103_PIN21: J103.21
J103_PIN22: J103.22
J103_PIN23: J103.23
J103_PIN24: J103.24
J103_PIN25: J103.25
J103_PIN26: J103.26
J103_PIN27: J103.27
J103_PIN28: J103.28
J103_PIN29: J103.29
J103_PIN30: J103.30
J103_PIN31: J103.31
J103_PIN32: J103.32
J103_PIN33: J103.33
J103_PIN34: J103.34
J103_PIN35: J103.35
J103_PIN36: J103.36
J103_PIN37: J103.37
J103_PIN38: J103.38
J103_PIN39: J103.39
J103_PIN40: J103.40

Notes on the sheet:
GPIO Test Headers 3 x 2x20 Pin Headers (40 pins each) J101, J102, J103
