raonslab2/fcBoardKicad/temp_backup/fcBoard_Ethernet.kicad_sch

## KiCad design temp_backup/fcBoard_Ethernet.kicad_sch (2025-12-12)

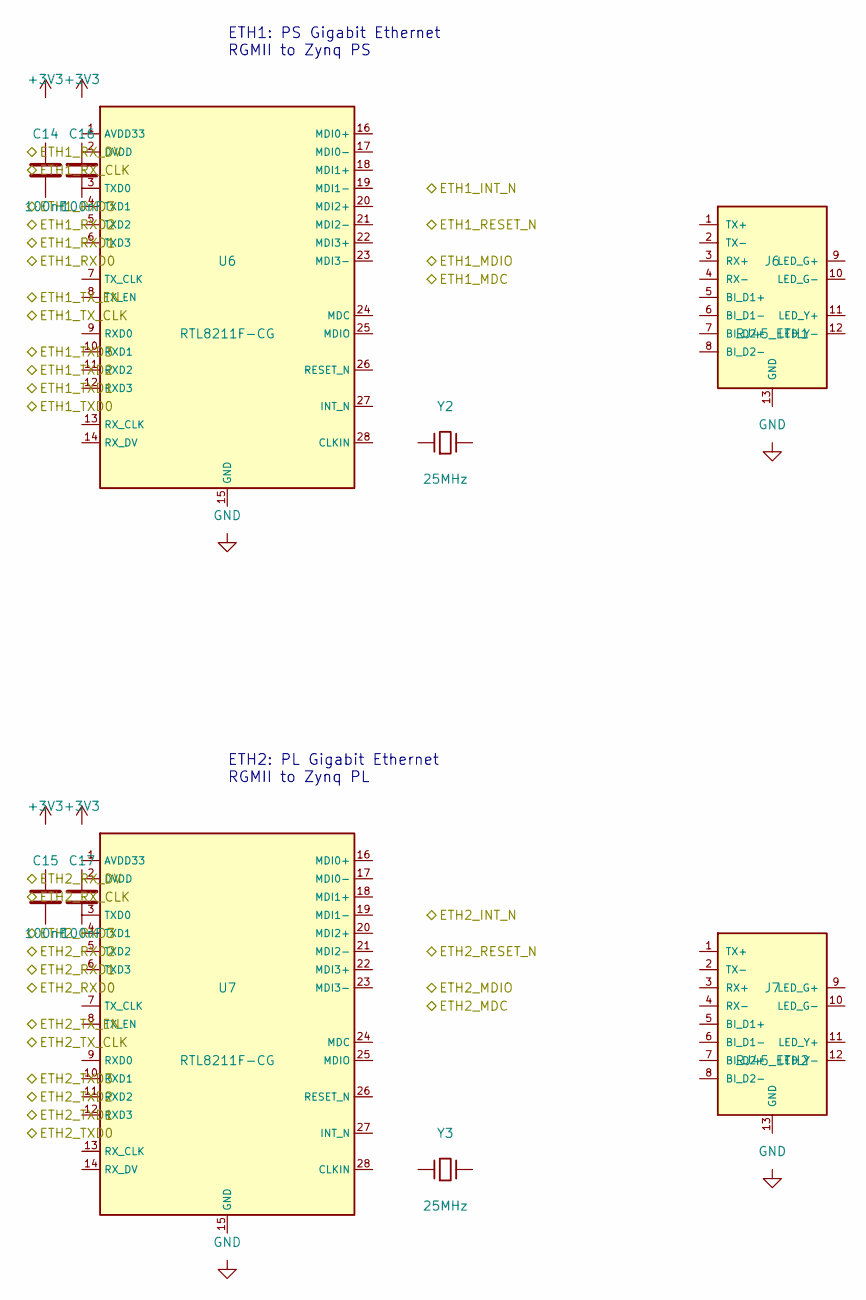
[picture p49: schematic fcBoard_Ethernet.kicad_sch]

Parts:
C14, C15, C16, C17: 100nF; C0402; LCSC Part C11702
J6: RJ45_ETH1; RJ45_Amphenol_RJMG1BD3B8K1ANR
J7: RJ45_ETH2; RJ45_Amphenol_RJMG1BD3B8K1ANR
U6, U7: RTL8211F-CG; QFN-48-1EP_6x6mm_P0.4mm
Y2, Y3: 25MHz; Crystal_SMD_3215-2Pin_3.2x1.5mm

Notes on the sheet:
ETH2: PL Gigabit Ethernet RGMII to Zynq PL
ETH1: PS Gigabit Ethernet RGMII to Zynq PS
