raonslab2/fcBoardKicad/temp_backup/fcBoard_HDMI.kicad_sch

## KiCad design temp_backup/fcBoard_HDMI.kicad_sch (2025-12-12)

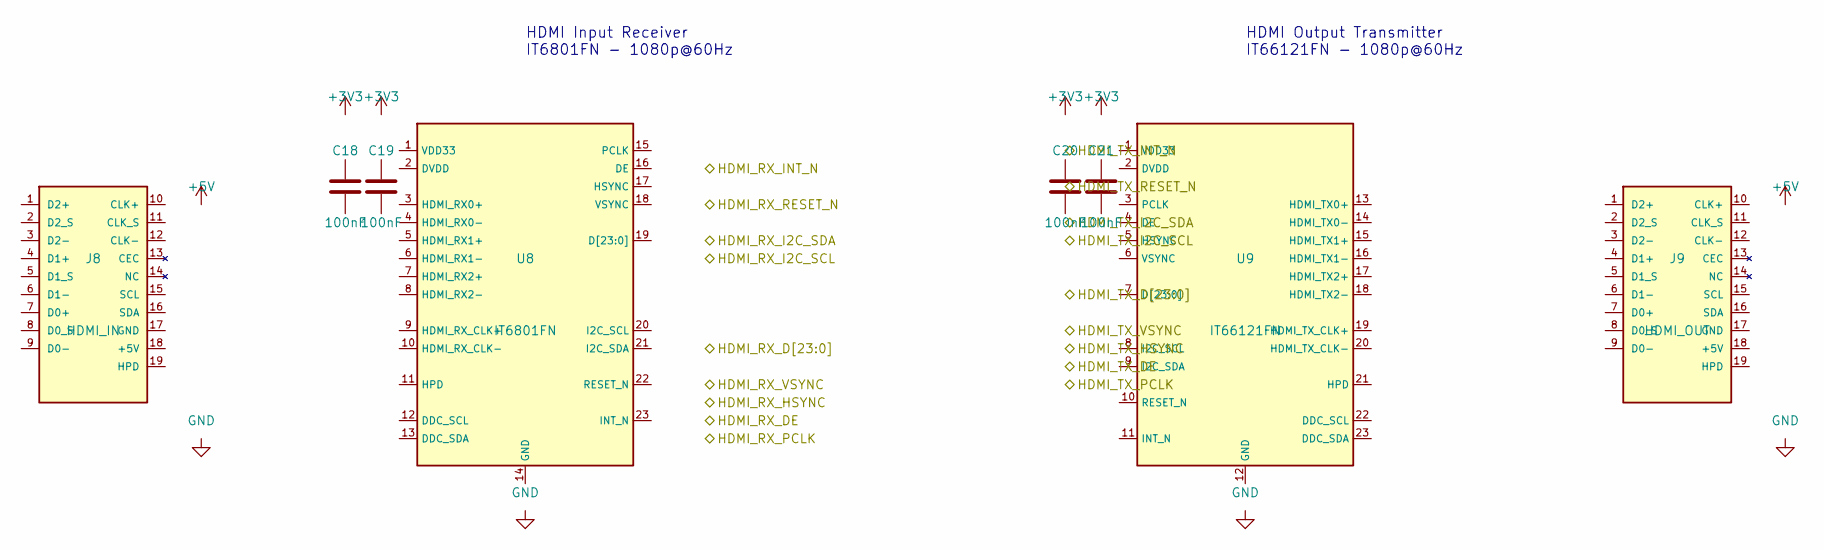
[picture p50: schematic fcBoard_HDMI.kicad_sch]

Parts:
C18, C19, C20, C21: 100nF; C0402; LCSC Part C11702
J8: HDMI_IN; HDMI-A_Molex_46765-0x01
J9: HDMI_OUT; HDMI-A_Molex_46765-0x01
U8: IT6801FN; LQFP-64_10x10mm_P0.5mm
U9: IT66121FN; LQFP-64_10x10mm_P0.5mm

Notes on the sheet:
HDMI Input Receiver IT6801FN - 1080p@60Hz
HDMI Output Transmitter IT66121FN - 1080p@60Hz
