raonslab2/fcBoardKicad/temp_backup/fcBoard_Peripherals.kicad_sch

## KiCad design temp_backup/fcBoard_Peripherals.kicad_sch (2025-12-12)

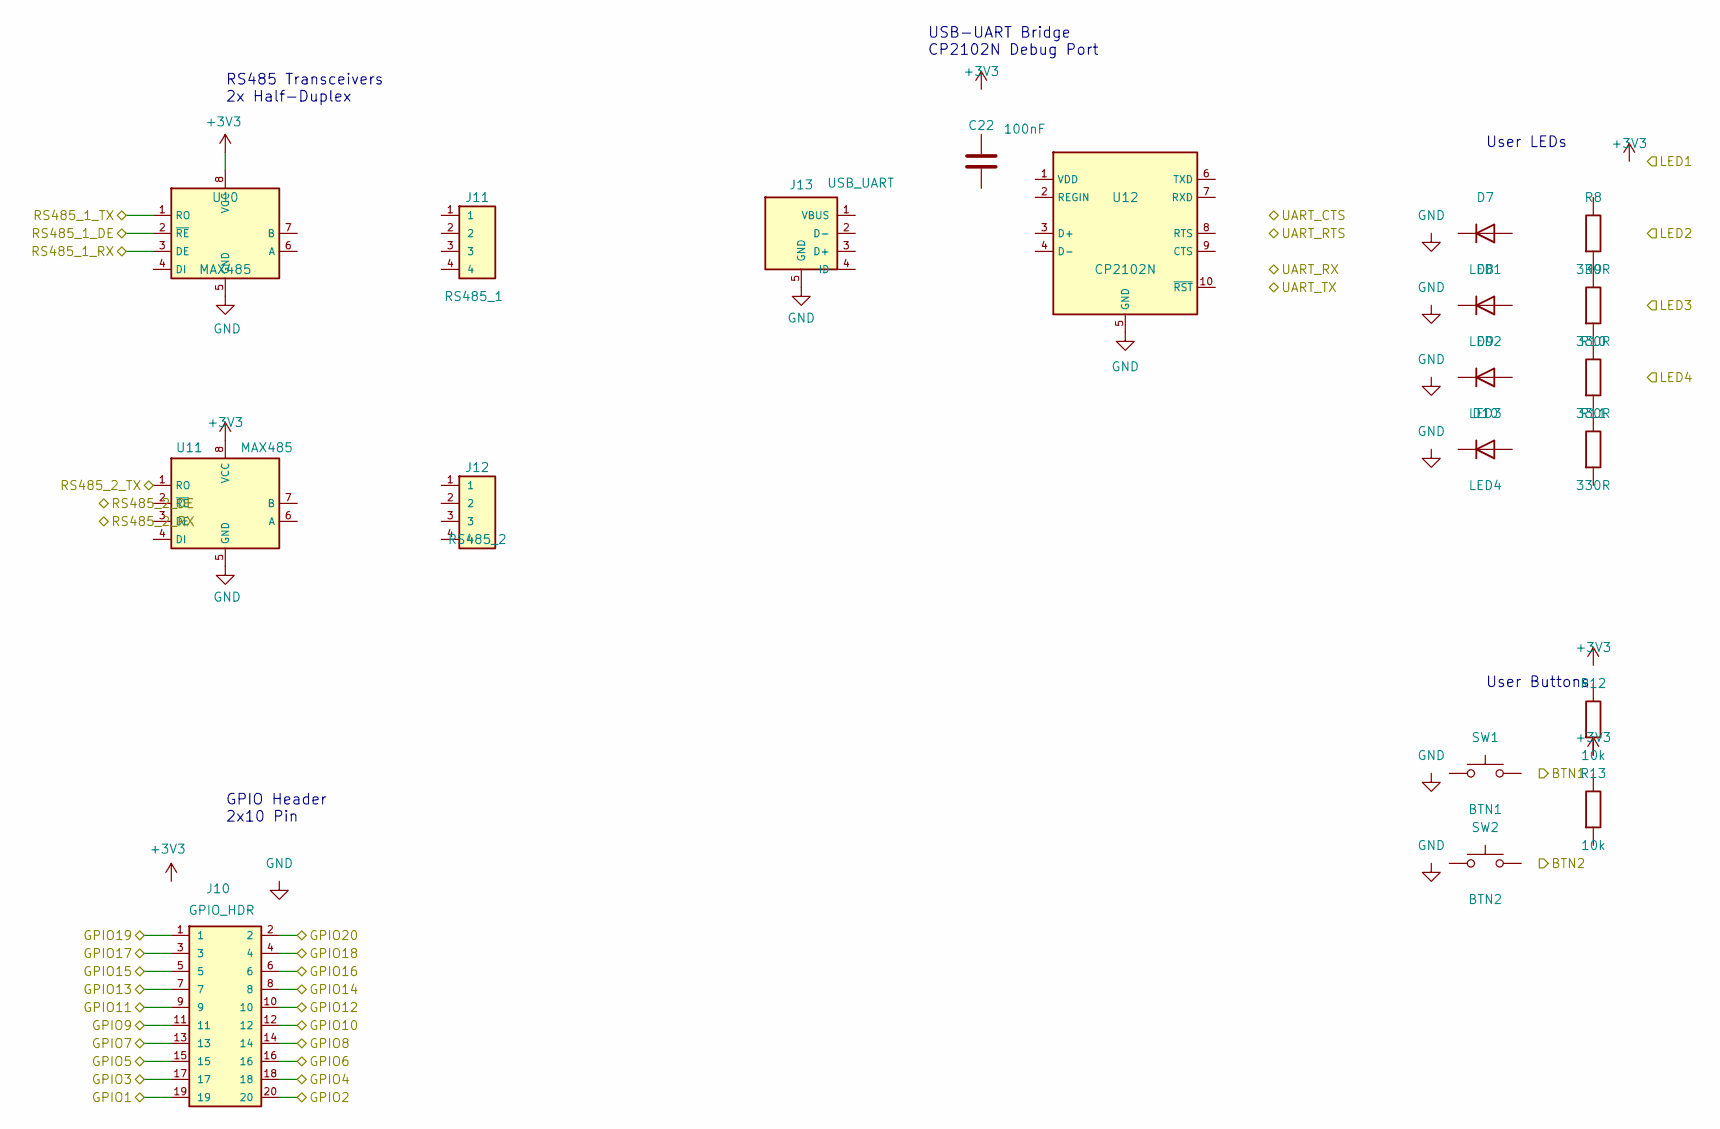
[picture p51: schematic fcBoard_Peripherals.kicad_sch]

Parts:
C22: 100nF; C0402; LCSC Part C11702
D7: LED1; LED0603-RD; LCSC Part C2286
D8: LED2; LED0603-RD; LCSC Part C2286
D9: LED3; LED0603-RD; LCSC Part C2286
D10: LED4; LED0603-RD; LCSC Part C2286
J10: GPIO_HDR; PinHeader_2x10_P2.54mm_Vertical
J11: RS485_1; PinHeader_1x04_P2.54mm_Vertical
J12: RS485_2; PinHeader_1x04_P2.54mm_Vertical
J13: USB_UART; USB_Micro-B_Molex_47346-0001
R8, R9, R10, R11: 330R; R0402; LCSC Part C72038
R12, R13: 10k; R0402
SW1: BTN1; SW_SPST_TL3342
SW2: BTN2; SW_SPST_TL3342
U10, U11: MAX485; SOIC-8_3.9x4.9mm_P1.27mm
U12: CP2102N; QFN-28-1EP_5x5mm_P0.5mm

Connections:
+3V3: R12.2, U10.8 (VCC), U11.8 (VCC)
GND: J13.5 (GND), U10.5 (GND), U11.5 (GND), U12.5 (GND)
GPIO1: J10.19
GPIO2: J10.20
GPIO3: J10.17
GPIO4: J10.18
GPIO5: J10.15
GPIO6: J10.16
GPIO7: J10.13
GPIO8: J10.14
GPIO9: J10.11
GPIO10: J10.12
GPIO11: J10.9
GPIO12: J10.10
GPIO13: J10.7
GPIO14: J10.8
GPIO15: J10.5
GPIO16: J10.6
GPIO17: J10.3
GPIO18: J10.4
GPIO19: J10.1
GPIO20: J10.2
unnamed: R8.2, R9.1
unnamed: R9.2, R10.1
unnamed: R10.2, R11.1
RS485_1_DE: U10.2 (~RE)
RS485_1_RX: U10.3 (DE)
RS485_1_TX: U10.1 (RO)
RS485_2_TX: U11.1 (RO)

Notes on the sheet:
GPIO Header 2x10 Pin
User Buttons
User LEDs
USB-UART Bridge CP2102N Debug Port
RS485 Transceivers 2x Half-Duplex
