raonslab2/fcBoardKicad/temp_backup/fcBoard_USB.kicad_sch

## KiCad design temp_backup/fcBoard_USB.kicad_sch (2025-12-12)

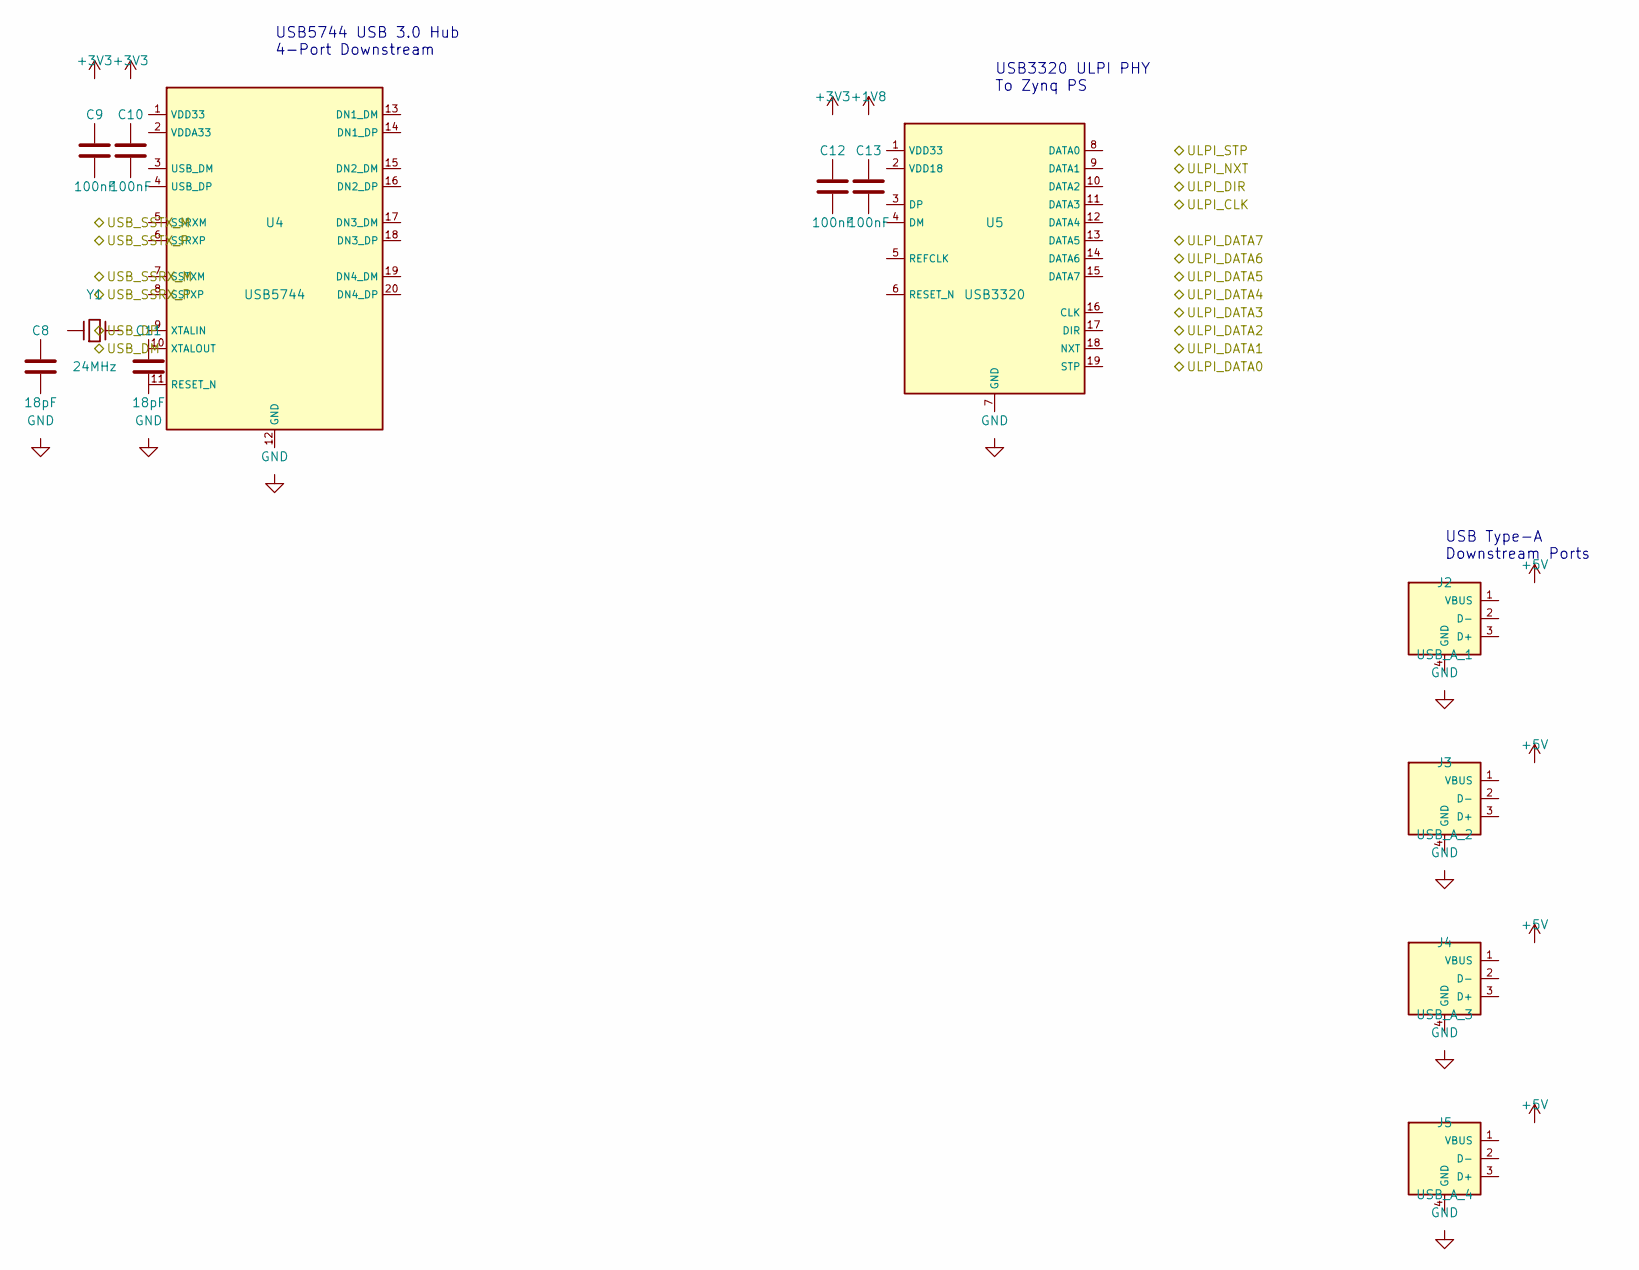
[picture p52: schematic fcBoard_USB.kicad_sch]

Parts:
C8, C11: 18pF; C0402
C9, C10, C12, C13: 100nF; C0402; LCSC Part C11702
J2: USB_A_1; USB_A_Molex_105057-0001
J3: USB_A_2; USB_A_Molex_105057-0001
J4: USB_A_3; USB_A_Molex_105057-0001
J5: USB_A_4; USB_A_Molex_105057-0001
U4: USB5744; LQFP-48_7x7mm_P0.5mm
U5: USB3320; QFN-32-1EP_5x5mm_P0.5mm
Y1: 24MHz; Crystal_SMD_3215-2Pin_3.2x1.5mm

Notes on the sheet:
USB5744 USB 3.0 Hub 4-Port Downstream
USB Type-A Downstream Ports
USB3320 ULPI PHY To Zynq PS
