raonslab2/fcBoardKicad/out/fcboard_power/fcBoard_Power_Auto.kicad_sch

## KiCad design out/fcboard_power/fcBoard_Power_Auto.kicad_sch (2025-12-12)

Schematic: fcBoard_Power_Auto.kicad_sch

Parts:
C1: 220uF/25V
C2, C4: 220uF/10V
C3, C5: 10uF
C6: 100uF/10V
C7, C8, C9: 100nF
D1, D3, D5: SS34
D2: Green
D4: Yellow
D6: Red
J1: DC Jack 12V
L1, L2, L3: 33uH
R1, R3, R6: 1k
R2: 3.3k
R4: 470
R5: 1.5k
R7: 100
U1: LM2596S-5.0
U2, U3: LM2596S-ADJ

Notes on the sheet:
fcBoard_Power_Auto Auto-generated schematic Parts: 29
