raonslab2/fcBoardKicad/out/fcboard_usb/fcBoard_USB_Auto.kicad_sch

## KiCad design out/fcboard_usb/fcBoard_USB_Auto.kicad_sch (2025-12-12)

Schematic: fcBoard_USB_Auto.kicad_sch

Parts:
C1, C2: 18pF
C3, C5, C8: 100nF
C4, C6: 10uF
C7: 100uF
J1: USB-A Port 1
J2: USB-A Port 2
J3: USB-A Port 3
J4: USB-A Port 4
R1, R2: 10k
U1: USB5744; LCSC Part C132563
U2: USB3320; LCSC Part C132942
Y1: 24MHz

Notes on the sheet:
fcBoard_USB_Auto Auto-generated schematic Parts: 17
