raonslab2/fcBoardKicad/out/hierarchical_board/Power.kicad_sch

## KiCad design out/hierarchical_board/Power.kicad_sch (2025-12-12)

Schematic: Power.kicad_sch

Parts:
C1, C2: 220uF; LCSC Part C134799
D1: SS34
D2: Green
J1: DC Jack 12V
L1: 33uH
R1: 1k
U1: LM2596S-5.0

Notes on the sheet:
Power Parts: 8
