raonslab2/fcBoardKicad/out/hierarchical_board/USB.kicad_sch

## KiCad design out/hierarchical_board/USB.kicad_sch (2025-12-12)

Schematic: USB.kicad_sch

Parts:
C3: 100nF
C4: 10uF
J2: USB-A
R2, R3: 22R; LCSC Part C17560

Notes on the sheet:
USB Parts: 5
