raonslab2/fcBoardKicad/out/hierarchical_ports_obj/Digital.kicad_sch

## KiCad design out/hierarchical_ports_obj/Digital.kicad_sch (2025-12-12)

Schematic: Digital.kicad_sch

Parts:
C3: 100nF
R1, R2: 10k; LCSC Part C17414

Notes on the sheet:
Digital Parts: 3
