raonslab2/fcBoardKicad/out/hierarchical_ports_obj/Power.kicad_sch

## KiCad design out/hierarchical_ports_obj/Power.kicad_sch (2025-12-12)

Schematic: Power.kicad_sch

Parts:
C1, C2: 220uF
J1: DC Jack
U1: LM2596S-5.0

Notes on the sheet:
Power Parts: 4
