raonslab2/fcBoardKicad/out/power_board/PowerBoard_5V_3V3.kicad_sch

## KiCad design out/power_board/PowerBoard_5V_3V3.kicad_sch (2025-12-12)

Schematic: PowerBoard_5V_3V3.kicad_sch

Parts:
C1, C4: 100uF
C2: 220uF
C3: 10uF
D1, D3: SS34
D2: Green
D4: Yellow
J1: DC Jack 12V
L1, L2: 33uH
R1: 1k
R2: 330
U1: LM2596S-5.0
U2: LM2596S-ADJ

Notes on the sheet:
PowerBoard_5V_3V3 Auto-generated schematic Parts: 15
