raonslab2/fcBoardKicad/out/test_invalid/TestInvalidPin.kicad_sch

## KiCad design out/test_invalid/TestInvalidPin.kicad_sch (2025-12-12)

Schematic: TestInvalidPin.kicad_sch

Parts:
R1: 10k
R2: 4.7k

Notes on the sheet:
TestInvalidPin Auto-generated schematic Parts: 2
