raonslab2/fcBoardKicad/out/test_resolve_fail/TestResolveFail.kicad_sch

## KiCad design out/test_resolve_fail/TestResolveFail.kicad_sch (2025-12-12)

Schematic: TestResolveFail.kicad_sch

Parts:
R1: 10k
U1: Unknown IC

Notes on the sheet:
TestResolveFail Auto-generated schematic Parts: 2
