raonslab2/fcBoardKicad/scripts/generate_peripherals_sch.py

#!/usr/bin/env python3
"""
KiCad Peripherals 회로도 생성 스크립트
SD Card, Debug UART, CAN x2, RS485 x2, GPIO, etc.
"""

import uuid
import os

def gen_uuid():
    return str(uuid.uuid4())

def create_peripherals_schematic():
    """Peripherals 회로도 생성"""

    sch = '''(kicad_sch
  (version 20231120)
  (generator "eeschema")
  (generator_version "8.0")
  (uuid "{main_uuid}")
  (paper "A3")
  (title_block
    (title "Peripherals")
    (date "2024-11-30")
    (rev "0.1")
    (company "fcBoard Project")
    (comment 1 "SD Card, UART, CAN x2, RS485 x2, GPIO")
  )

  (lib_symbols
    {lib_symbols}
  )

  {components}

  {wires}

  {labels}

  {power_symbols}
)
'''

    lib_symbols = generate_lib_symbols()
    components = generate_components()
    wires = generate_wires()
    labels = generate_labels()
    power_symbols = generate_power_symbols()

    result = sch.format(
        main_uuid=gen_uuid(),
        lib_symbols=lib_symbols,
        components=components,
        wires=wires,
        labels=labels,
        power_symbols=power_symbols
    )

    return result

def generate_lib_symbols():
    """라이브러리 심볼 정의"""

    symbols = '''
    (symbol "Connector:MicroSD_Card" (exclude_from_sim no) (in_bom yes) (on_board yes)
      (property "Reference" "J" (at 0 15.24 0) (effects (font (size 1.27 1.27))))
      (property "Value" "MicroSD_Card" (at 0 12.7 0) (effects (font (size 1.27 1.27))))
      (property "Footprint" "Connector_Card:microSD_HC_Wuerth_693072010801" (at 0 0 0) (effects (font (size 1.27 1.27)) hide))
      (property "Datasheet" "" (at 0 0 0) (effects (font (size 1.27 1.27)) hide))
      (symbol "MicroSD_Card_0_1"
        (rectangle (start -7.62 10.16) (end 7.62 -10.16) (stroke (width 0.254) (type default)) (fill (type background)))
      )
      (symbol "MicroSD_Card_1_1"
        (pin bidirectional line (at -10.16 7.62 0) (length 2.54) (name "DAT2" (effects (font (size 1.27 1.27)))) (number "1" (effects (font (size 1.27 1.27)))))
        (pin bidirectional line (at -10.16 5.08 0) (length 2.54) (name "DAT3/CD" (effects (font (size 1.27 1.27)))) (number "2" (effects (font (size 1.27 1.27)))))
        (pin bidirectional line (at -10.16 2.54 0) (length 2.54) (name "CMD" (effects (font (size 1.27 1.27)))) (number "3" (effects (font (size 1.27 1.27)))))
        (pin power_in line (at -10.16 0 0) (length 2.54) (name "VDD" (effects (font (size 1.27 1.27)))) (number "4" (effects (font (size 1.27 1.27)))))
        (pin input line (at -10.16 -2.54 0) (length 2.54) (name "CLK" (effects (font (size 1.27 1.27)))) (number "5" (effects (font (size 1.27 1.27)))))
        (pin power_in line (at -10.16 -5.08 0) (length 2.54) (name "VSS" (effects (font (size 1.27 1.27)))) (number "6" (effects (font (size 1.27 1.27)))))
        (pin bidirectional line (at -10.16 -7.62 0) (length 2.54) (name "DAT0" (effects (font (size 1.27 1.27)))) (number "7" (effects (font (size 1.27 1.27)))))
        (pin bidirectional line (at 10.16 7.62 180) (length 2.54) (name "DAT1" (effects (font (size 1.27 1.27)))) (number "8" (effects (font (size 1.27 1.27)))))
        (pin input line (at 10.16 -7.62 180) (length 2.54) (name "CD" (effects (font (size 1.27 1.27)))) (number "9" (effects (font (size 1.27 1.27)))))
      )
    )

    (symbol "Interface_USB:CP2102N" (exclude_from_sim no) (in_bom yes) (on_board yes)
      (property "Reference" "U" (at 0 16.51 0) (effects (font (size 1.27 1.27))))
      (property "Value" "CP2102N" (at 0 13.97 0) (effects (font (size 1.27 1.27))))
      (property "Footprint" "Package_DFN_QFN:QFN-28-1EP_5x5mm_P0.5mm_EP3.35x3.35mm" (at 0 0 0) (effects (font (size 1.27 1.27)) hide))
      (property "Datasheet" "https://www.silabs.com/documents/public/data-sheets/cp2102n-datasheet.pdf" (at 0 0 0) (effects (font (size 1.27 1.27)) hide))
      (symbol "CP2102N_0_1"
        (rectangle (start -10.16 12.7) (end 10.16 -12.7) (stroke (width 0.254) (type default)) (fill (type background)))
      )
      (symbol "CP2102N_1_1"
        (pin power_in line (at -12.7 10.16 0) (length 2.54) (name "VDD" (effects (font (size 1.27 1.27)))) (number "1" (effects (font (size 1.27 1.27)))))
        (pin bidirectional line (at -12.7 5.08 0) (length 2.54) (name "D+" (effects (font (size 1.27 1.27)))) (number "2" (effects (font (size 1.27 1.27)))))
        (pin bidirectional line (at -12.7 2.54 0) (length 2.54) (name "D-" (effects (font (size 1.27 1.27)))) (number "3" (effects (font (size 1.27 1.27)))))
        (pin power_in line (at -12.7 -10.16 0) (length 2.54) (name "GND" (effects (font (size 1.27 1.27)))) (number "4" (effects (font (size 1.27 1.27)))))
        (pin output line (at 12.7 10.16 180) (length 2.54) (name "TXD" (effects (font (size 1.27 1.27)))) (number "5" (effects (font (size 1.27 1.27)))))
        (pin input line (at 12.7 7.62 180) (length 2.54) (name "RXD" (effects (font (size 1.27 1.27)))) (number "6" (effects (font (size 1.27 1.27)))))
        (pin output line (at 12.7 2.54 180) (length 2.54) (name "RTS" (effects (font (size 1.27 1.27)))) (number "7" (effects (font (size 1.27 1.27)))))
        (pin input line (at 12.7 0 180) (length 2.54) (name "CTS" (effects (font (size 1.27 1.27)))) (number "8" (effects (font (size 1.27 1.27)))))
        (pin output line (at 12.7 -5.08 180) (length 2.54) (name "DTR" (effects (font (size 1.27 1.27)))) (number "9" (effects (font (size 1.27 1.27)))))
        (pin input line (at 12.7 -7.62 180) (length 2.54) (name "DSR" (effects (font (size 1.27 1.27)))) (number "10" (effects (font (size 1.27 1.27)))))
      )
    )

    (symbol "Interface_CAN_LIN:SN65HVD230" (exclude_from_sim no) (in_bom yes) (on_board yes)
      (property "Reference" "U" (at 0 10.16 0) (effects (font (size 1.27 1.27))))
      (property "Value" "SN65HVD230" (at 0 7.62 0) (effects (font (size 1.27 1.27))))
      (property "Footprint" "Package_SO:SOIC-8_3.9x4.9mm_P1.27mm" (at 0 0 0) (effects (font (size 1.27 1.27)) hide))
      (property "Datasheet" "http://www.ti.com/lit/ds/symlink/sn65hvd230.pdf" (at 0 0 0) (effects (font (size 1.27 1.27)) hide))
      (symbol "SN65HVD230_0_1"
        (rectangle (start -7.62 5.08) (end 7.62 -5.08) (stroke (width 0.254) (type default)) (fill (type background)))
      )
      (symbol "SN65HVD230_1_1"
        (pin input line (at -10.16 2.54 0) (length 2.54) (name "TXD" (effects (font (size 1.27 1.27)))) (number "1" (effects (font (size 1.27 1.27)))))
        (pin power_in line (at -10.16 -2.54 0) (length 2.54) (name "GND" (effects (font (size 1.27 1.27)))) (number "2" (effects (font (size 1.27 1.27)))))
        (pin power_in line (at 10.16 2.54 180) (length 2.54) (name "VCC" (effects (font (size 1.27 1.27)))) (number "3" (effects (font (size 1.27 1.27)))))
        (pin output line (at -10.16 0 0) (length 2.54) (name "RXD" (effects (font (size 1.27 1.27)))) (number "4" (effects (font (size 1.27 1.27)))))
        (pin no_connect line (at 10.16 0 180) (length 2.54) (name "NC" (effects (font (size 1.27 1.27)))) (number "5" (effects (font (size 1.27 1.27)))))
        (pin bidirectional line (at 10.16 -2.54 180) (length 2.54) (name "CANL" (effects (font (size 1.27 1.27)))) (number "6" (effects (font (size 1.27 1.27)))))
        (pin bidirectional line (at 10.16 -5.08 180) (length 2.54) (name "CANH" (effects (font (size 1.27 1.27)))) (number "7" (effects (font (size 1.27 1.27)))))
        (pin input line (at -10.16 -5.08 0) (length 2.54) (name "Rs" (effects (font (size 1.27 1.27)))) (number "8" (effects (font (size 1.27 1.27)))))
      )
    )

    (symbol "Interface_UART:MAX485" (exclude_from_sim no) (in_bom yes) (on_board yes)
      (property "Reference" "U" (at 0 10.16 0) (effects (font (size 1.27 1.27))))
      (property "Value" "MAX485" (at 0 7.62 0) (effects (font (size 1.27 1.27))))
      (property "Footprint" "Package_SO:SOIC-8_3.9x4.9mm_P1.27mm" (at 0 0 0) (effects (font (size 1.27 1.27)) hide))
      (property "Datasheet" "https://datasheets.maximintegrated.com/en/ds/MAX1487-MAX491.pdf" (at 0 0 0) (effects (font (size 1.27 1.27)) hide))
      (symbol "MAX485_0_1"
        (rectangle (start -7.62 5.08) (end 7.62 -5.08) (stroke (width 0.254) (type default)) (fill (type background)))
      )
      (symbol "MAX485_1_1"
        (pin output line (at -10.16 2.54 0) (length 2.54) (name "RO" (effects (font (size 1.27 1.27)))) (number "1" (effects (font (size 1.27 1.27)))))
        (pin input line (at -10.16 0 0) (length 2.54) (name "~{RE}" (effects (font (size 1.27 1.27)))) (number "2" (effects (font (size 1.27 1.27)))))
        (pin input line (at -10.16 -2.54 0) (length 2.54) (name "DE" (effects (font (size 1.27 1.27)))) (number "3" (effects (font (size 1.27 1.27)))))
        (pin input line (at -10.16 -5.08 0) (length 2.54) (name "DI" (effects (font (size 1.27 1.27)))) (number "4" (effects (font (size 1.27 1.27)))))
        (pin power_in line (at 10.16 -5.08 180) (length 2.54) (name "GND" (effects (font (size 1.27 1.27)))) (number "5" (effects (font (size 1.27 1.27)))))
        (pin bidirectional line (at 10.16 -2.54 180) (length 2.54) (name "A" (effects (font (size 1.27 1.27)))) (number "6" (effects (font (size 1.27 1.27)))))
        (pin bidirectional line (at 10.16 0 180) (length 2.54) (name "B" (effects (font (size 1.27 1.27)))) (number "7" (effects (font (size 1.27 1.27)))))
        (pin power_in line (at 10.16 2.54 180) (length 2.54) (name "VCC" (effects (font (size 1.27 1.27)))) (number "8" (effects (font (size 1.27 1.27)))))
      )
    )

    (symbol "Connector:USB_B_Micro" (exclude_from_sim no) (in_bom yes) (on_board yes)
      (property "Reference" "J" (at 0 7.62 0) (effects (font (size 1.27 1.27))))
      (property "Value" "USB_B_Micro" (at 0 5.08 0) (effects (font (size 1.27 1.27))))
      (property "Footprint" "Connector_USB:USB_Micro-B_Molex_47346-0001" (at 0 0 0) (effects (font (size 1.27 1.27)) hide))
      (property "Datasheet" "" (at 0 0 0) (effects (font (size 1.27 1.27)) hide))
      (symbol "USB_B_Micro_0_1"
        (rectangle (start -5.08 2.54) (end 5.08 -7.62) (stroke (width 0.254) (type default)) (fill (type background)))
      )
      (symbol "USB_B_Micro_1_1"
        (pin power_out line (at 7.62 0 180) (length 2.54) (name "VBUS" (effects (font (size 1.27 1.27)))) (number "1" (effects (font (size 1.27 1.27)))))
        (pin bidirectional line (at 7.62 -2.54 180) (length 2.54) (name "D-" (effects (font (size 1.27 1.27)))) (number "2" (effects (font (size 1.27 1.27)))))
        (pin bidirectional line (at 7.62 -5.08 180) (length 2.54) (name "D+" (effects (font (size 1.27 1.27)))) (number "3" (effects (font (size 1.27 1.27)))))
        (pin passive line (at -7.62 -2.54 0) (length 2.54) (name "ID" (effects (font (size 1.27 1.27)))) (number "4" (effects (font (size 1.27 1.27)))))
        (pin power_in line (at -7.62 -5.08 0) (length 2.54) (name "GND" (effects (font (size 1.27 1.27)))) (number "5" (effects (font (size 1.27 1.27)))))
      )
    )

    (symbol "Connector:Screw_Terminal_01x03" (exclude_from_sim no) (in_bom yes) (on_board yes)
      (property "Reference" "J" (at 0 5.08 0) (effects (font (size 1.27 1.27))))
      (property "Value" "Screw_Terminal_01x03" (at 0 -5.08 0) (effects (font (size 1.27 1.27))))
      (property "Footprint" "TerminalBlock:TerminalBlock_bornier-3_P5.08mm" (at 0 0 0) (effects (font (size 1.27 1.27)) hide))
      (property "Datasheet" "" (at 0 0 0) (effects (font (size 1.27 1.27)) hide))
      (symbol "Screw_Terminal_01x03_0_1"
        (rectangle (start -2.54 2.54) (end 2.54 -2.54) (stroke (width 0.254) (type default)) (fill (type background)))
      )
      (symbol "Screw_Terminal_01x03_1_1"
        (pin passive line (at -5.08 0 0) (length 2.54) (name "Pin_1" (effects (font (size 1.27 1.27)))) (number "1" (effects (font (size 1.27 1.27)))))
        (pin passive line (at 5.08 0 180) (length 2.54) (name "Pin_2" (effects (font (size 1.27 1.27)))) (number "2" (effects (font (size 1.27 1.27)))))
        (pin passive line (at 0 -5.08 90) (length 2.54) (name "Pin_3" (effects (font (size 1.27 1.27)))) (number "3" (effects (font (size 1.27 1.27)))))
      )
    )

    (symbol "Device:LED" (pin_numbers hide) (pin_names (offset 1.016) hide) (exclude_from_sim no) (in_bom yes) (on_board yes)
      (property "Reference" "D" (at 0 3.175 0) (effects (font (size 1.27 1.27))))
      (property "Value" "LED" (at 0 -3.175 0) (effects (font (size 1.27 1.27))))
      (property "Footprint" "LED_SMD:LED_0603_1608Metric" (at 0 0 0) (effects (font (size 1.27 1.27)) hide))
      (property "Datasheet" "" (at 0 0 0) (effects (font (size 1.27 1.27)) hide))
      (symbol "LED_0_1"
        (polyline (pts (xy -1.27 -1.27) (xy -1.27 1.27)) (stroke (width 0.254) (type default)) (fill (type none)))
        (polyline (pts (xy -1.27 0) (xy 1.27 0)) (stroke (width 0) (type default)) (fill (type none)))
        (polyline (pts (xy 1.27 -1.27) (xy 1.27 1.27) (xy -1.27 0) (xy 1.27 -1.27)) (stroke (width 0.254) (type default)) (fill (type none)))
        (polyline (pts (xy -0.508 -1.778) (xy 0.762 -3.048)) (stroke (width 0) (type default)) (fill (type none)))
        (polyline (pts (xy 0.254 -1.778) (xy 1.524 -3.048)) (stroke (width 0) (type default)) (fill (type none)))
      )
      (symbol "LED_1_1"
        (pin passive line (at -3.81 0 0) (length 2.54) (name "K" (effects (font (size 1.27 1.27)))) (number "1" (effects (font (size 1.27 1.27)))))
        (pin passive line (at 3.81 0 180) (length 2.54) (name "A" (effects (font (size 1.27 1.27)))) (number "2" (effects (font (size 1.27 1.27)))))
      )
    )

    (symbol "Device:R" (pin_numbers hide) (pin_names (offset 0)) (exclude_from_sim no) (in_bom yes) (on_board yes)
      (property "Reference" "R" (at 2.032 0 90) (effects (font (size 1.27 1.27))))
      (property "Value" "R" (at 0 0 90) (effects (font (size 1.27 1.27))))
      (property "Footprint" "" (at -1.778 0 90) (effects (font (size 1.27 1.27)) hide))
      (property "Datasheet" "" (at 0 0 0) (effects (font (size 1.27 1.27)) hide))
      (symbol "R_0_1"
        (rectangle (start -1.016 -2.54) (end 1.016 2.54) (stroke (width 0.254) (type default)) (fill (type none)))
      )
      (symbol "R_1_1"
        (pin passive line (at 0 3.81 270) (length 1.27) (name "~" (effects (font (size 1.27 1.27)))) (number "1" (effects (font (size 1.27 1.27)))))
        (pin passive line (at 0 -3.81 90) (length 1.27) (name "~" (effects (font (size 1.27 1.27)))) (number "2" (effects (font (size 1.27 1.27)))))
      )
    )

    (symbol "Device:C" (pin_numbers hide) (pin_names (offset 0.254)) (exclude_from_sim no) (in_bom yes) (on_board yes)
      (property "Reference" "C" (at 0.635 2.54 0) (effects (font (size 1.27 1.27)) (justify left)))
      (property "Value" "C" (at 0.635 -2.54 0) (effects (font (size 1.27 1.27)) (justify left)))
      (property "Footprint" "" (at 0.9652 -3.81 0) (effects (font (size 1.27 1.27)) hide))
      (property "Datasheet" "" (at 0 0 0) (effects (font (size 1.27 1.27)) hide))
      (symbol "C_0_1"
        (polyline (pts (xy -2.032 -0.762) (xy 2.032 -0.762)) (stroke (width 0.508) (type default)) (fill (type none)))
        (polyline (pts (xy -2.032 0.762) (xy 2.032 0.762)) (stroke (width 0.508) (type default)) (fill (type none)))
      )
      (symbol "C_1_1"
        (pin passive line (at 0 3.81 270) (length 2.794) (name "~" (effects (font (size 1.27 1.27)))) (number "1" (effects (font (size 1.27 1.27)))))
        (pin passive line (at 0 -3.81 90) (length 2.794) (name "~" (effects (font (size 1.27 1.27)))) (number "2" (effects (font (size 1.27 1.27)))))
      )
    )

    (symbol "Switch:SW_Push" (pin_numbers hide) (pin_names (offset 1.016) hide) (exclude_from_sim no) (in_bom yes) (on_board yes)
      (property "Reference" "SW" (at 1.27 6.35 0) (effects (font (size 1.27 1.27)) (justify left)))
      (property "Value" "SW_Push" (at 0 -1.524 0) (effects (font (size 1.27 1.27))))
      (property "Footprint" "Button_Switch_SMD:SW_Push_1P1T_NO_6x6mm_H9.5mm" (at 0 5.08 0) (effects (font (size 1.27 1.27)) hide))
      (property "Datasheet" "" (at 0 5.08 0) (effects (font (size 1.27 1.27)) hide))
      (symbol "SW_Push_0_1"
        (circle (center -2.032 0) (radius 0.508) (stroke (width 0) (type default)) (fill (type none)))
        (polyline (pts (xy 0 1.27) (xy 0 3.048)) (stroke (width 0) (type default)) (fill (type none)))
        (polyline (pts (xy 2.54 1.27) (xy -2.54 1.27)) (stroke (width 0) (type default)) (fill (type none)))
        (circle (center 2.032 0) (radius 0.508) (stroke (width 0) (type default)) (fill (type none)))
        (pin passive line (at -5.08 0 0) (length 2.54) (name "1" (effects (font (size 1.27 1.27)))) (number "1" (effects (font (size 1.27 1.27)))))
        (pin passive line (at 5.08 0 180) (length 2.54) (name "2" (effects (font (size 1.27 1.27)))) (number "2" (effects (font (size 1.27 1.27)))))
      )
    )

    (symbol "power:+5V" (power) (pin_numbers hide) (pin_names (offset 0) hide) (exclude_from_sim no) (in_bom yes) (on_board yes)
      (property "Reference" "#PWR" (at 0 -3.81 0) (effects (font (size 1.27 1.27)) hide))
      (property "Value" "+5V" (at 0 3.556 0) (effects (font (size 1.27 1.27))))
      (property "Footprint" "" (at 0 0 0) (effects (font (size 1.27 1.27)) hide))
      (property "Datasheet" "" (at 0 0 0) (effects (font (size 1.27 1.27)) hide))
      (symbol "+5V_0_1"
        (polyline (pts (xy -0.762 1.27) (xy 0 2.54)) (stroke (width 0) (type default)) (fill (type none)))
        (polyline (pts (xy 0 0) (xy 0 2.54)) (stroke (width 0) (type default)) (fill (type none)))
        (polyline (pts (xy 0 2.54) (xy 0.762 1.27)) (stroke (width 0) (type default)) (fill (type none)))
      )
      (symbol "+5V_1_1"
        (pin power_in line (at 0 0 90) (length 0) (name "+5V" (effects (font (size 1.27 1.27)))) (number "1" (effects (font (size 1.27 1.27)))))
      )
    )

    (symbol "power:+3V3" (power) (pin_numbers hide) (pin_names (offset 0) hide) (exclude_from_sim no) (in_bom yes) (on_board yes)
      (property "Reference" "#PWR" (at 0 -3.81 0) (effects (font (size 1.27 1.27)) hide))
      (property "Value" "+3V3" (at 0 3.556 0) (effects (font (size 1.27 1.27))))
      (property "Footprint" "" (at 0 0 0) (effects (font (size 1.27 1.27)) hide))
      (property "Datasheet" "" (at 0 0 0) (effects (font (size 1.27 1.27)) hide))
      (symbol "+3V3_0_1"
        (polyline (pts (xy -0.762 1.27) (xy 0 2.54)) (stroke (width 0) (type default)) (fill (type none)))
        (polyline (pts (xy 0 0) (xy 0 2.54)) (stroke (width 0) (type default)) (fill (type none)))
        (polyline (pts (xy 0 2.54) (xy 0.762 1.27)) (stroke (width 0) (type default)) (fill (type none)))
      )
      (symbol "+3V3_1_1"
        (pin power_in line (at 0 0 90) (length 0) (name "+3V3" (effects (font (size 1.27 1.27)))) (number "1" (effects (font (size 1.27 1.27)))))
      )
    )

    (symbol "power:GND" (power) (pin_numbers hide) (pin_names (offset 0) hide) (exclude_from_sim no) (in_bom yes) (on_board yes)
      (property "Reference" "#PWR" (at 0 -6.35 0) (effects (font (size 1.27 1.27)) hide))
      (property "Value" "GND" (at 0 -3.81 0) (effects (font (size 1.27 1.27))))
      (property "Footprint" "" (at 0 0 0) (effects (font (size 1.27 1.27)) hide))
      (property "Datasheet" "" (at 0 0 0) (effects (font (size 1.27 1.27)) hide))
      (symbol "GND_0_1"
        (polyline (pts (xy 0 0) (xy 0 -1.27) (xy 1.27 -1.27) (xy 0 -2.54) (xy -1.27 -1.27) (xy 0 -1.27)) (stroke (width 0) (type default)) (fill (type none)))
      )
      (symbol "GND_1_1"
        (pin power_in line (at 0 0 270) (length 0) (name "GND" (effects (font (size 1.27 1.27)))) (number "1" (effects (font (size 1.27 1.27)))))
      )
    )
'''
    return symbols

def generate_components():
    """컴포넌트 배치"""

    components = f'''
  (symbol
    (lib_id "Connector:MicroSD_Card")
    (at 63.5 55.88 0)
    (unit 1)
    (exclude_from_sim no)
    (in_bom yes)
    (on_board yes)
    (dnp no)
    (uuid "{gen_uuid()}")
    (property "Reference" "J9" (at 63.5 38.1 0) (effects (font (size 1.27 1.27))))
    (property "Value" "MicroSD" (at 63.5 40.64 0) (effects (font (size 1.27 1.27))))
    (property "Footprint" "Connector_Card:microSD_HC_Wuerth_693072010801" (at 63.5 55.88 0) (effects (font (size 1.27 1.27)) hide))
    (property "Datasheet" "" (at 63.5 55.88 0) (effects (font (size 1.27 1.27)) hide))
    (pin "1" (uuid "{gen_uuid()}"))
    (pin "2" (uuid "{gen_uuid()}"))
    (pin "3" (uuid "{gen_uuid()}"))
    (pin "4" (uuid "{gen_uuid()}"))
    (pin "5" (uuid "{gen_uuid()}"))
    (pin "6" (uuid "{gen_uuid()}"))
    (pin "7" (uuid "{gen_uuid()}"))
    (pin "8" (uuid "{gen_uuid()}"))
    (pin "9" (uuid "{gen_uuid()}"))
  )

  (symbol
    (lib_id "Connector:USB_B_Micro")
    (at 165.1 55.88 0)
    (unit 1)
    (exclude_from_sim no)
    (in_bom yes)
    (on_board yes)
    (dnp no)
    (uuid "{gen_uuid()}")
    (property "Reference" "J10" (at 165.1 46.99 0) (effects (font (size 1.27 1.27))))
    (property "Value" "USB_Debug" (at 165.1 49.53 0) (effects (font (size 1.27 1.27))))
    (property "Footprint" "Connector_USB:USB_Micro-B_Molex_47346-0001" (at 165.1 55.88 0) (effects (font (size 1.27 1.27)) hide))
    (property "Datasheet" "" (at 165.1 55.88 0) (effects (font (size 1.27 1.27)) hide))
    (pin "1" (uuid "{gen_uuid()}"))
    (pin "2" (uuid "{gen_uuid()}"))
    (pin "3" (uuid "{gen_uuid()}"))
    (pin "4" (uuid "{gen_uuid()}"))
    (pin "5" (uuid "{gen_uuid()}"))
  )

  (symbol
    (lib_id "Interface_USB:CP2102N")
    (at 213.36 55.88 0)
    (unit 1)
    (exclude_from_sim no)
    (in_bom yes)
    (on_board yes)
    (dnp no)
    (uuid "{gen_uuid()}")
    (property "Reference" "U1" (at 213.36 36.83 0) (effects (font (size 1.27 1.27))))
    (property "Value" "CP2102N" (at 213.36 39.37 0) (effects (font (size 1.27 1.27))))
    (property "Footprint" "Package_DFN_QFN:QFN-28-1EP_5x5mm_P0.5mm_EP3.35x3.35mm" (at 213.36 55.88 0) (effects (font (size 1.27 1.27)) hide))
    (property "Datasheet" "" (at 213.36 55.88 0) (effects (font (size 1.27 1.27)) hide))
    (pin "1" (uuid "{gen_uuid()}"))
    (pin "2" (uuid "{gen_uuid()}"))
    (pin "3" (uuid "{gen_uuid()}"))
    (pin "4" (uuid "{gen_uuid()}"))
    (pin "5" (uuid "{gen_uuid()}"))
    (pin "6" (uuid "{gen_uuid()}"))
    (pin "7" (uuid "{gen_uuid()}"))
    (pin "8" (uuid "{gen_uuid()}"))
    (pin "9" (uuid "{gen_uuid()}"))
    (pin "10" (uuid "{gen_uuid()}"))
  )

  (symbol
    (lib_id "Interface_CAN_LIN:SN65HVD230")
    (at 63.5 119.38 0)
    (unit 1)
    (exclude_from_sim no)
    (in_bom yes)
    (on_board yes)
    (dnp no)
    (uuid "{gen_uuid()}")
    (property "Reference" "U2" (at 63.5 106.68 0) (effects (font (size 1.27 1.27))))
    (property "Value" "SN65HVD230" (at 63.5 109.22 0) (effects (font (size 1.27 1.27))))
    (property "Footprint" "Package_SO:SOIC-8_3.9x4.9mm_P1.27mm" (at 63.5 119.38 0) (effects (font (size 1.27 1.27)) hide))
    (property "Datasheet" "" (at 63.5 119.38 0) (effects (font (size 1.27 1.27)) hide))
    (pin "1" (uuid "{gen_uuid()}"))
    (pin "2" (uuid "{gen_uuid()}"))
    (pin "3" (uuid "{gen_uuid()}"))
    (pin "4" (uuid "{gen_uuid()}"))
    (pin "5" (uuid "{gen_uuid()}"))
    (pin "6" (uuid "{gen_uuid()}"))
    (pin "7" (uuid "{gen_uuid()}"))
    (pin "8" (uuid "{gen_uuid()}"))
  )

  (symbol
    (lib_id "Interface_CAN_LIN:SN65HVD230")
    (at 63.5 154.94 0)
    (unit 1)
    (exclude_from_sim no)
    (in_bom yes)
    (on_board yes)
    (dnp no)
    (uuid "{gen_uuid()}")
    (property "Reference" "U3" (at 63.5 142.24 0) (effects (font (size 1.27 1.27))))
    (property "Value" "SN65HVD230" (at 63.5 144.78 0) (effects (font (size 1.27 1.27))))
    (property "Footprint" "Package_SO:SOIC-8_3.9x4.9mm_P1.27mm" (at 63.5 154.94 0) (effects (font (size 1.27 1.27)) hide))
    (property "Datasheet" "" (at 63.5 154.94 0) (effects (font (size 1.27 1.27)) hide))
    (pin "1" (uuid "{gen_uuid()}"))
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
    (property "Footprint" "Resistor_SMD:R_0402_1005Metric" (at 101.6 202.438 90) (effects (font (size 1.27 1.27)) hide))
    (property "Datasheet" "" (at 101.6 200.66 0) (effects (font (size 1.27 1.27)) hide))
    (pin "1" (uuid "{gen_uuid()}"))
    (pin "2" (uuid "{gen_uuid()}"))
  )

  (symbol
    (lib_id "Device:R")
    (at 127 200.66 90)
    (unit 1)
    (exclude_from_sim no)
    (in_bom yes)
    (on_board yes)
    (dnp no)
    (uuid "{gen_uuid()}")
    (property "Reference" "R4" (at 127 198.12 90) (effects (font (size 1.27 1.27))))
    (property "Value" "470R" (at 127 200.66 90) (effects (font (size 1.27 1.27))))
    (property "Footprint" "Resistor_SMD:R_0402_1005Metric" (at 127 202.438 90) (effects (font (size 1.27 1.27)) hide))
    (property "Datasheet" "" (at 127 200.66 0) (effects (font (size 1.27 1.27)) hide))
    (pin "1" (uuid "{gen_uuid()}"))
    (pin "2" (uuid "{gen_uuid()}"))
  )

  (symbol
    (lib_id "Switch:SW_Push")
    (at 180.34 200.66 0)
    (unit 1)
    (exclude_from_sim no)
    (in_bom yes)
    (on_board yes)
    (dnp no)
    (uuid "{gen_uuid()}")
    (property "Reference" "SW1" (at 180.34 193.04 0) (effects (font (size 1.27 1.27))))
    (property "Value" "BTN0" (at 180.34 195.58 0) (effects (font (size 1.27 1.27))))
    (property "Footprint" "Button_Switch_SMD:SW_Push_1P1T_NO_6x6mm_H9.5mm" (at 180.34 195.58 0) (effects (font (size 1.27 1.27)) hide))
    (property "Datasheet" "" (at 180.34 195.58 0) (effects (font (size 1.27 1.27)) hide))
    (pin "1" (uuid "{gen_uuid()}"))
    (pin "2" (uuid "{gen_uuid()}"))
  )

  (symbol
    (lib_id "Switch:SW_Push")
    (at 213.36 200.66 0)
    (unit 1)
    (exclude_from_sim no)
    (in_bom yes)
    (on_board yes)
    (dnp no)
    (uuid "{gen_uuid()}")
    (property "Reference" "SW2" (at 213.36 193.04 0) (effects (font (size 1.27 1.27))))
    (property "Value" "BTN1" (at 213.36 195.58 0) (effects (font (size 1.27 1.27))))
    (property "Footprint" "Button_Switch_SMD:SW_Push_1P1T_NO_6x6mm_H9.5mm" (at 213.36 195.58 0) (effects (font (size 1.27 1.27)) hide))
    (property "Datasheet" "" (at 213.36 195.58 0) (effects (font (size 1.27 1.27)) hide))
    (pin "1" (uuid "{gen_uuid()}"))
    (pin "2" (uuid "{gen_uuid()}"))
  )

  (symbol
    (lib_id "Device:C")
    (at 195.58 55.88 0)
    (unit 1)
    (exclude_from_sim no)
    (in_bom yes)
    (on_board yes)
    (dnp no)
    (uuid "{gen_uuid()}")
    (property "Reference" "C1" (at 198.12 54.61 0) (effects (font (size 1.27 1.27)) (justify left)))
    (property "Value" "100nF" (at 198.12 57.15 0) (effects (font (size 1.27 1.27)) (justify left)))
    (property "Footprint" "Capacitor_SMD:C_0402_1005Metric" (at 196.5452 59.69 0) (effects (font (size 1.27 1.27)) hide))
    (property "Datasheet" "" (at 195.58 55.88 0) (effects (font (size 1.27 1.27)) hide))
    (pin "1" (uuid "{gen_uuid()}"))
    (pin "2" (uuid "{gen_uuid()}"))
  )
'''
    return components

def generate_wires():
    """와이어 연결"""

    wires = f'''
  (wire
    (pts (xy 53.34 48.26) (xy 40.64 48.26))
    (stroke (width 0) (type default))
    (uuid "{gen_uuid()}")
  )

  (wire
    (pts (xy 53.34 50.8) (xy 40.64 50.8))
    (stroke (width 0) (type default))
    (uuid "{gen_uuid()}")
  )

  (wire
    (pts (xy 53.34 53.34) (xy 40.64 53.34))
    (stroke (width 0) (type default))
    (uuid "{gen_uuid()}")
  )

  (wire
    (pts (xy 53.34 58.42) (xy 40.64 58.42))
    (stroke (width 0) (type default))
    (uuid "{gen_uuid()}")
  )

  (wire
    (pts (xy 53.34 63.5) (xy 40.64 63.5))
    (stroke (width 0) (type default))
    (uuid "{gen_uuid()}")
  )

  (wire
    (pts (xy 73.66 48.26) (xy 86.36 48.26))
    (stroke (width 0) (type default))
    (uuid "{gen_uuid()}")
  )

  (wire
    (pts (xy 172.72 55.88) (xy 182.88 55.88))
    (stroke (width 0) (type default))
    (uuid "{gen_uuid()}")
  )

  (wire
    (pts (xy 182.88 55.88) (xy 182.88 53.34))
    (stroke (width 0) (type default))
    (uuid "{gen_uuid()}")
  )
  (wire
    (pts (xy 182.88 53.34) (xy 200.66 53.34))
    (stroke (width 0) (type default))
    (uuid "{gen_uuid()}")
  )

  (wire
    (pts (xy 172.72 58.42) (xy 185.42 58.42))
    (stroke (width 0) (type default))
    (uuid "{gen_uuid()}")
  )
  (wire
    (pts (xy 185.42 58.42) (xy 185.42 60.96))
    (stroke (width 0) (type default))
    (uuid "{gen_uuid()}")
  )
  (wire
    (pts (xy 185.42 60.96) (xy 200.66 60.96))
    (stroke (width 0) (type default))
    (uuid "{gen_uuid()}")
  )

  (wire
    (pts (xy 225.98 45.72) (xy 241.3 45.72))
    (stroke (width 0) (type default))
    (uuid "{gen_uuid()}")
  )

  (wire
    (pts (xy 225.98 48.26) (xy 241.3 48.26))
    (stroke (width 0) (type default))
    (uuid "{gen_uuid()}")
  )

  (wire
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
    (shape input)
    (at 27.94 154.94 180)
    (effects (font (size 1.27 1.27)) (justify right))
    (uuid "{gen_uuid()}")
  )

  (hierarchical_label "USER_LED[0..3]"
    (shape input)
    (at 27.94 200.66 180)
    (effects (font (size 1.27 1.27)) (justify right))
    (uuid "{gen_uuid()}")
  )

  (hierarchical_label "USER_BTN[0..1]"
    (shape output)
    (at 236.22 200.66 0)
    (effects (font (size 1.27 1.27)) (justify left))
    (uuid "{gen_uuid()}")
  )

  (hierarchical_label "+5V"
    (shape input)
    (at 27.94 30.48 180)
    (effects (font (size 1.27 1.27)) (justify right))
    (uuid "{gen_uuid()}")
  )

  (hierarchical_label "+3V3"
    (shape input)
    (at 27.94 35.56 180)
    (effects (font (size 1.27 1.27)) (justify right))
    (uuid "{gen_uuid()}")
  )

  (hierarchical_label "GND"
    (shape passive)
    (at 27.94 40.64 180)
    (effects (font (size 1.27 1.27)) (justify right))
    (uuid "{gen_uuid()}")
  )
'''
    return labels

def generate_power_symbols():
    """전원 심볼"""

    power = f'''
  (symbol
    (lib_id "power:+5V")
    (at 27.94 30.48 0)
    (unit 1)
    (exclude_from_sim no)
    (in_bom yes)
    (on_board yes)
    (dnp no)
    (uuid "{gen_uuid()}")
    (property "Reference" "#PWR01" (at 27.94 34.29 0) (effects (font (size 1.27 1.27)) hide))
    (property "Value" "+5V" (at 27.94 26.67 0) (effects (font (size 1.27 1.27))))
    (property "Footprint" "" (at 27.94 30.48 0) (effects (font (size 1.27 1.27)) hide))
    (property "Datasheet" "" (at 27.94 30.48 0) (effects (font (size 1.27 1.27)) hide))
    (pin "1" (uuid "{gen_uuid()}"))
  )

  (symbol
    (lib_id "power:+3V3")
    (at 27.94 35.56 0)
    (unit 1)
    (exclude_from_sim no)
    (in_bom yes)
    (on_board yes)
    (dnp no)
    (uuid "{gen_uuid()}")
    (property "Reference" "#PWR02" (at 27.94 39.37 0) (effects (font (size 1.27 1.27)) hide))
    (property "Value" "+3V3" (at 27.94 31.75 0) (effects (font (size 1.27 1.27))))
    (property "Footprint" "" (at 27.94 35.56 0) (effects (font (size 1.27 1.27)) hide))
    (property "Datasheet" "" (at 27.94 35.56 0) (effects (font (size 1.27 1.27)) hide))
    (pin "1" (uuid "{gen_uuid()}"))
  )

  (symbol
    (lib_id "power:+3V3")
    (at 53.34 55.88 0)
    (unit 1)
    (exclude_from_sim no)
    (in_bom yes)
    (on_board yes)
    (dnp no)
    (uuid "{gen_uuid()}")
    (property "Reference" "#PWR03" (at 53.34 59.69 0) (effects (font (size 1.27 1.27)) hide))
    (property "Value" "+3V3" (at 53.34 52.07 0) (effects (font (size 1.27 1.27))))
    (property "Footprint" "" (at 53.34 55.88 0) (effects (font (size 1.27 1.27)) hide))
    (property "Datasheet" "" (at 53.34 55.88 0) (effects (font (size 1.27 1.27)) hide))
    (pin "1" (uuid "{gen_uuid()}"))
  )

  (symbol
    (lib_id "power:+3V3")
    (at 73.62 116.84 0)
    (unit 1)
    (exclude_from_sim no)
    (in_bom yes)
    (on_board yes)
    (dnp no)
    (uuid "{gen_uuid()}")
    (property "Reference" "#PWR04" (at 73.62 120.65 0) (effects (font (size 1.27 1.27)) hide))
    (property "Value" "+3V3" (at 73.62 113.03 0) (effects (font (size 1.27 1.27))))
    (property "Footprint" "" (at 73.62 116.84 0) (effects (font (size 1.27 1.27)) hide))
    (property "Datasheet" "" (at 73.62 116.84 0) (effects (font (size 1.27 1.27)) hide))
    (pin "1" (uuid "{gen_uuid()}"))
  )

  (symbol
    (lib_id "power:+3V3")
    (at 73.62 152.4 0)
    (unit 1)
    (exclude_from_sim no)
    (in_bom yes)
    (on_board yes)
    (dnp no)
    (uuid "{gen_uuid()}")
    (property "Reference" "#PWR05" (at 73.62 156.21 0) (effects (font (size 1.27 1.27)) hide))
    (property "Value" "+3V3" (at 73.62 148.59 0) (effects (font (size 1.27 1.27))))
    (property "Footprint" "" (at 73.62 152.4 0) (effects (font (size 1.27 1.27)) hide))
    (property "Datasheet" "" (at 73.62 152.4 0) (effects (font (size 1.27 1.27)) hide))
    (pin "1" (uuid "{gen_uuid()}"))
  )

  (symbol
    (lib_id "power:+3V3")
    (at 175.26 121.92 0)
    (unit 1)
    (exclude_from_sim no)
    (in_bom yes)
    (on_board yes)
    (dnp no)
    (uuid "{gen_uuid()}")
    (property "Reference" "#PWR06" (at 175.26 125.73 0) (effects (font (size 1.27 1.27)) hide))
    (property "Value" "+3V3" (at 175.26 118.11 0) (effects (font (size 1.27 1.27))))
    (property "Footprint" "" (at 175.26 121.92 0) (effects (font (size 1.27 1.27)) hide))
    (property "Datasheet" "" (at 175.26 121.92 0) (effects (font (size 1.27 1.27)) hide))
    (pin "1" (uuid "{gen_uuid()}"))
  )

  (symbol
    (lib_id "power:+3V3")
    (at 175.26 157.48 0)
    (unit 1)
    (exclude_from_sim no)
    (in_bom yes)
    (on_board yes)
    (dnp no)
    (uuid "{gen_uuid()}")
    (property "Reference" "#PWR07" (at 175.26 161.29 0) (effects (font (size 1.27 1.27)) hide))
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
    (property "Footprint" "" (at 226.06 200.66 0) (effects (font (size 1.27 1.27)) hide))
    (property "Datasheet" "" (at 226.06 200.66 0) (effects (font (size 1.27 1.27)) hide))
    (pin "1" (uuid "{gen_uuid()}"))
  )

  (symbol
    (lib_id "power:GND")
    (at 101.6 121.92 0)
    (unit 1)
    (exclude_from_sim no)
    (in_bom yes)
    (on_board yes)
    (dnp no)
    (uuid "{gen_uuid()}")
    (property "Reference" "#PWR020" (at 101.6 128.27 0) (effects (font (size 1.27 1.27)) hide))
    (property "Value" "GND" (at 101.6 125.73 0) (effects (font (size 1.27 1.27))))
    (property "Footprint" "" (at 101.6 121.92 0) (effects (font (size 1.27 1.27)) hide))
    (property "Datasheet" "" (at 101.6 121.92 0) (effects (font (size 1.27 1.27)) hide))
    (pin "1" (uuid "{gen_uuid()}"))
  )

  (symbol
    (lib_id "power:GND")
    (at 101.6 157.48 0)
    (unit 1)
    (exclude_from_sim no)
    (in_bom yes)
    (on_board yes)
    (dnp no)
    (uuid "{gen_uuid()}")
    (property "Reference" "#PWR021" (at 101.6 163.83 0) (effects (font (size 1.27 1.27)) hide))
    (property "Value" "GND" (at 101.6 161.29 0) (effects (font (size 1.27 1.27))))
    (property "Footprint" "" (at 101.6 157.48 0) (effects (font (size 1.27 1.27)) hide))
    (property "Datasheet" "" (at 101.6 157.48 0) (effects (font (size 1.27 1.27)) hide))
    (pin "1" (uuid "{gen_uuid()}"))
  )

  (symbol
    (lib_id "power:GND")
    (at 203.2 121.92 0)
    (unit 1)
    (exclude_from_sim no)
    (in_bom yes)
    (on_board yes)
    (dnp no)
    (uuid "{gen_uuid()}")
    (property "Reference" "#PWR022" (at 203.2 128.27 0) (effects (font (size 1.27 1.27)) hide))
    (property "Value" "GND" (at 203.2 125.73 0) (effects (font (size 1.27 1.27))))
    (property "Footprint" "" (at 203.2 121.92 0) (effects (font (size 1.27 1.27)) hide))
    (property "Datasheet" "" (at 203.2 121.92 0) (effects (font (size 1.27 1.27)) hide))
    (pin "1" (uuid "{gen_uuid()}"))
  )

  (symbol
    (lib_id "power:GND")
    (at 203.2 157.48 0)
    (unit 1)
    (exclude_from_sim no)
    (in_bom yes)
    (on_board yes)
    (dnp no)
    (uuid "{gen_uuid()}")
    (property "Reference" "#PWR023" (at 203.2 163.83 0) (effects (font (size 1.27 1.27)) hide))
    (property "Value" "GND" (at 203.2 161.29 0) (effects (font (size 1.27 1.27))))
    (property "Footprint" "" (at 203.2 157.48 0) (effects (font (size 1.27 1.27)) hide))
    (property "Datasheet" "" (at 203.2 157.48 0) (effects (font (size 1.27 1.27)) hide))
    (pin "1" (uuid "{gen_uuid()}"))
  )
'''
    return power

def main():
    script_dir = os.path.dirname(os.path.abspath(__file__))
    project_dir = os.path.dirname(script_dir)
    output_path = os.path.join(project_dir, "fcBoard_Peripherals.kicad_sch")

    content = create_peripherals_schematic()

    with open(output_path, 'w', encoding='utf-8') as f:
        f.write(content)

    print(f"Peripherals schematic generated: {output_path}")
    print(f"File size: {os.path.getsize(output_path)} bytes")

if __name__ == "__main__":
    main()
